danwerner21/TI99_22/images/d.jpg

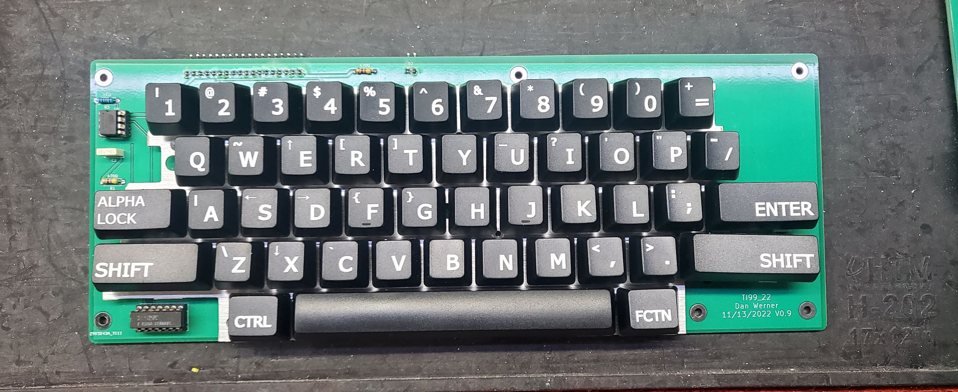
images/d.jpg
