danwerner21/TI99_22/IORiser/IO_Riser/IO_RISERPCBV0.5.pdf

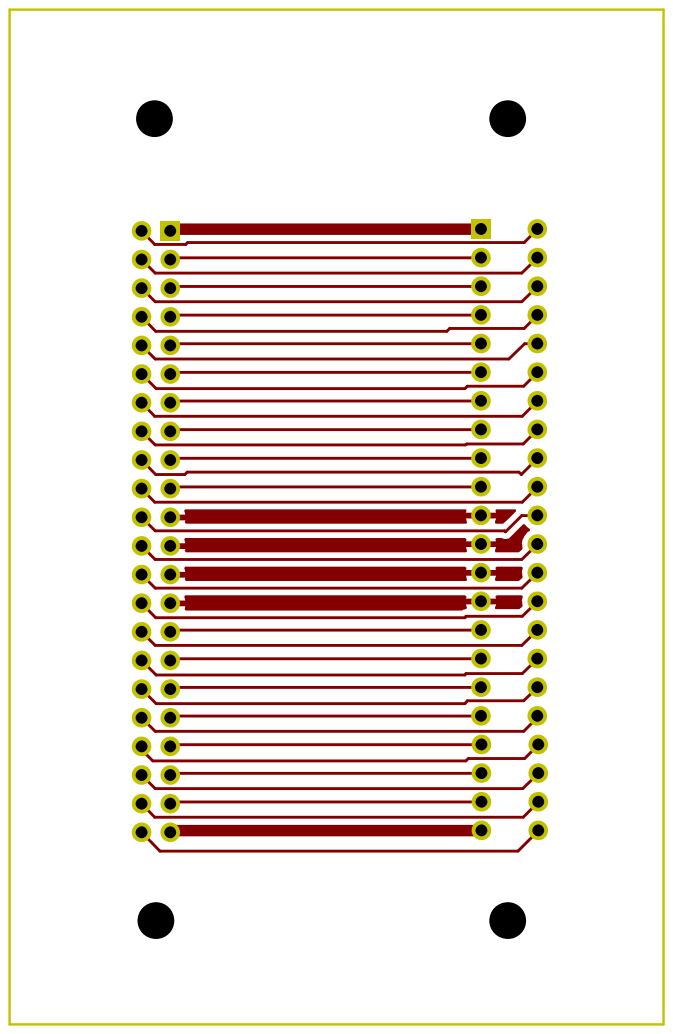
[picture p63: page 1]

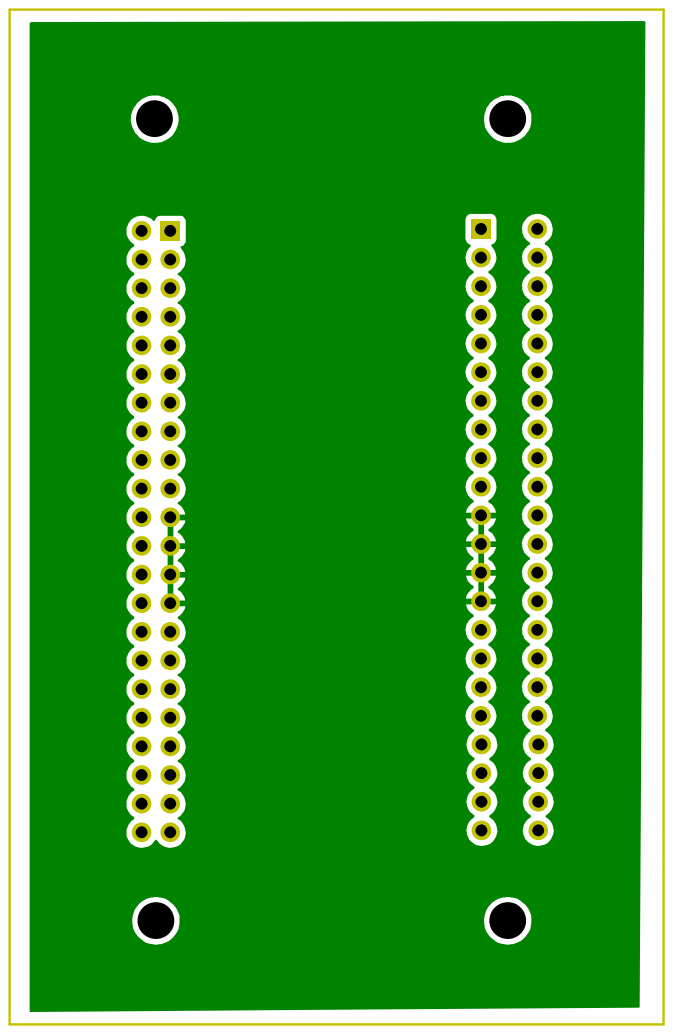
[picture p64: page 2]

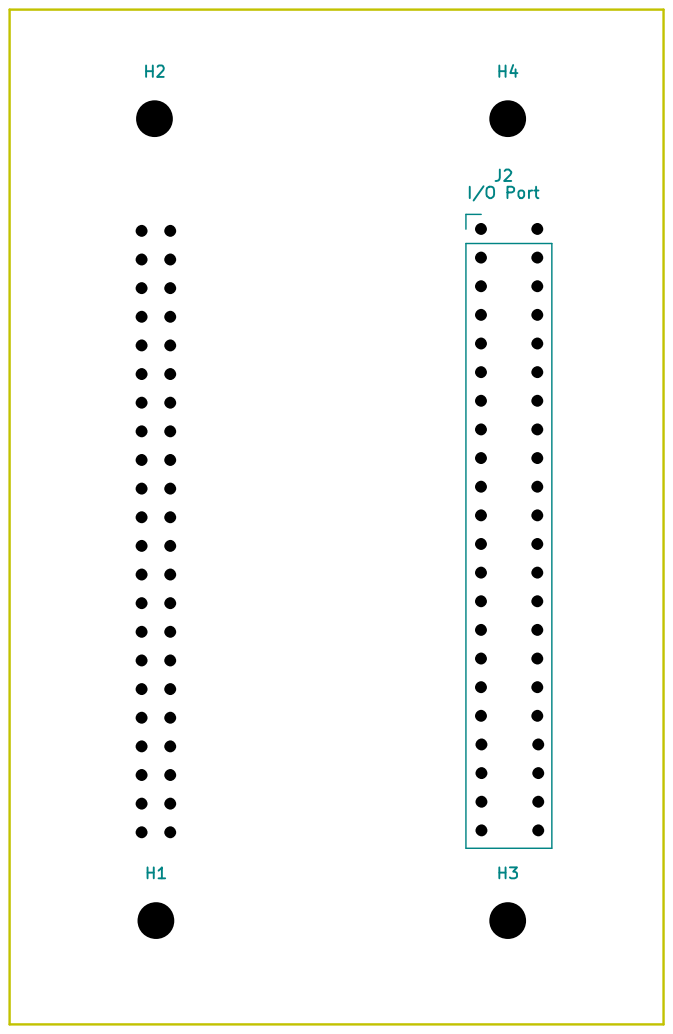
[picture p65: page 3]

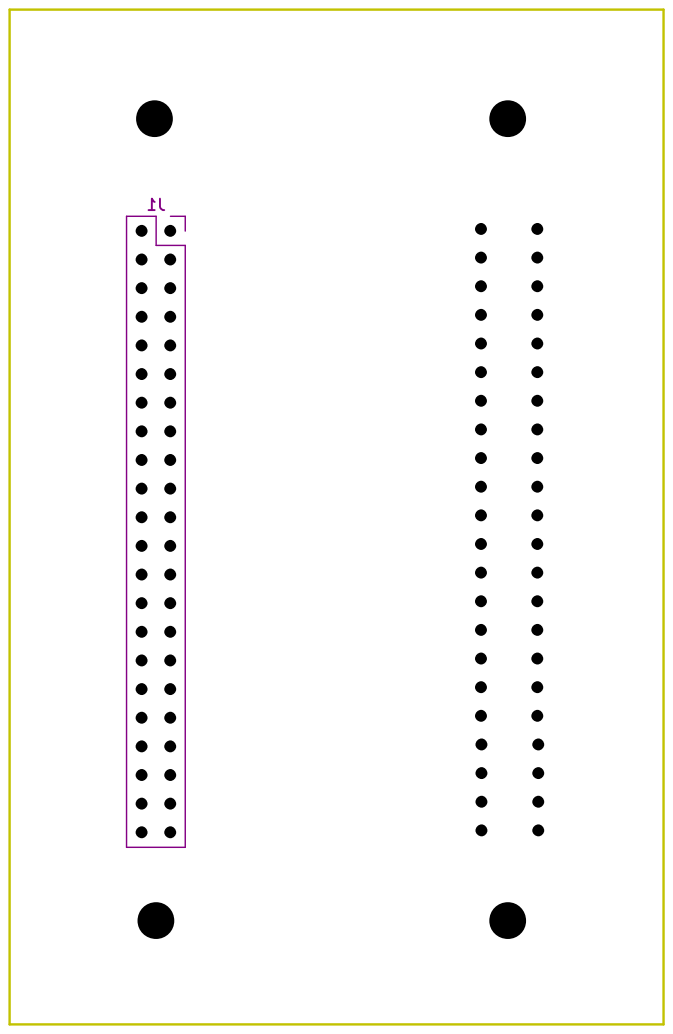
[picture p66: page 4]

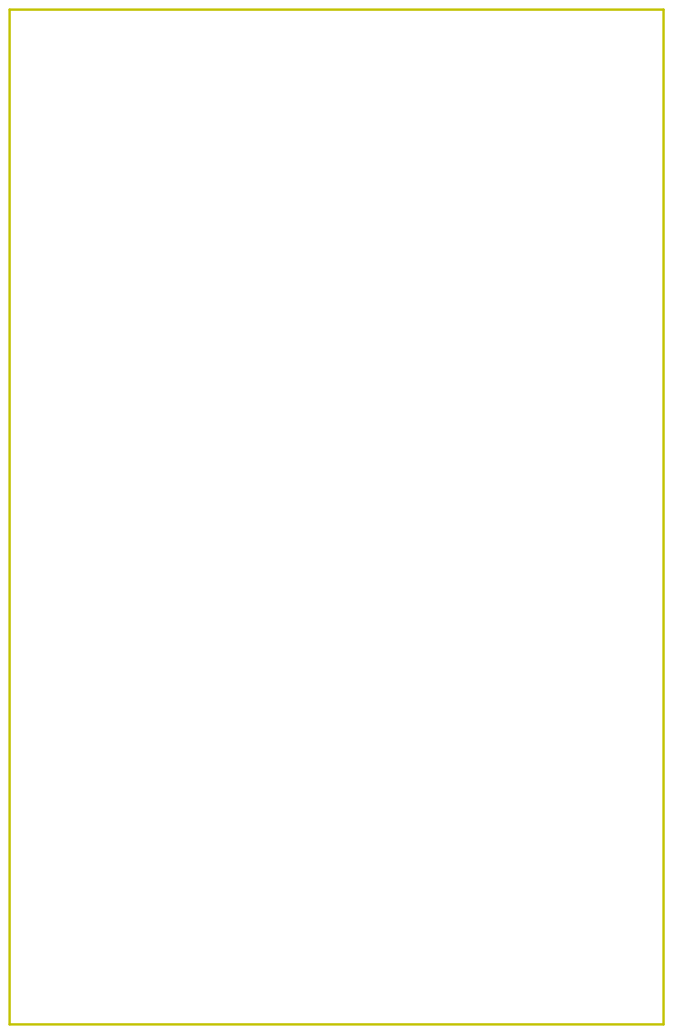
[picture p67: page 5]
