danwerner21/TI99_22/IORiser/IO_Riser/IO_RISERV0.5.pdf

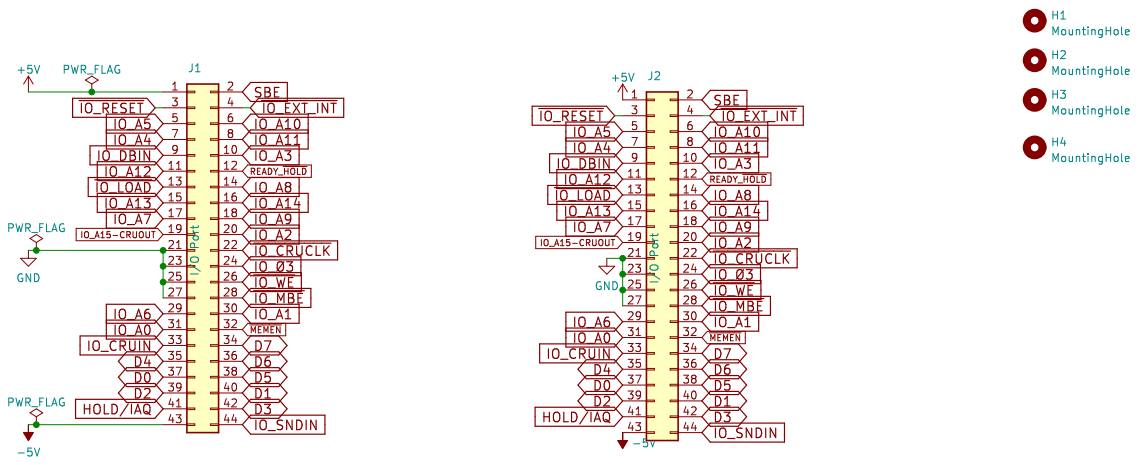
[picture p68: page 1]
