danwerner21/TI99_22/mainboard/mainboard_pcb_v0.95.pdf

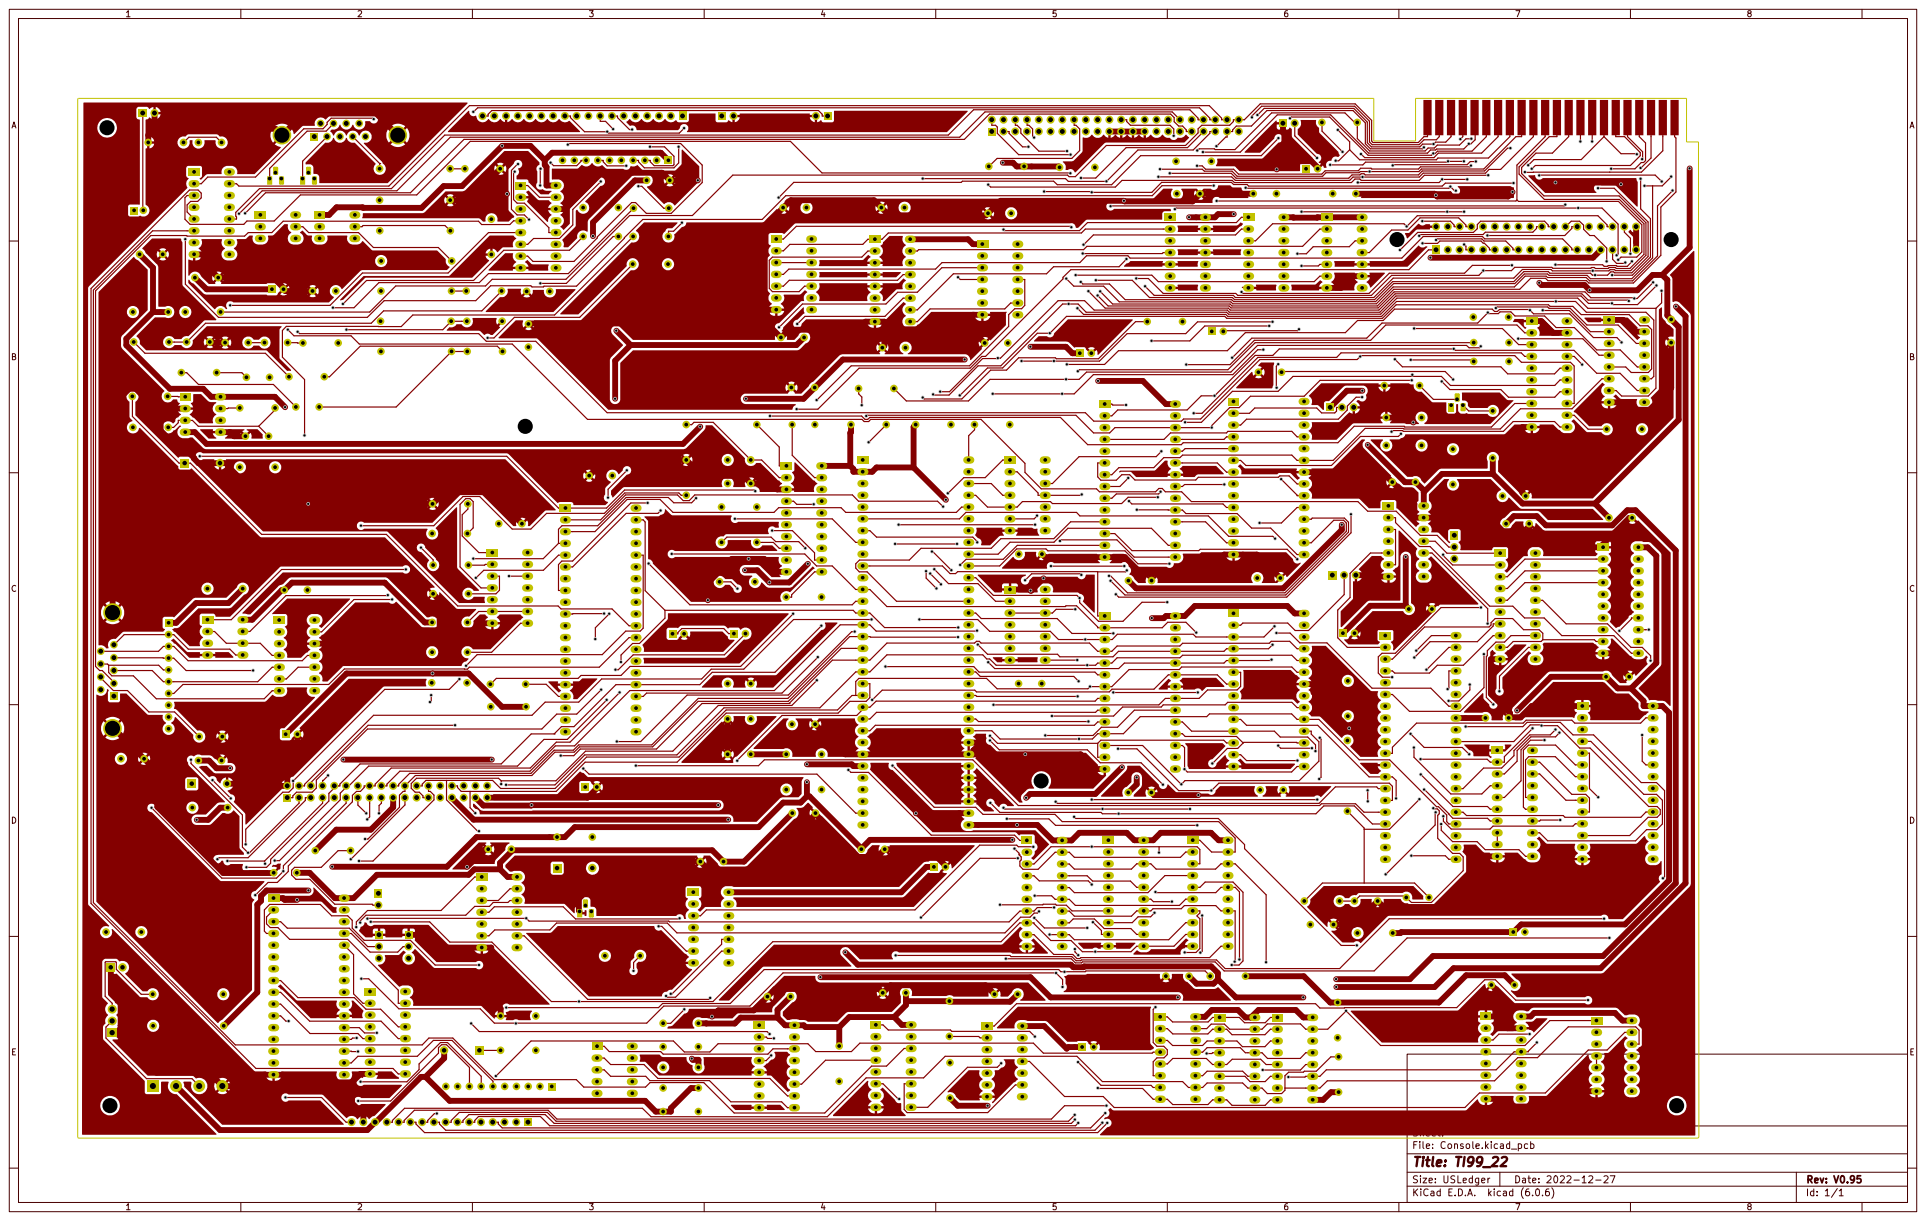
[picture p69: page 1]

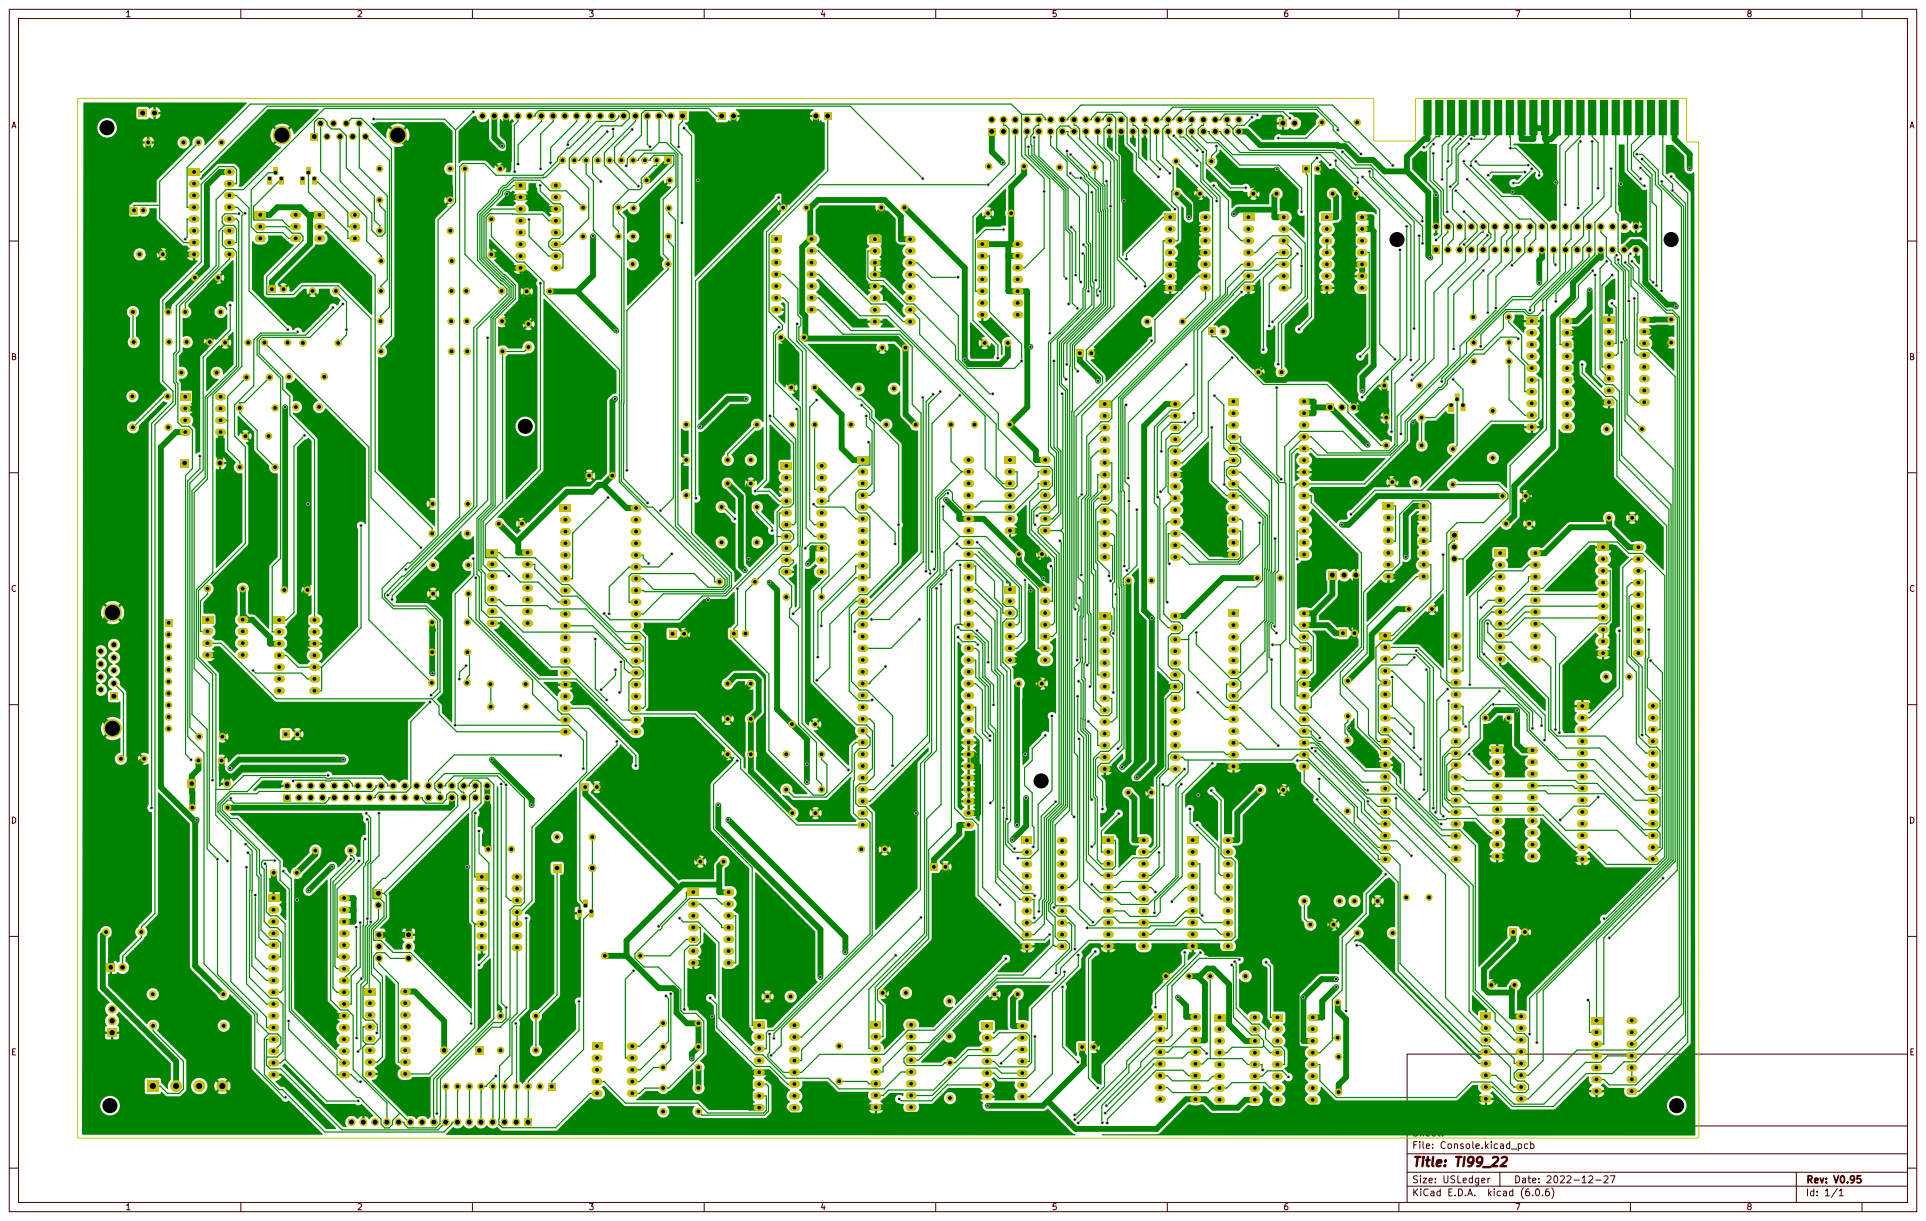
[picture p70: page 2]

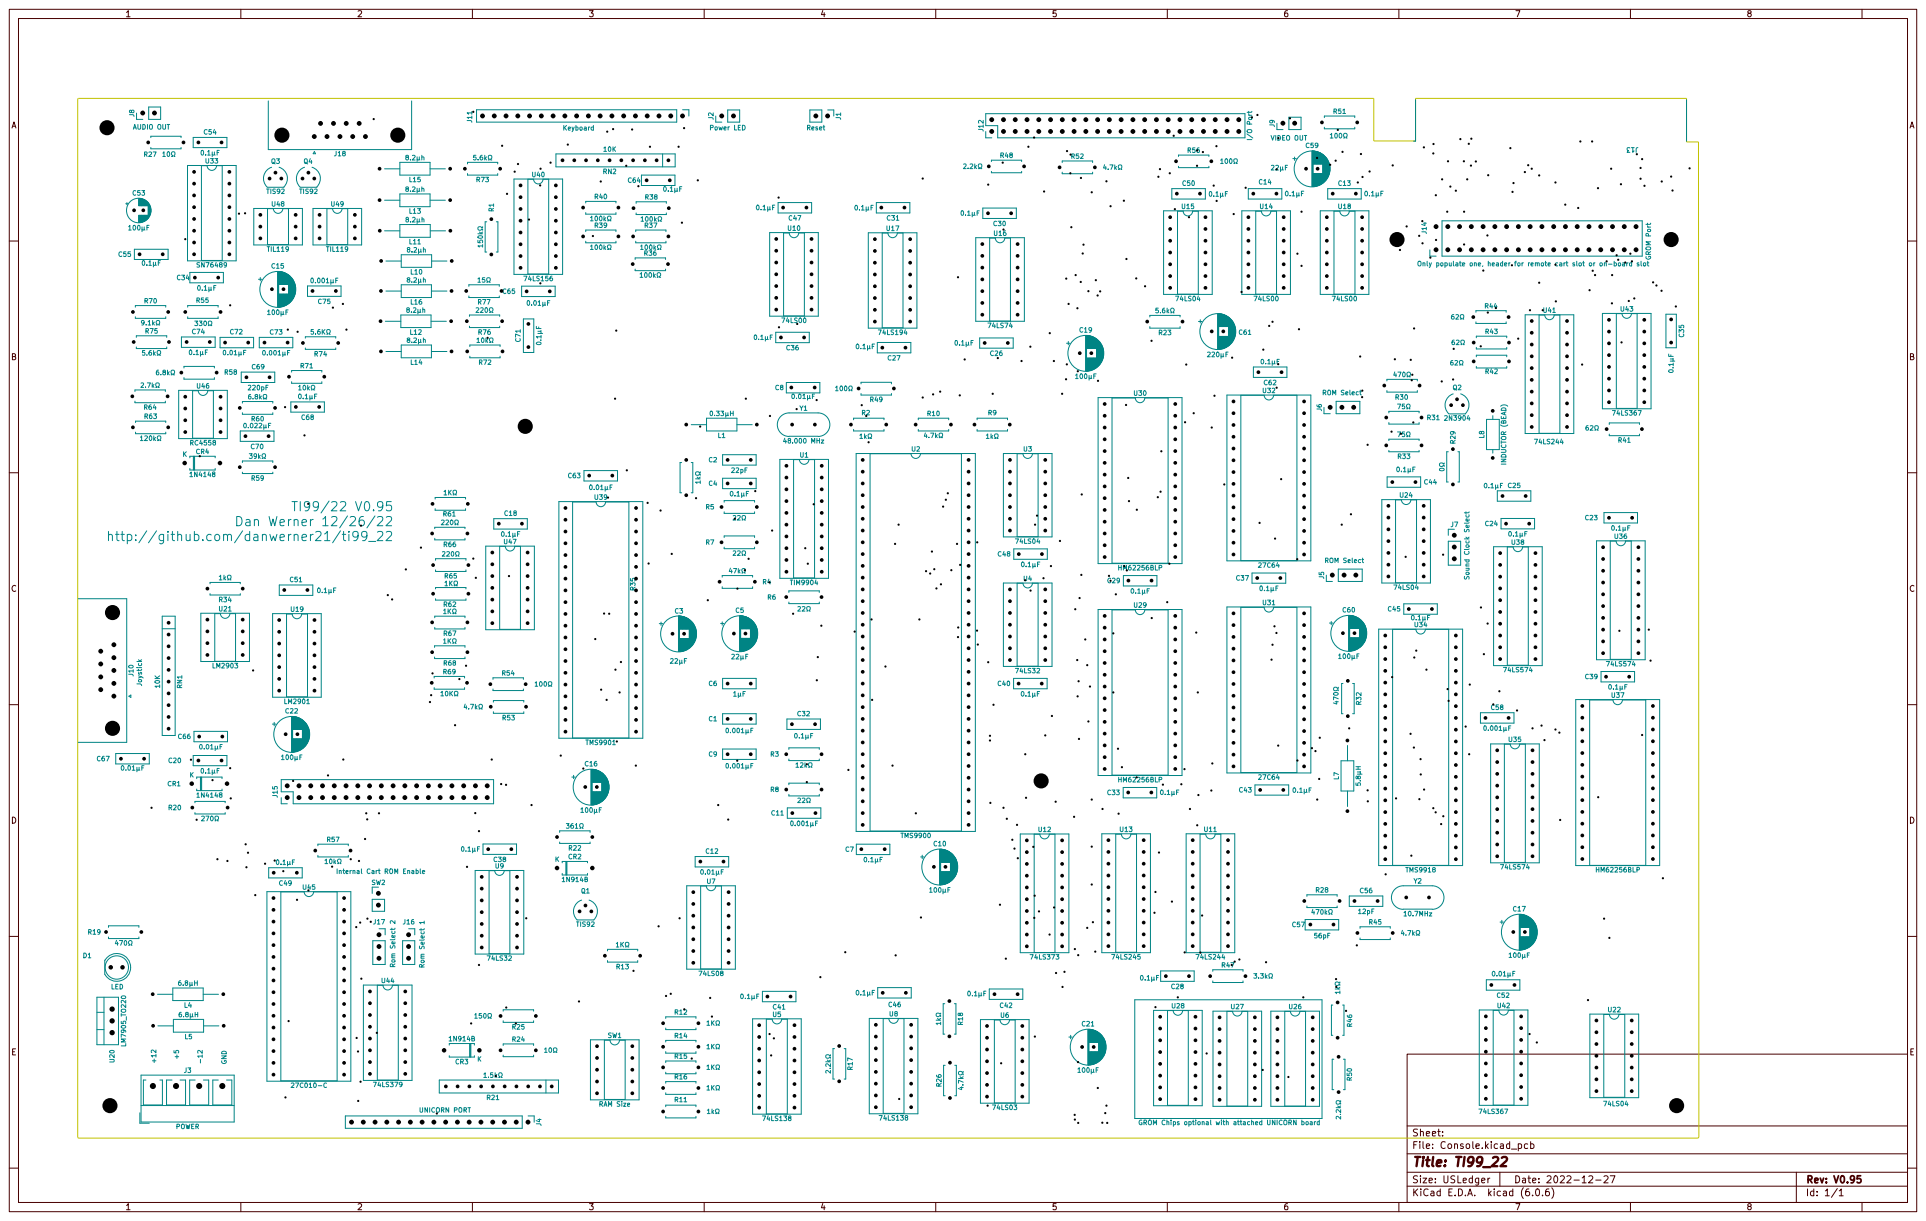
[picture p71: page 3]

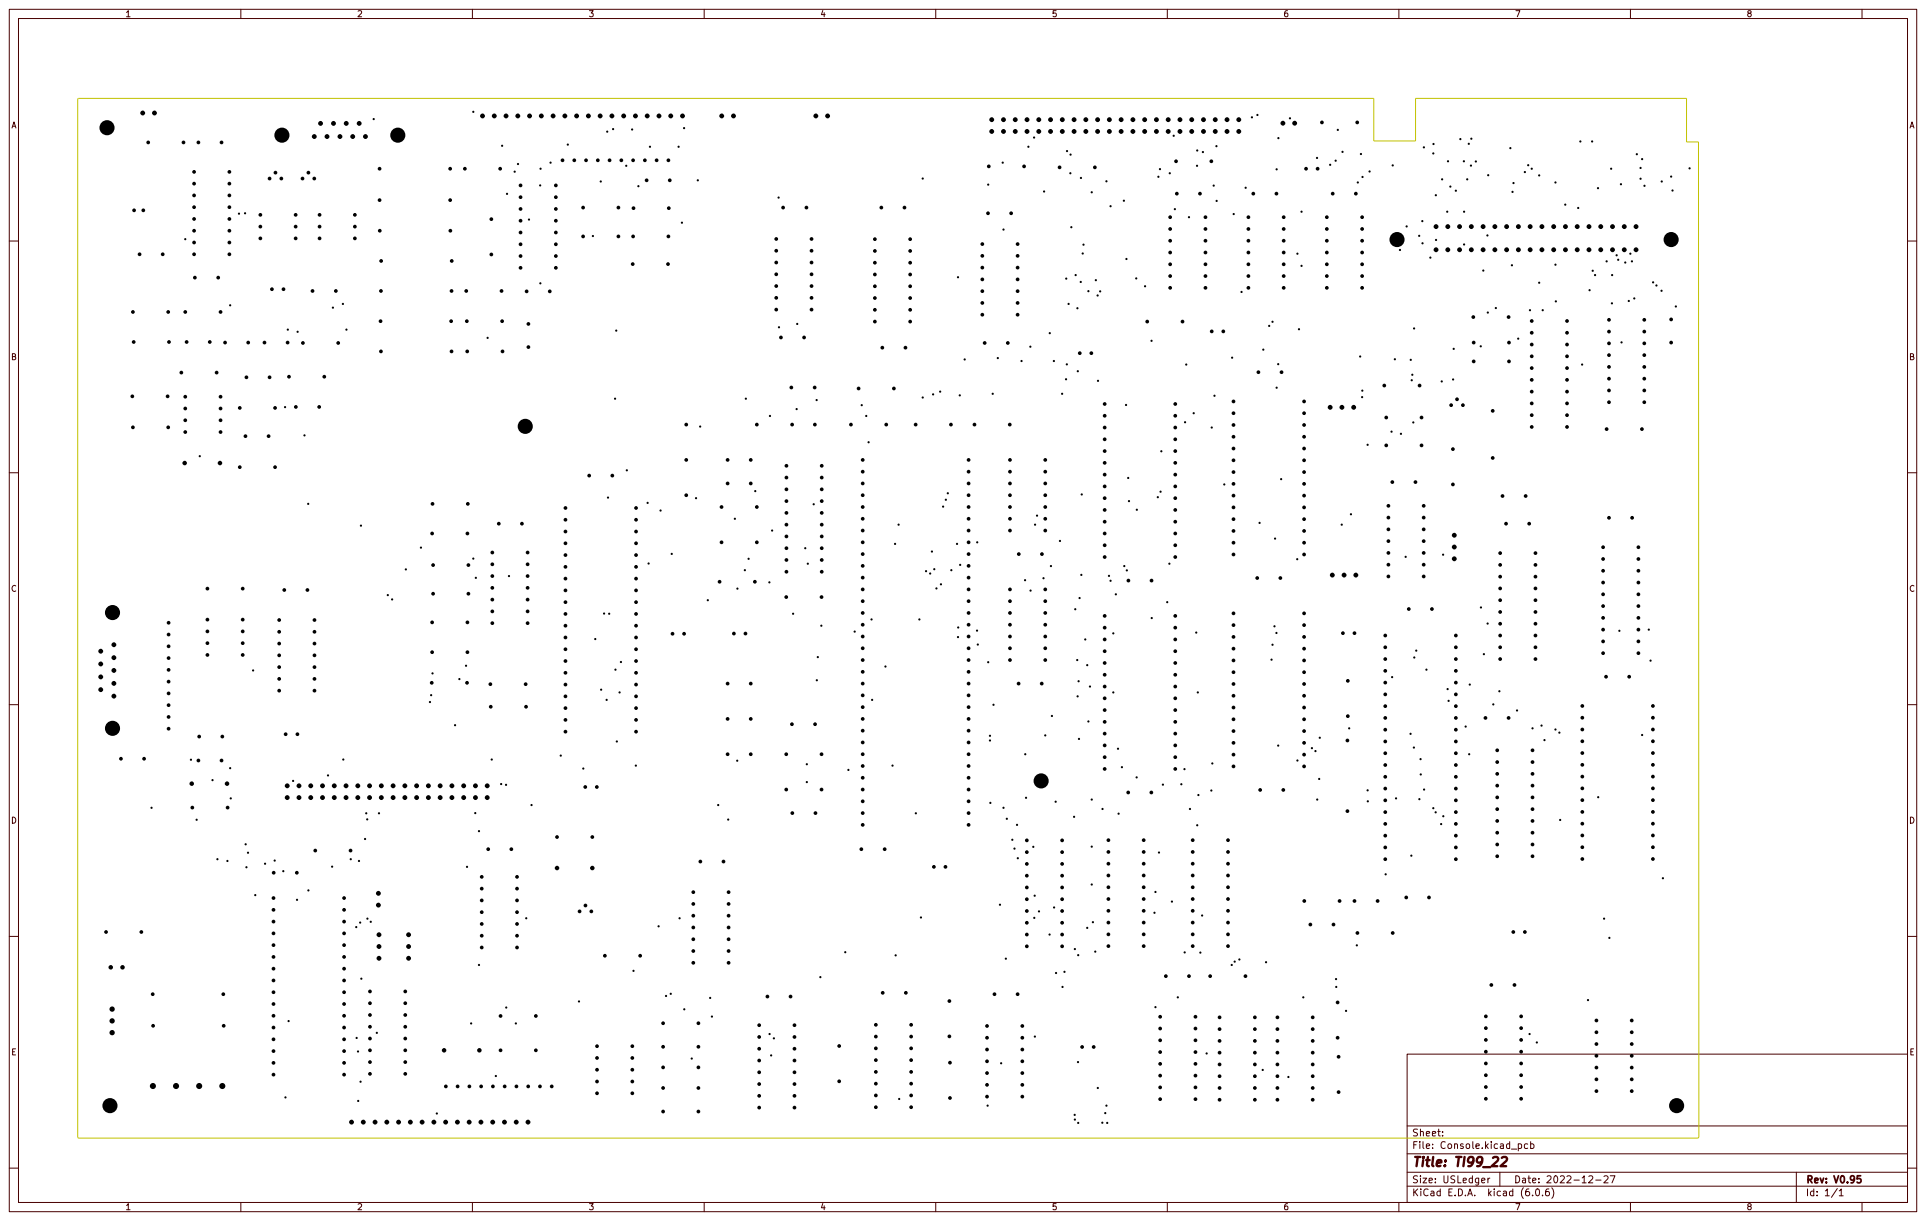
[picture p72: page 4]

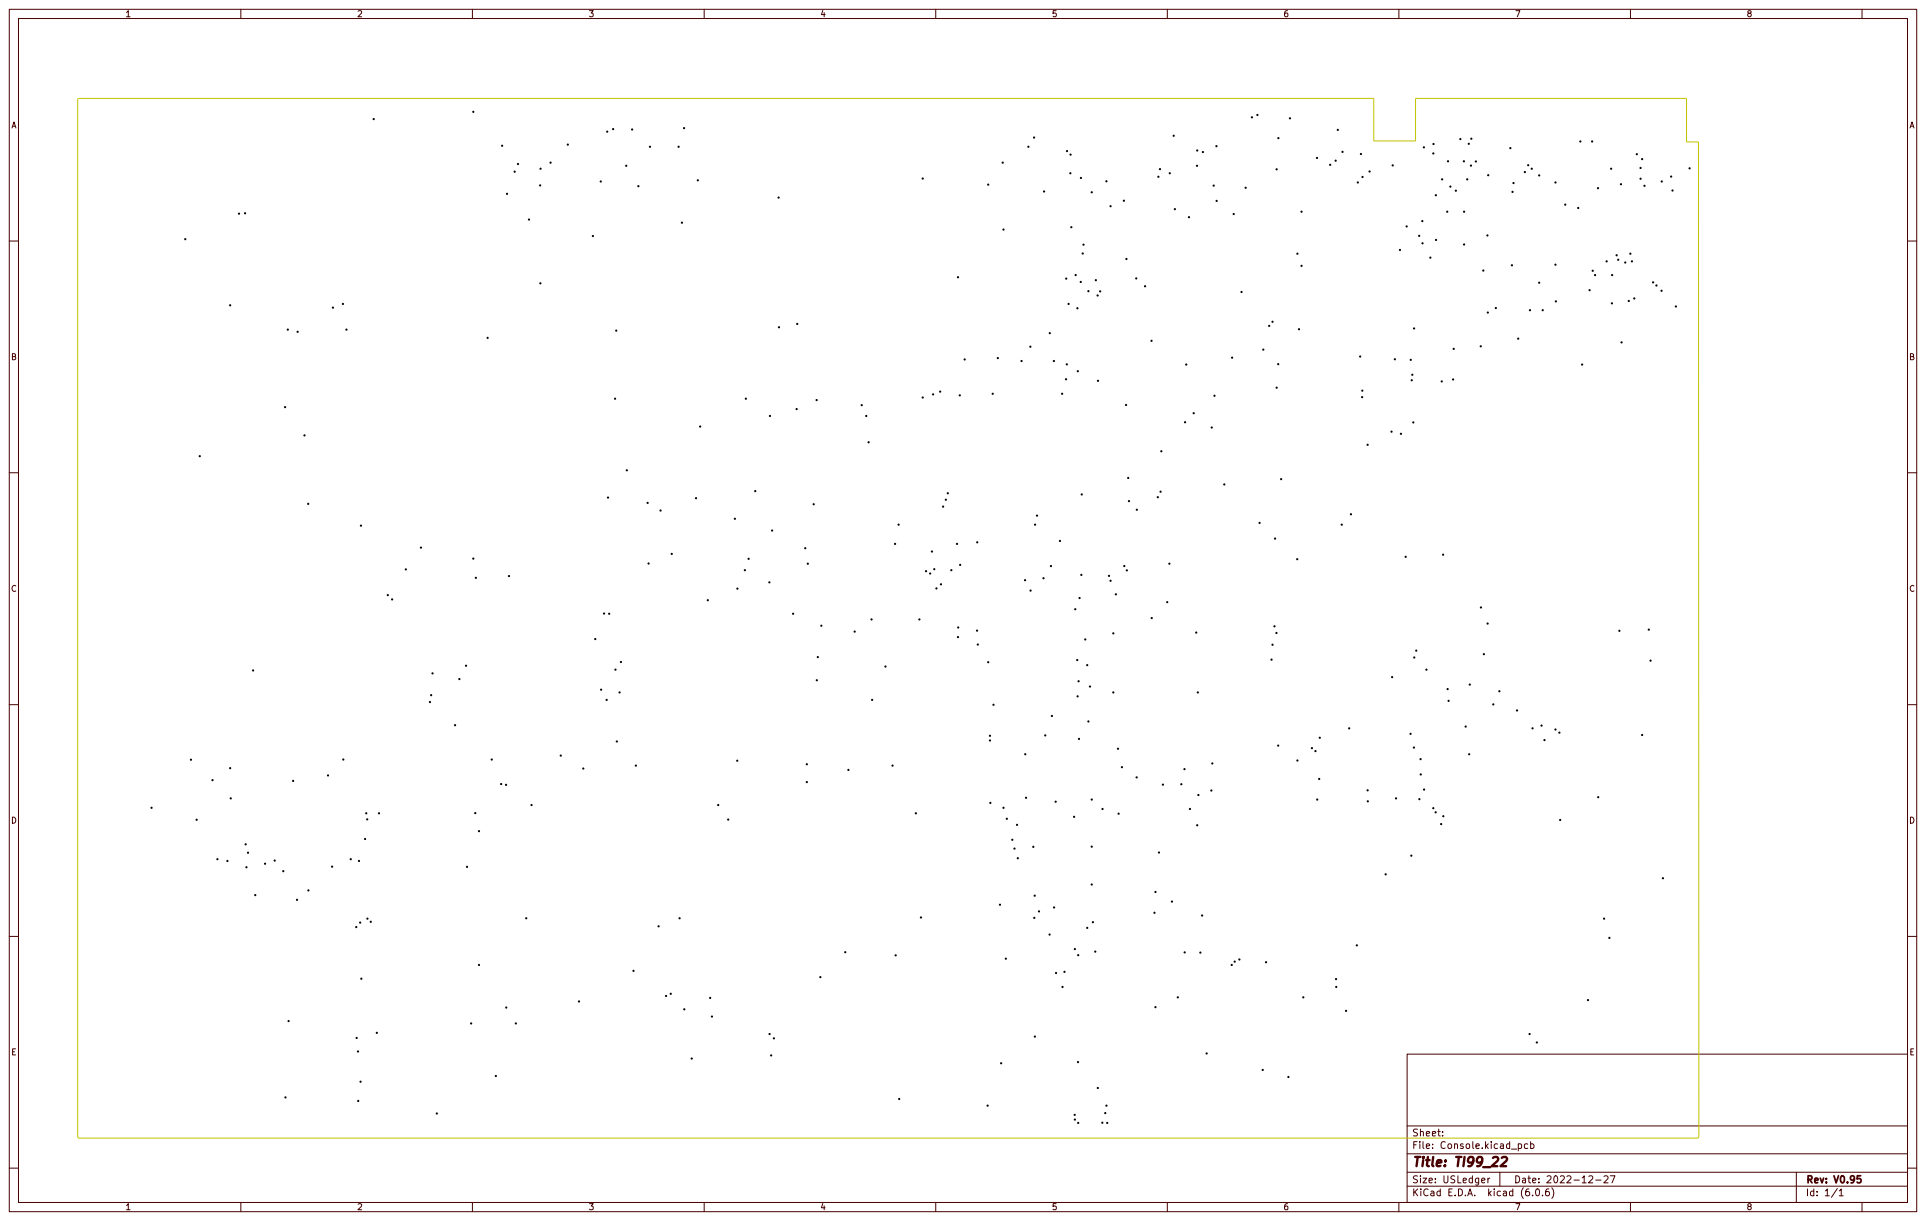
[picture p73: page 5]
