danwerner21/TI99_22/mainboard/mainboard_pcb_v0.90.pdf

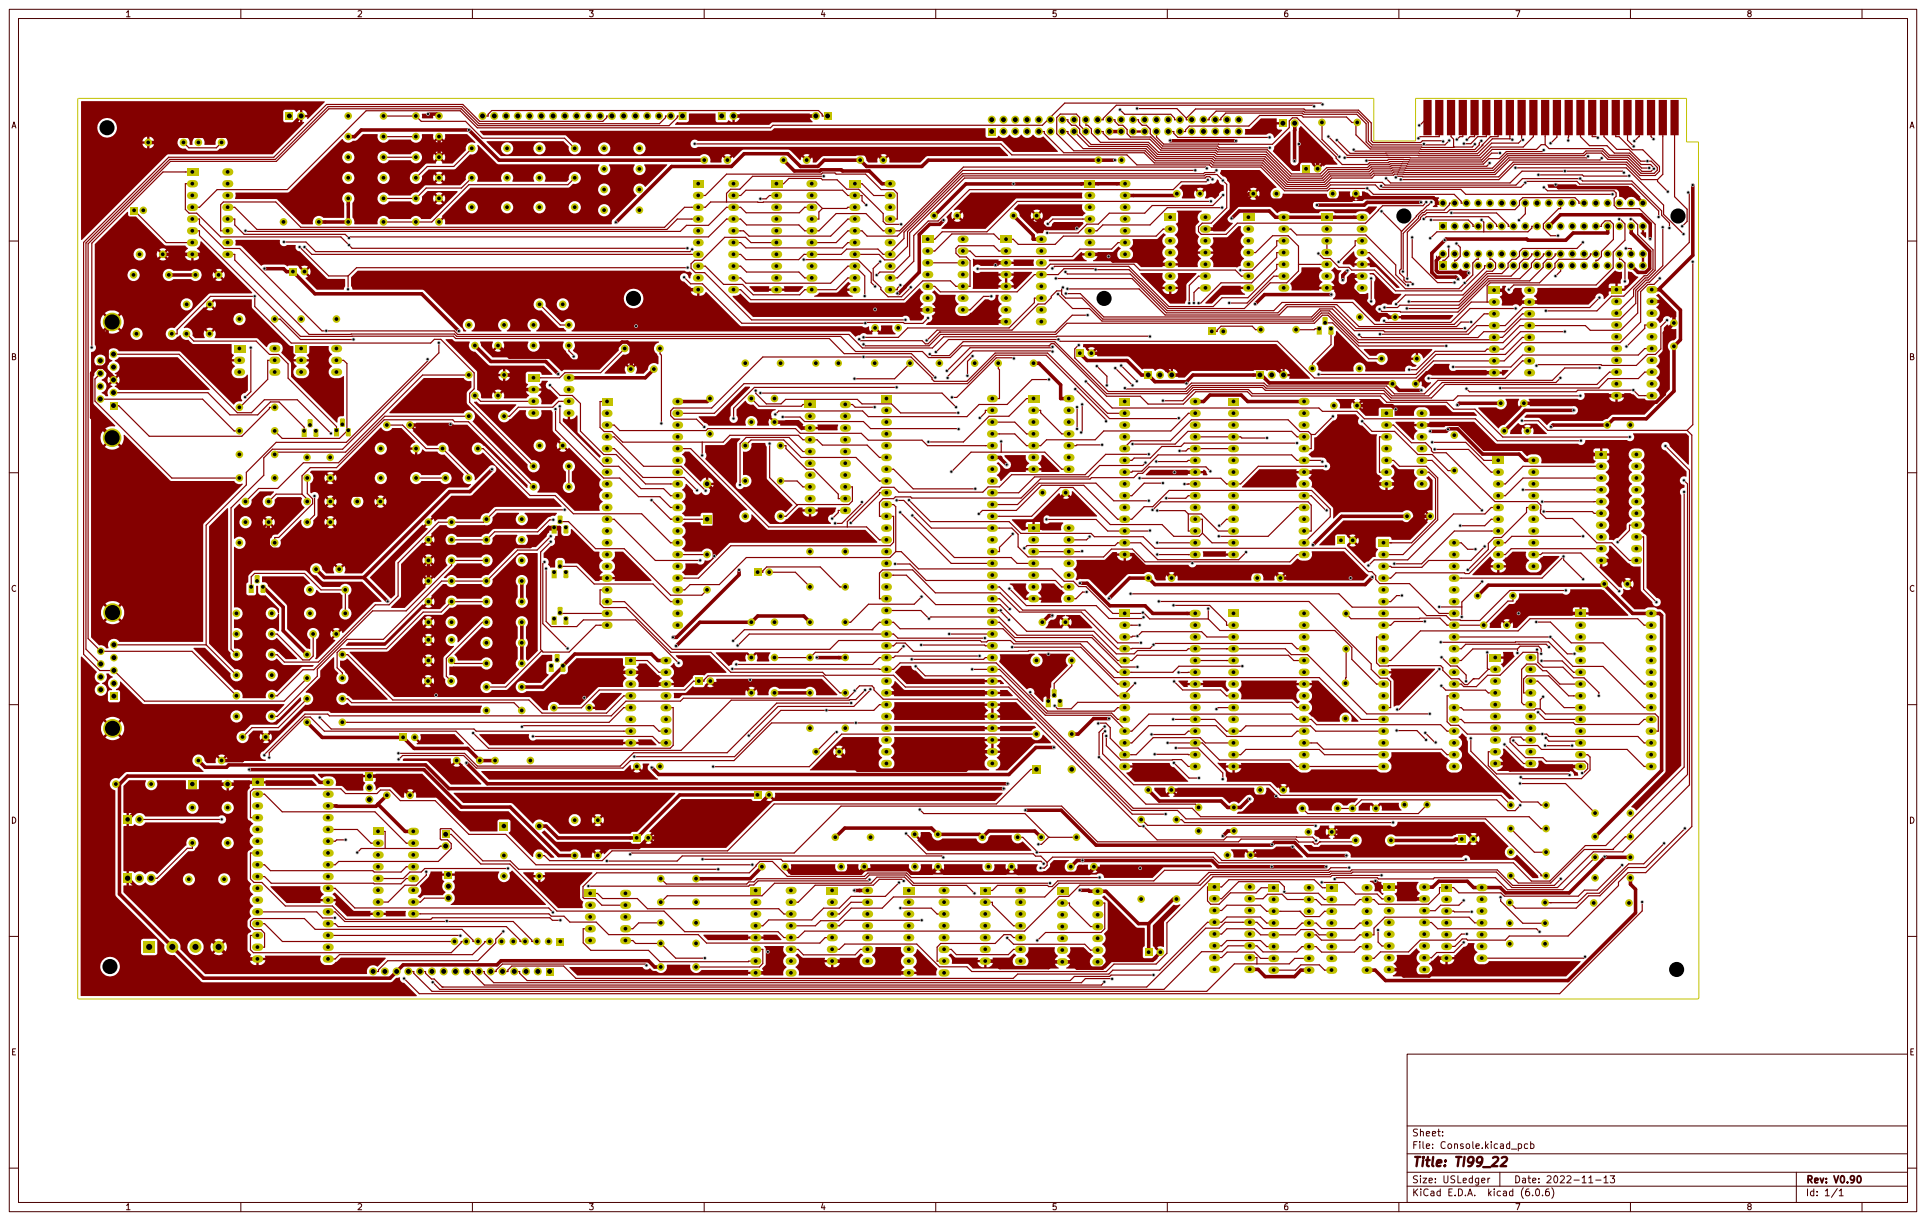
[picture p86: page 1]

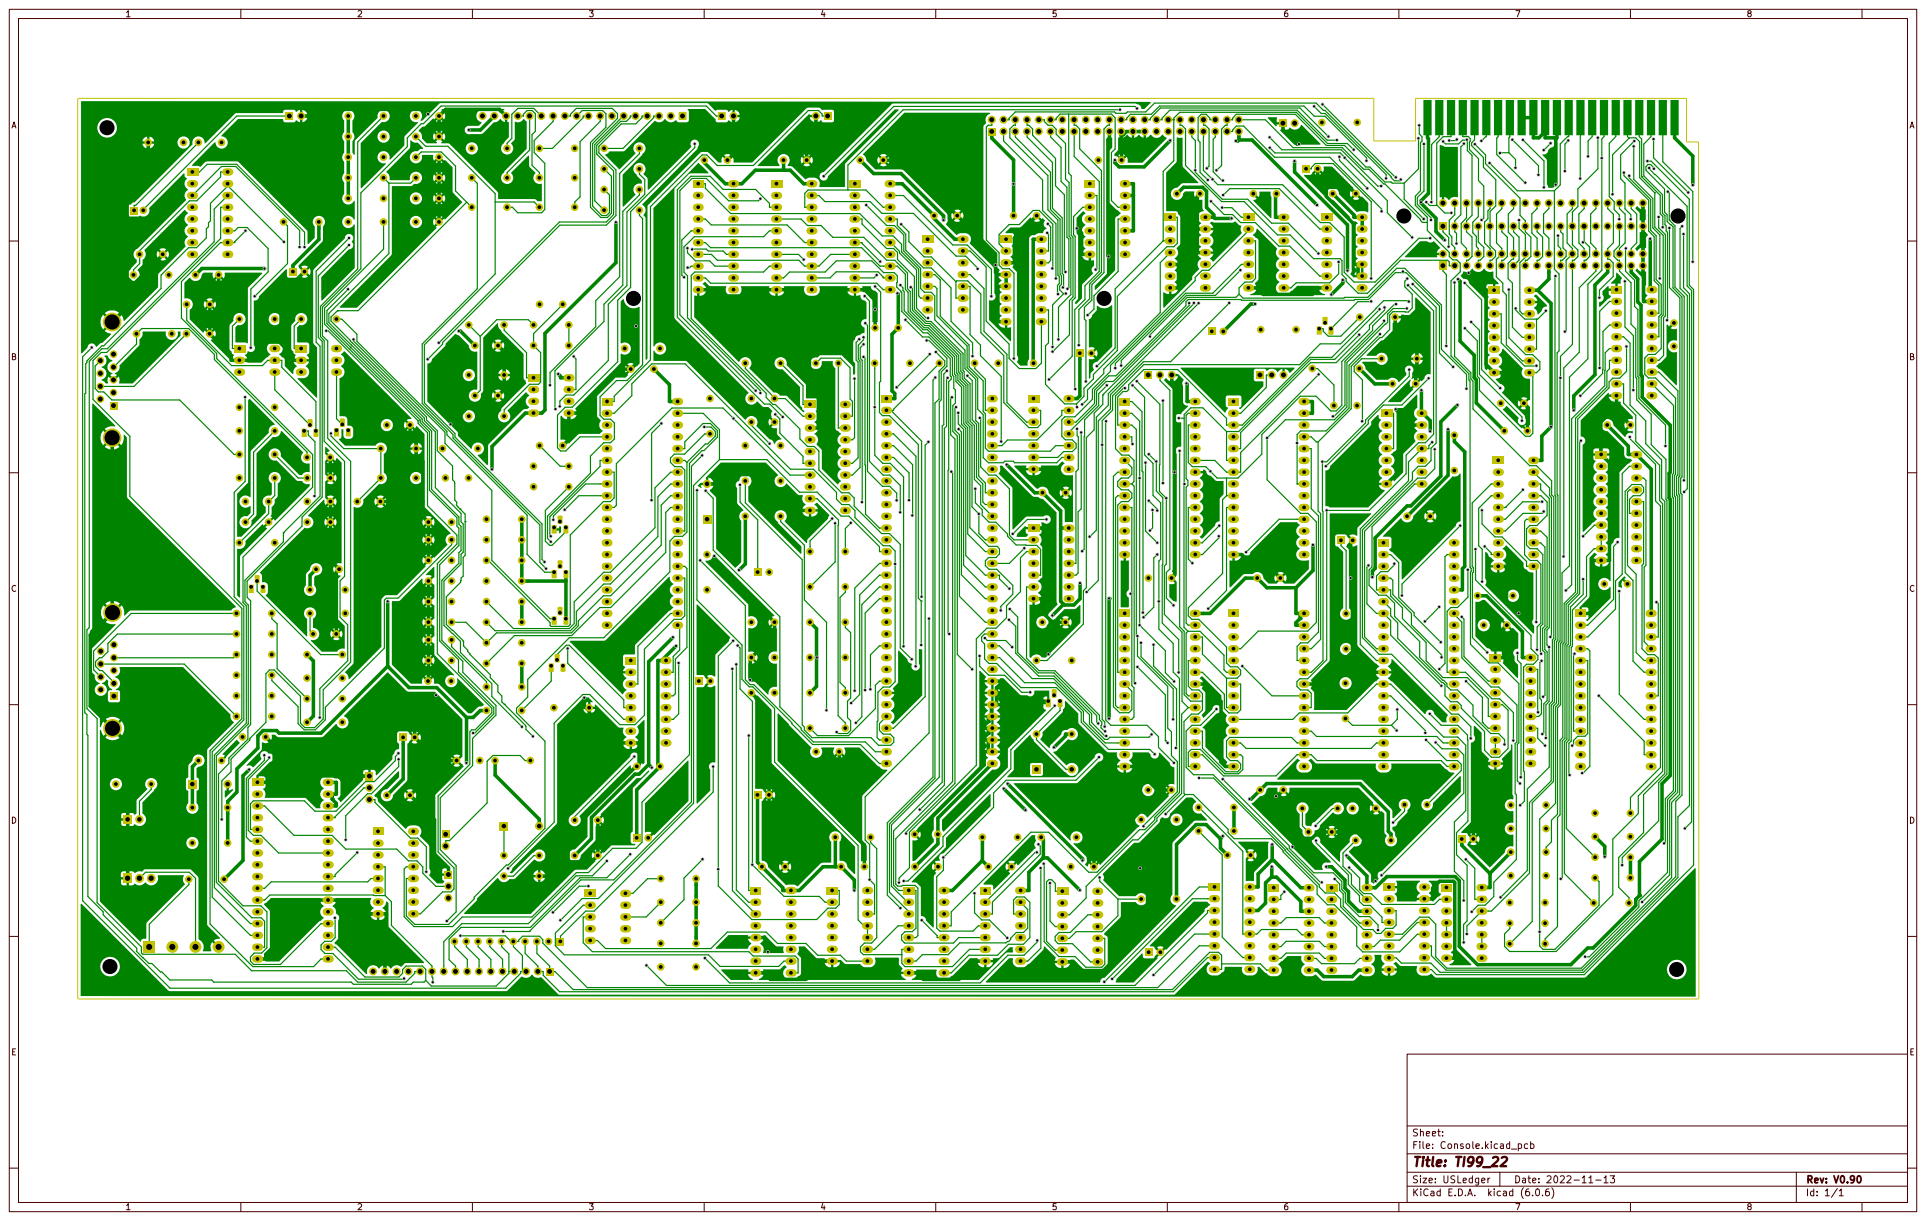
[picture p87: page 2]

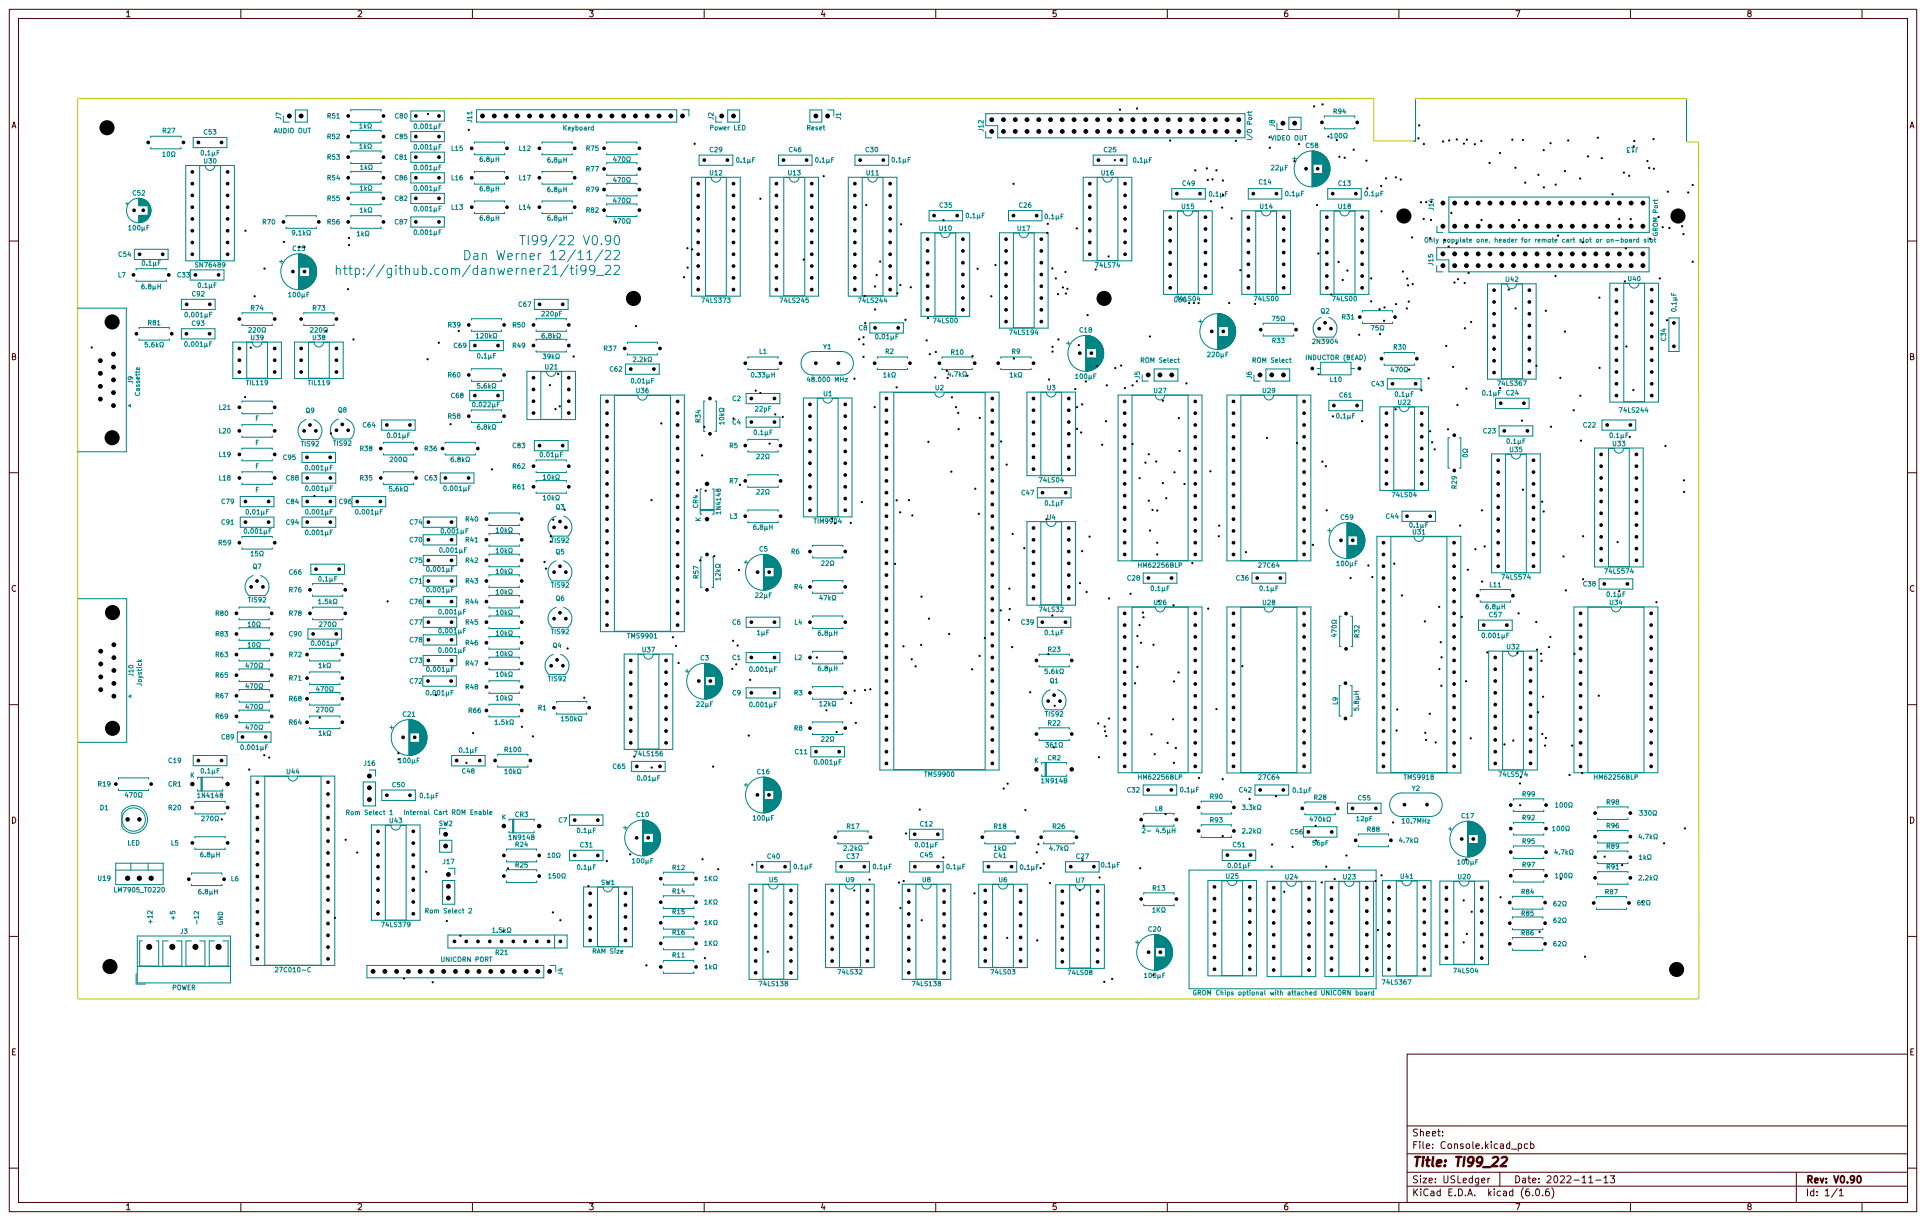
[picture p88: page 3]

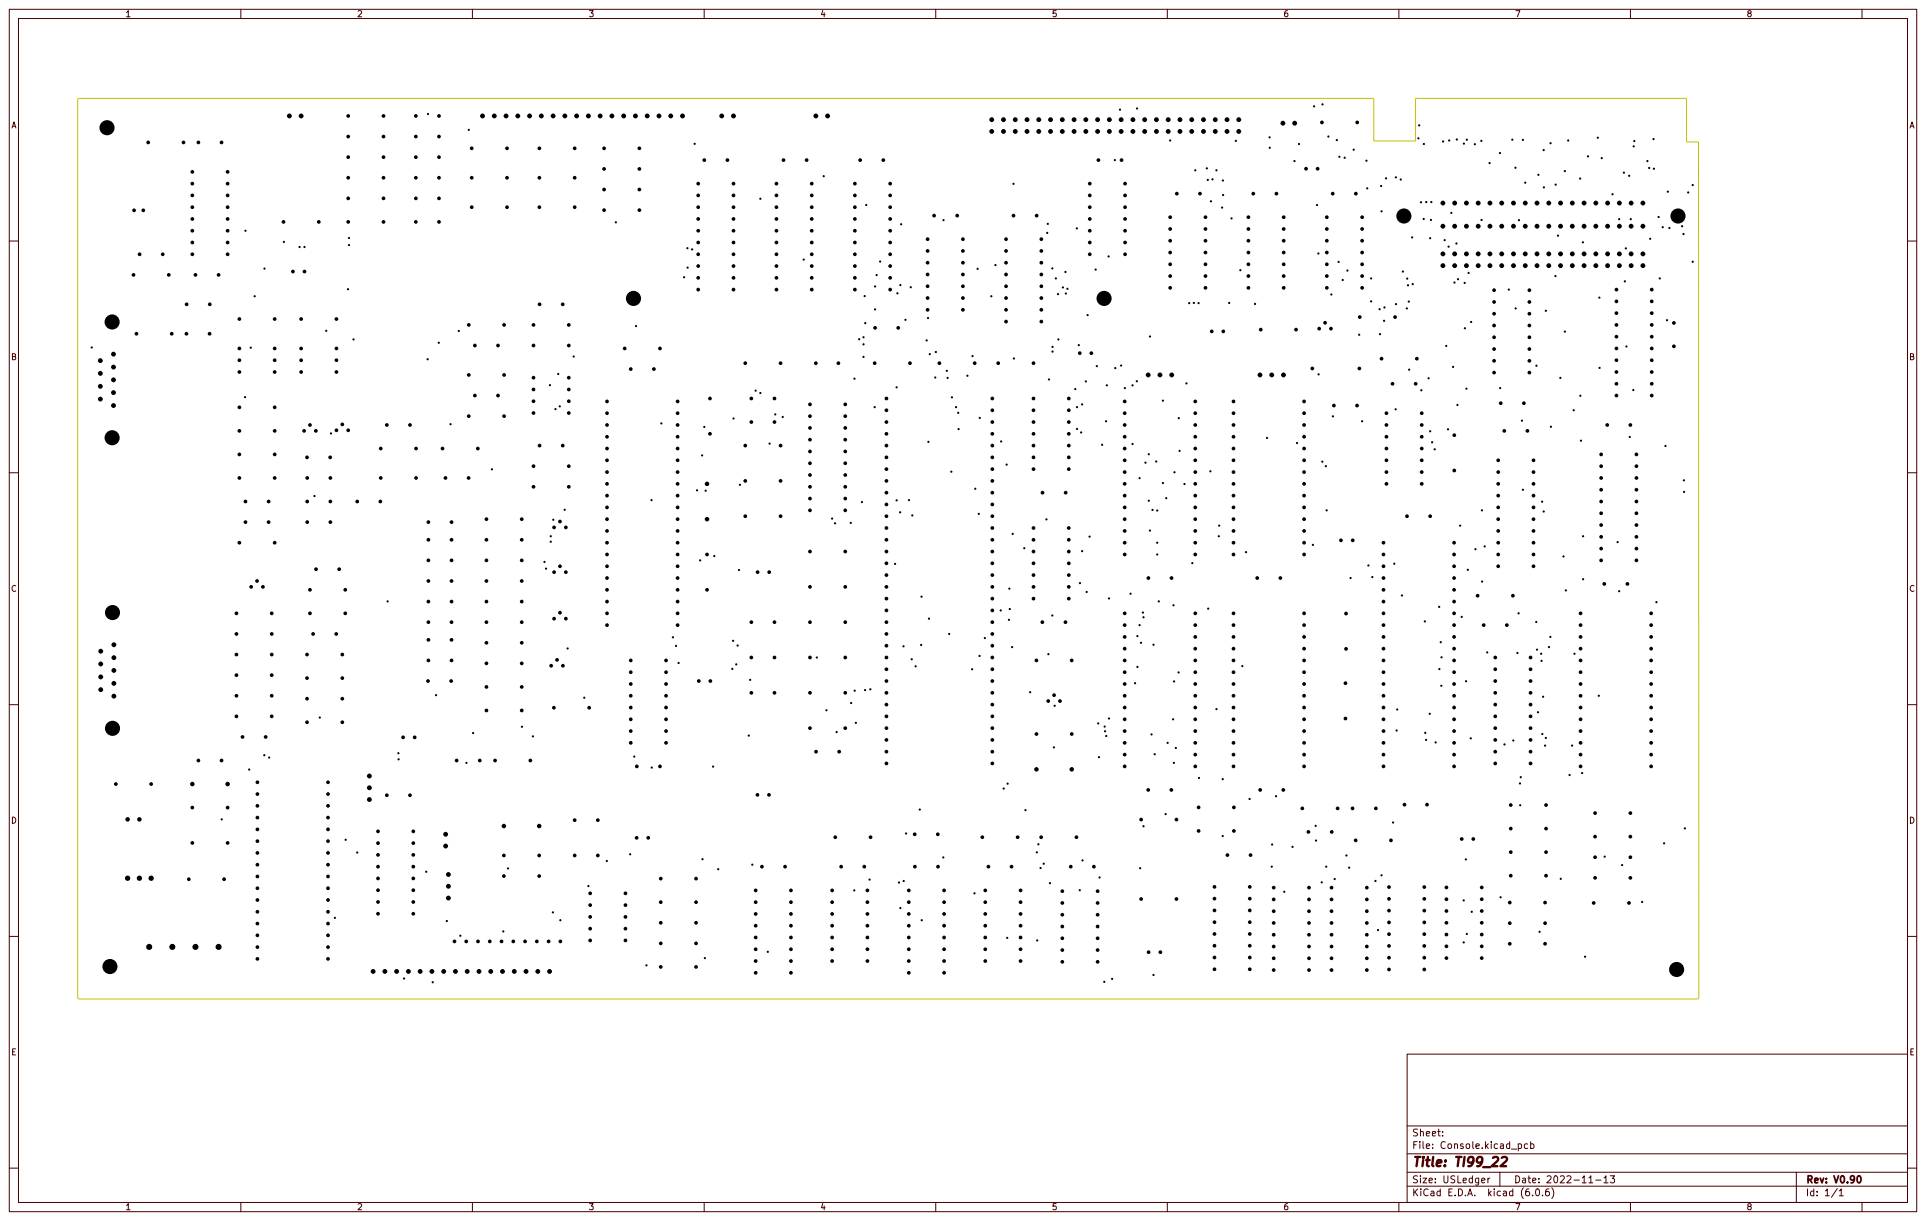
[picture p89: page 4]

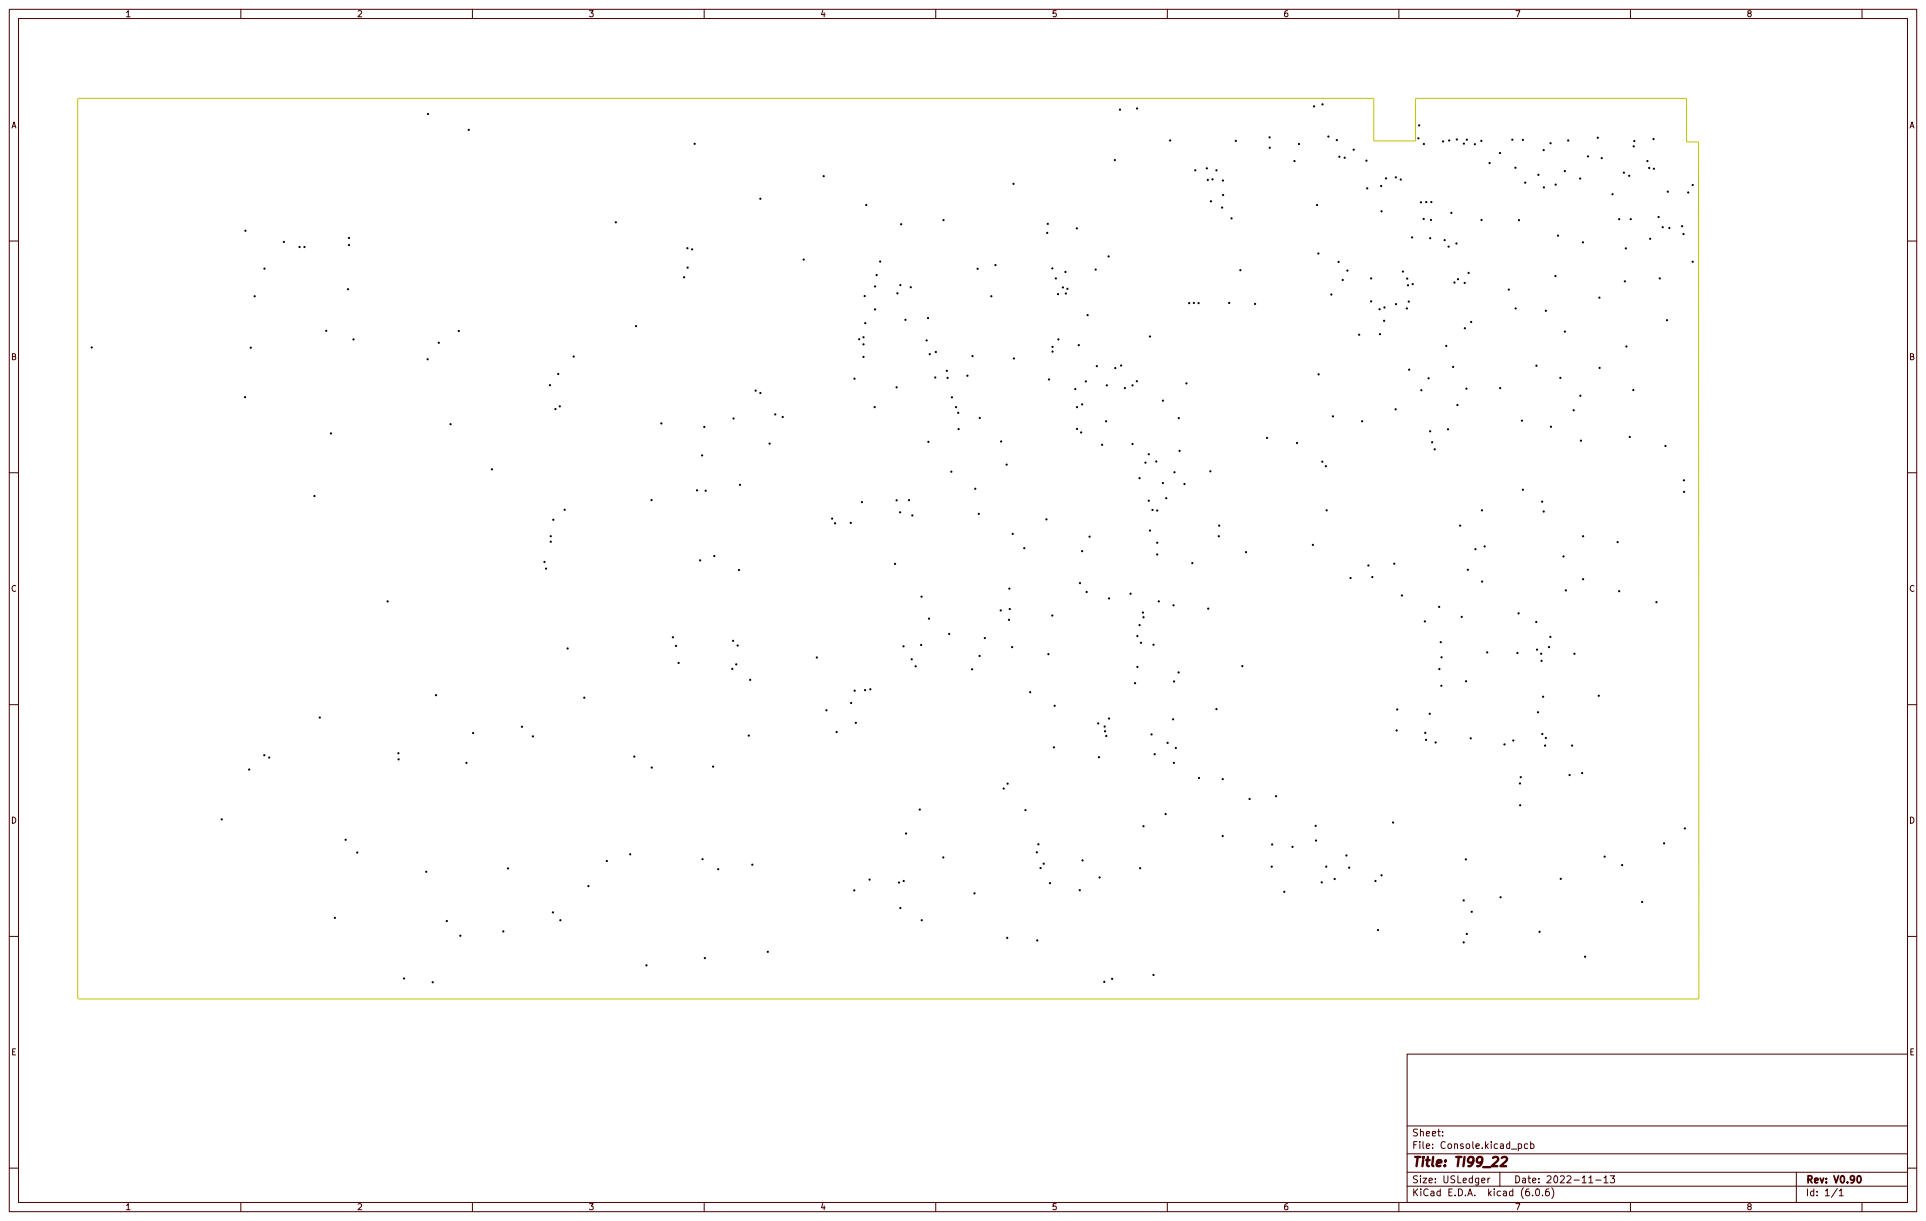
[picture p90: page 5]
