danwerner21/TI99_22/mainboard/mainboard_v0.90.pdf

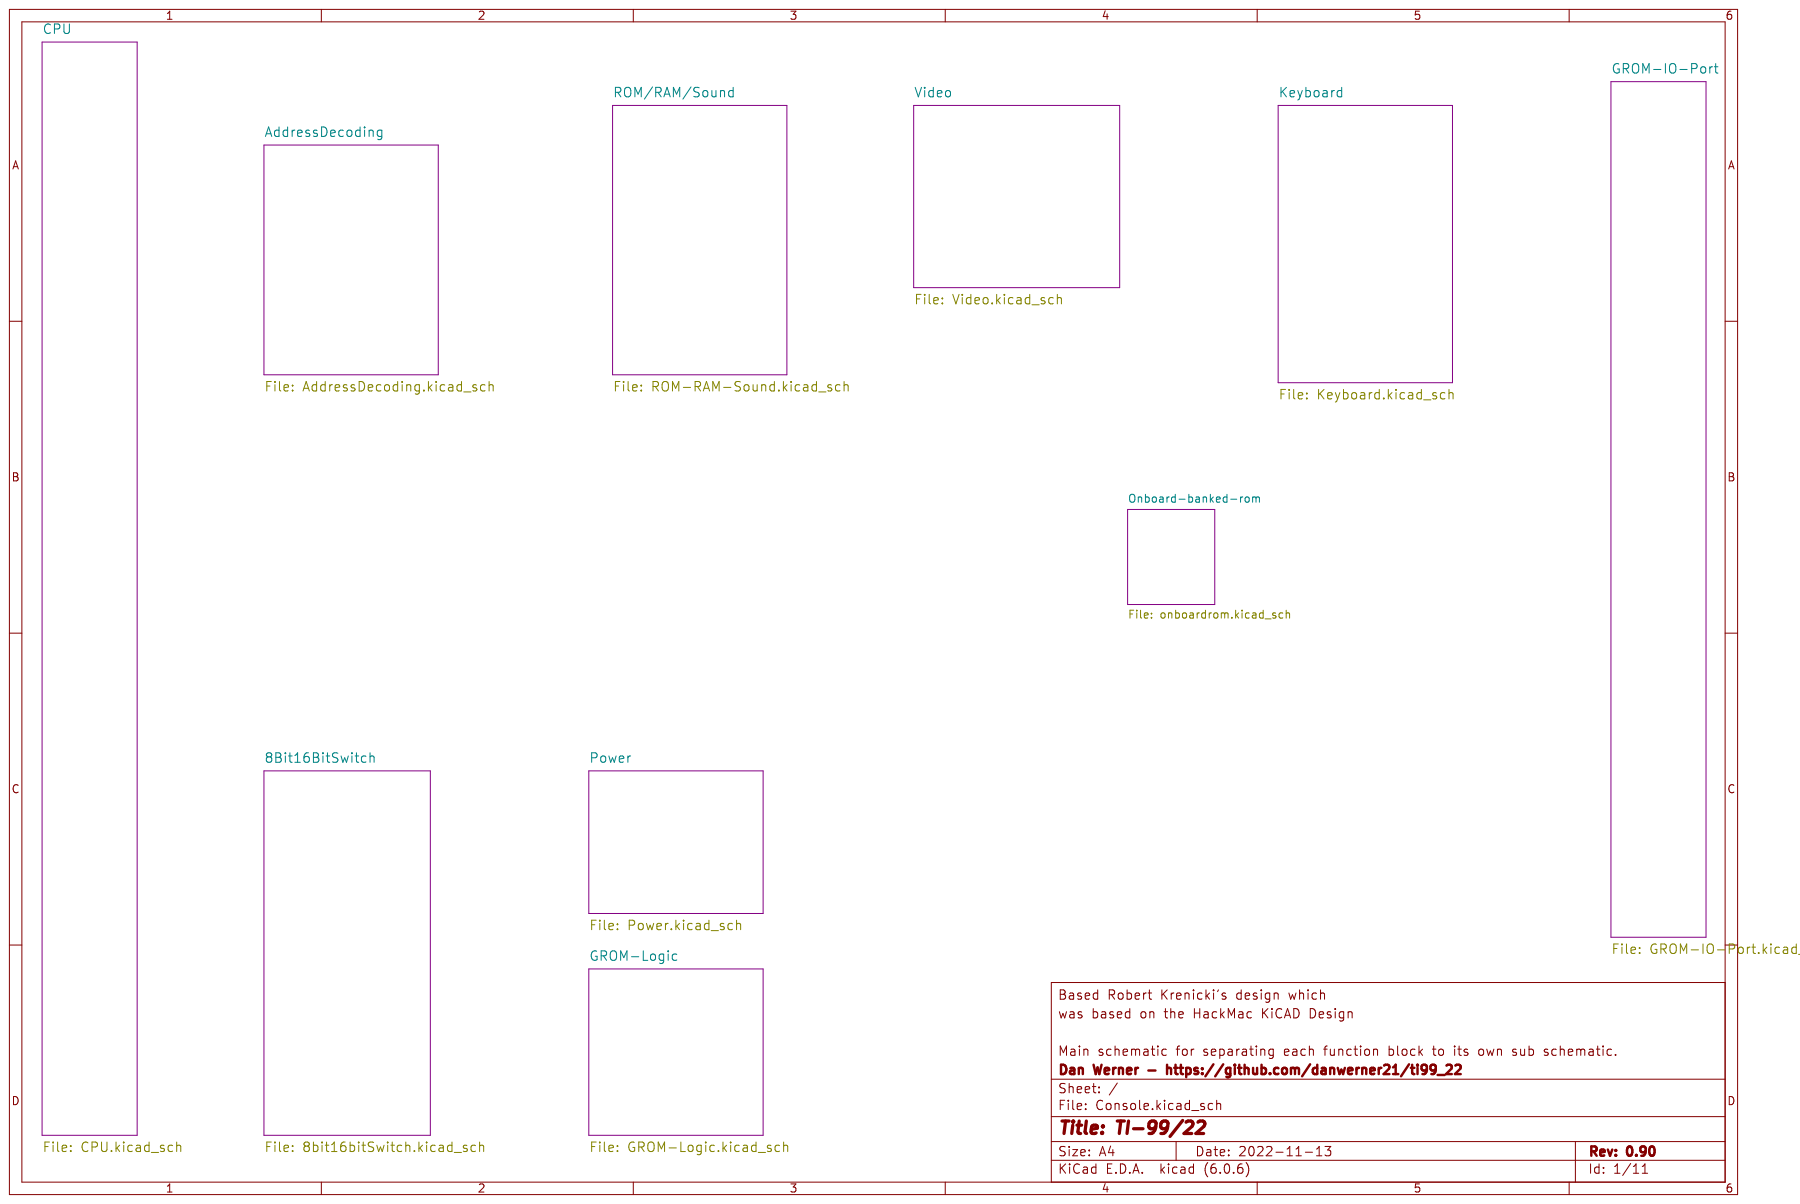
[picture p91: page 1]

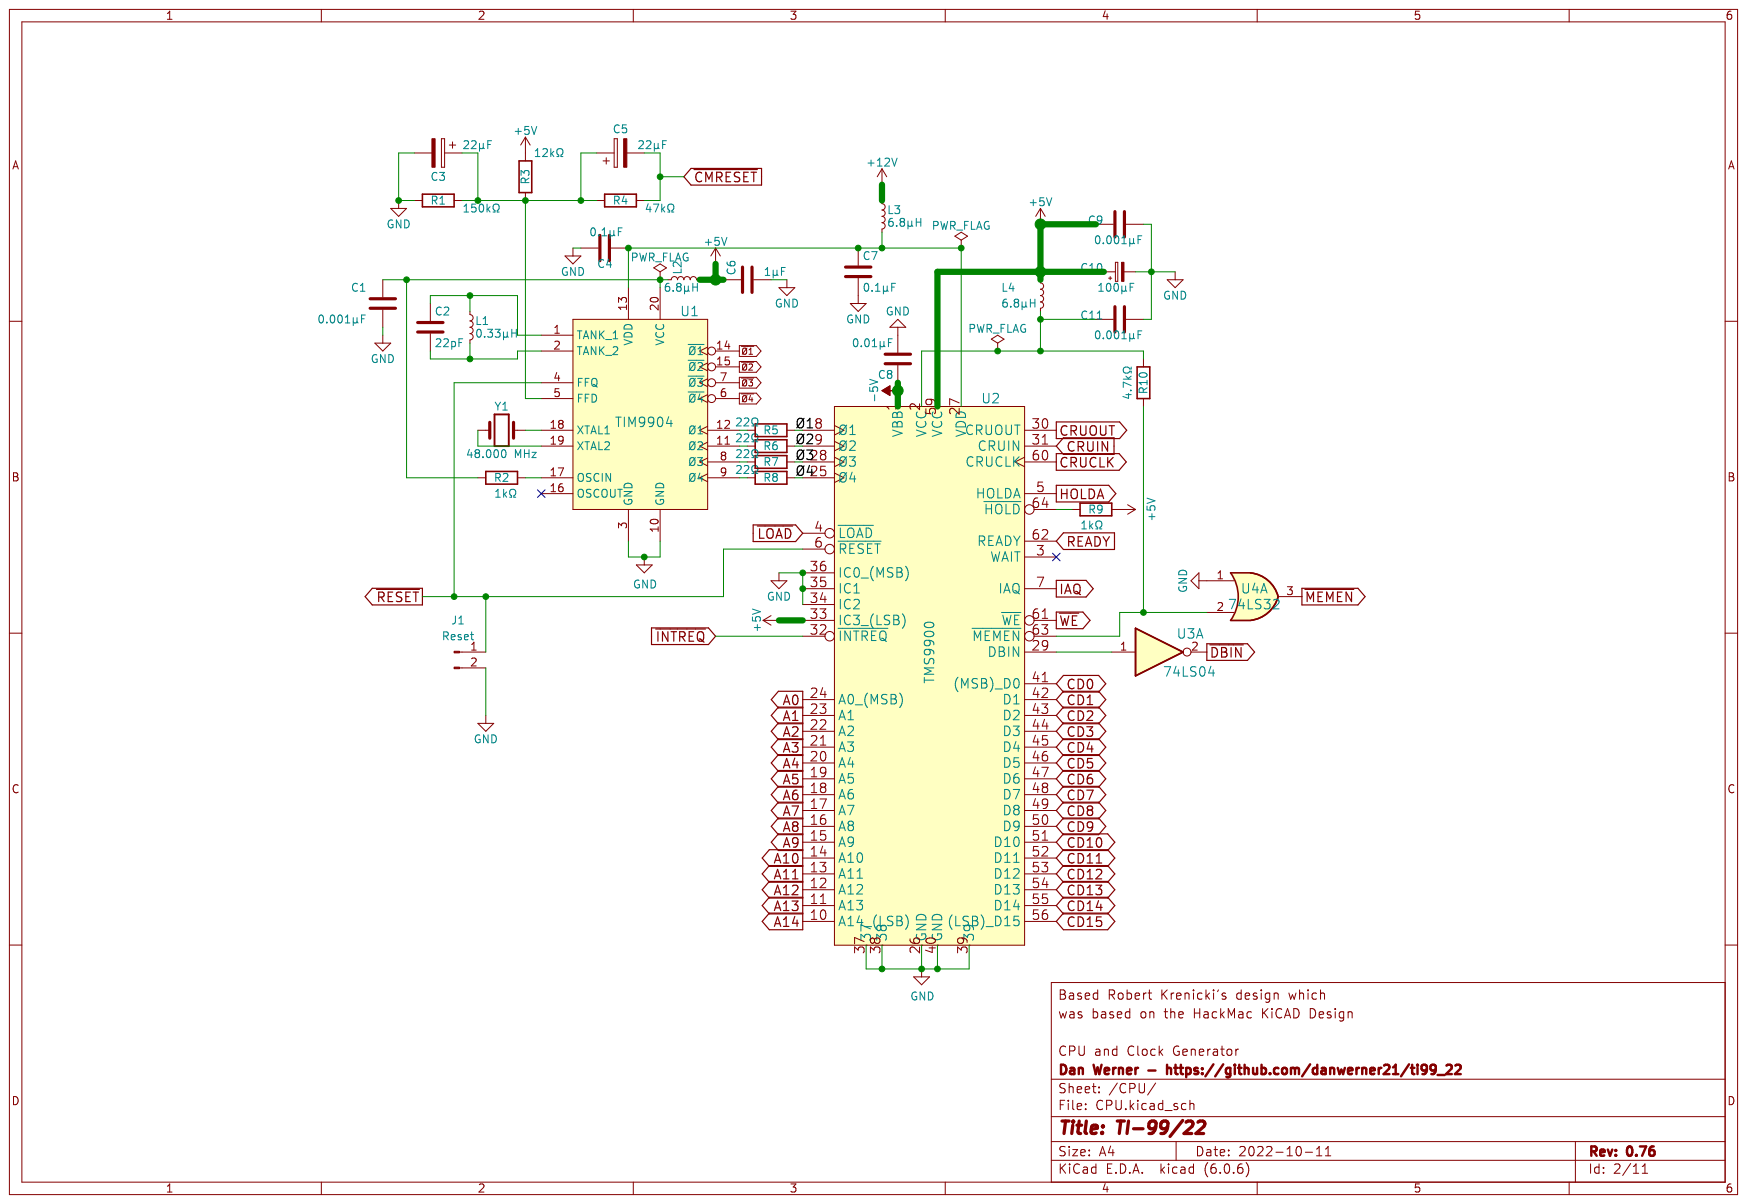
[picture p92: page 2]

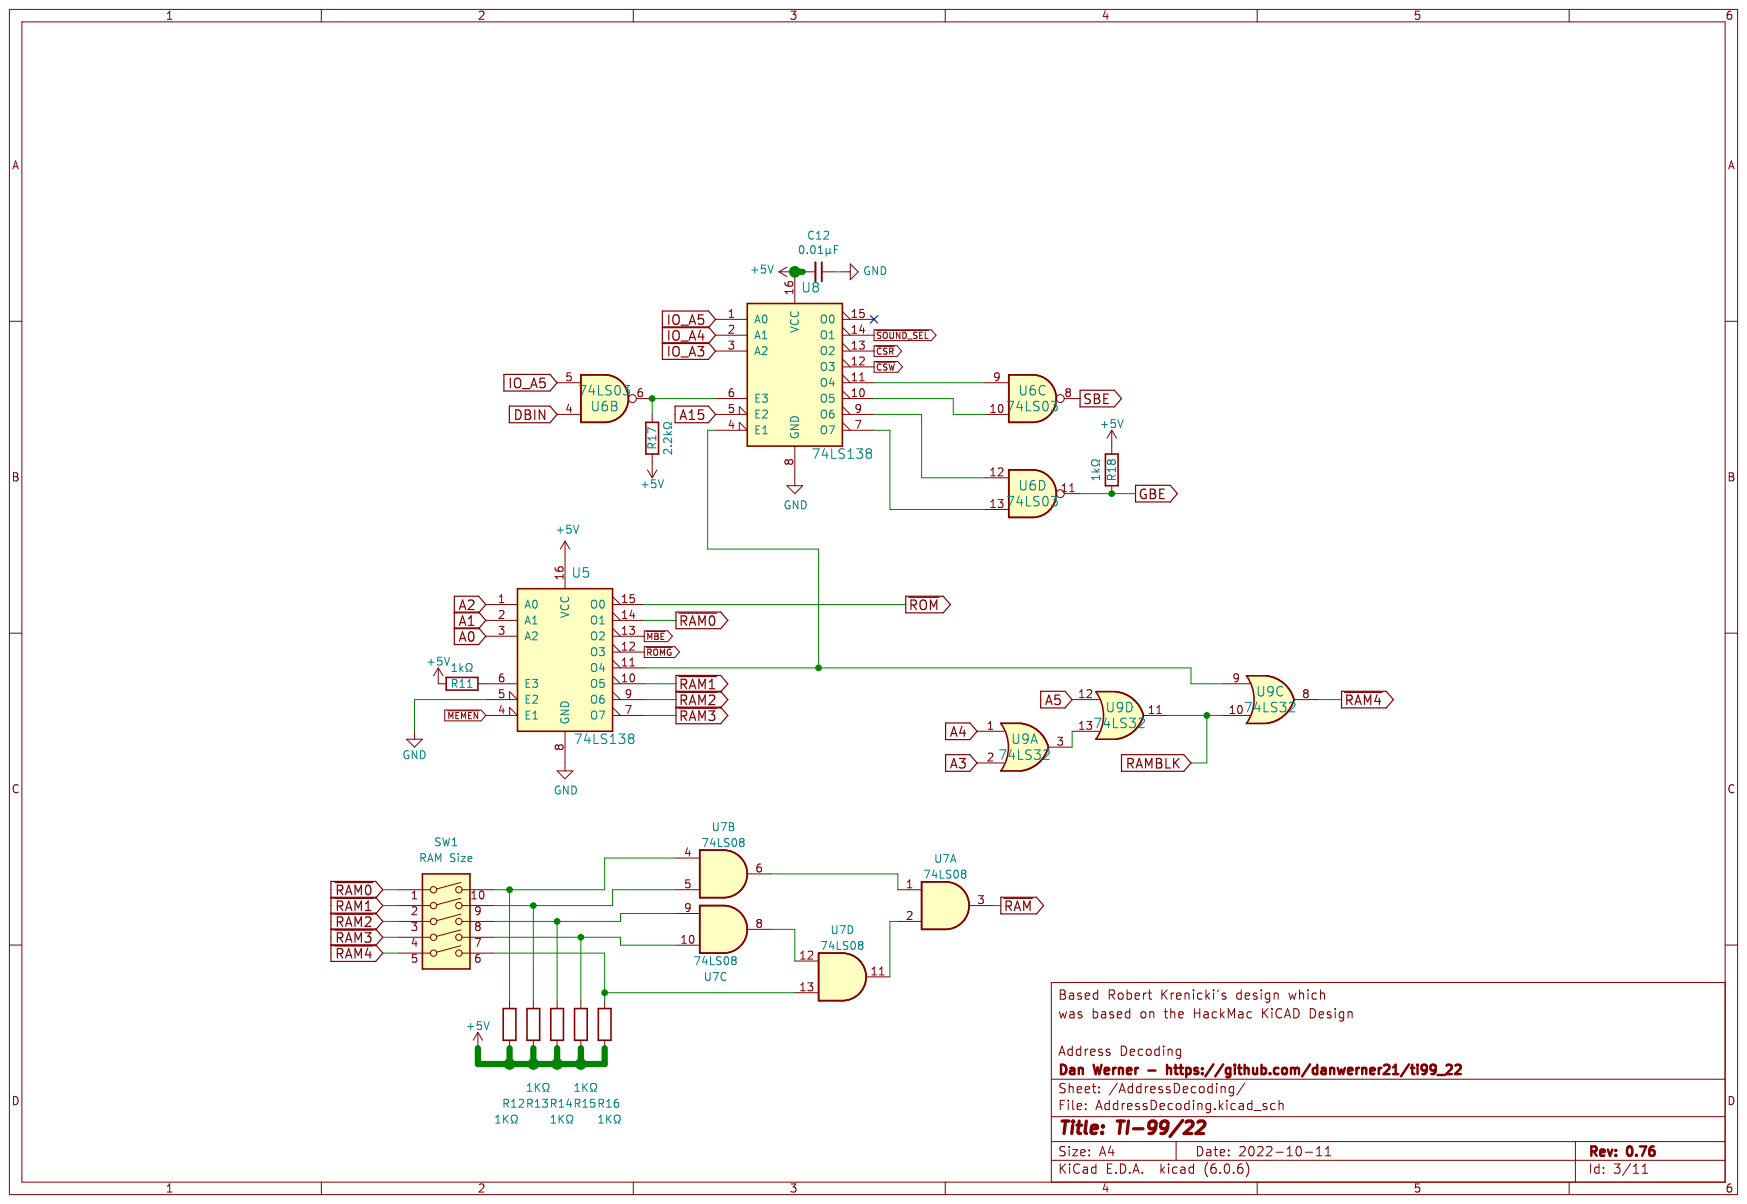
[picture p93: page 3]

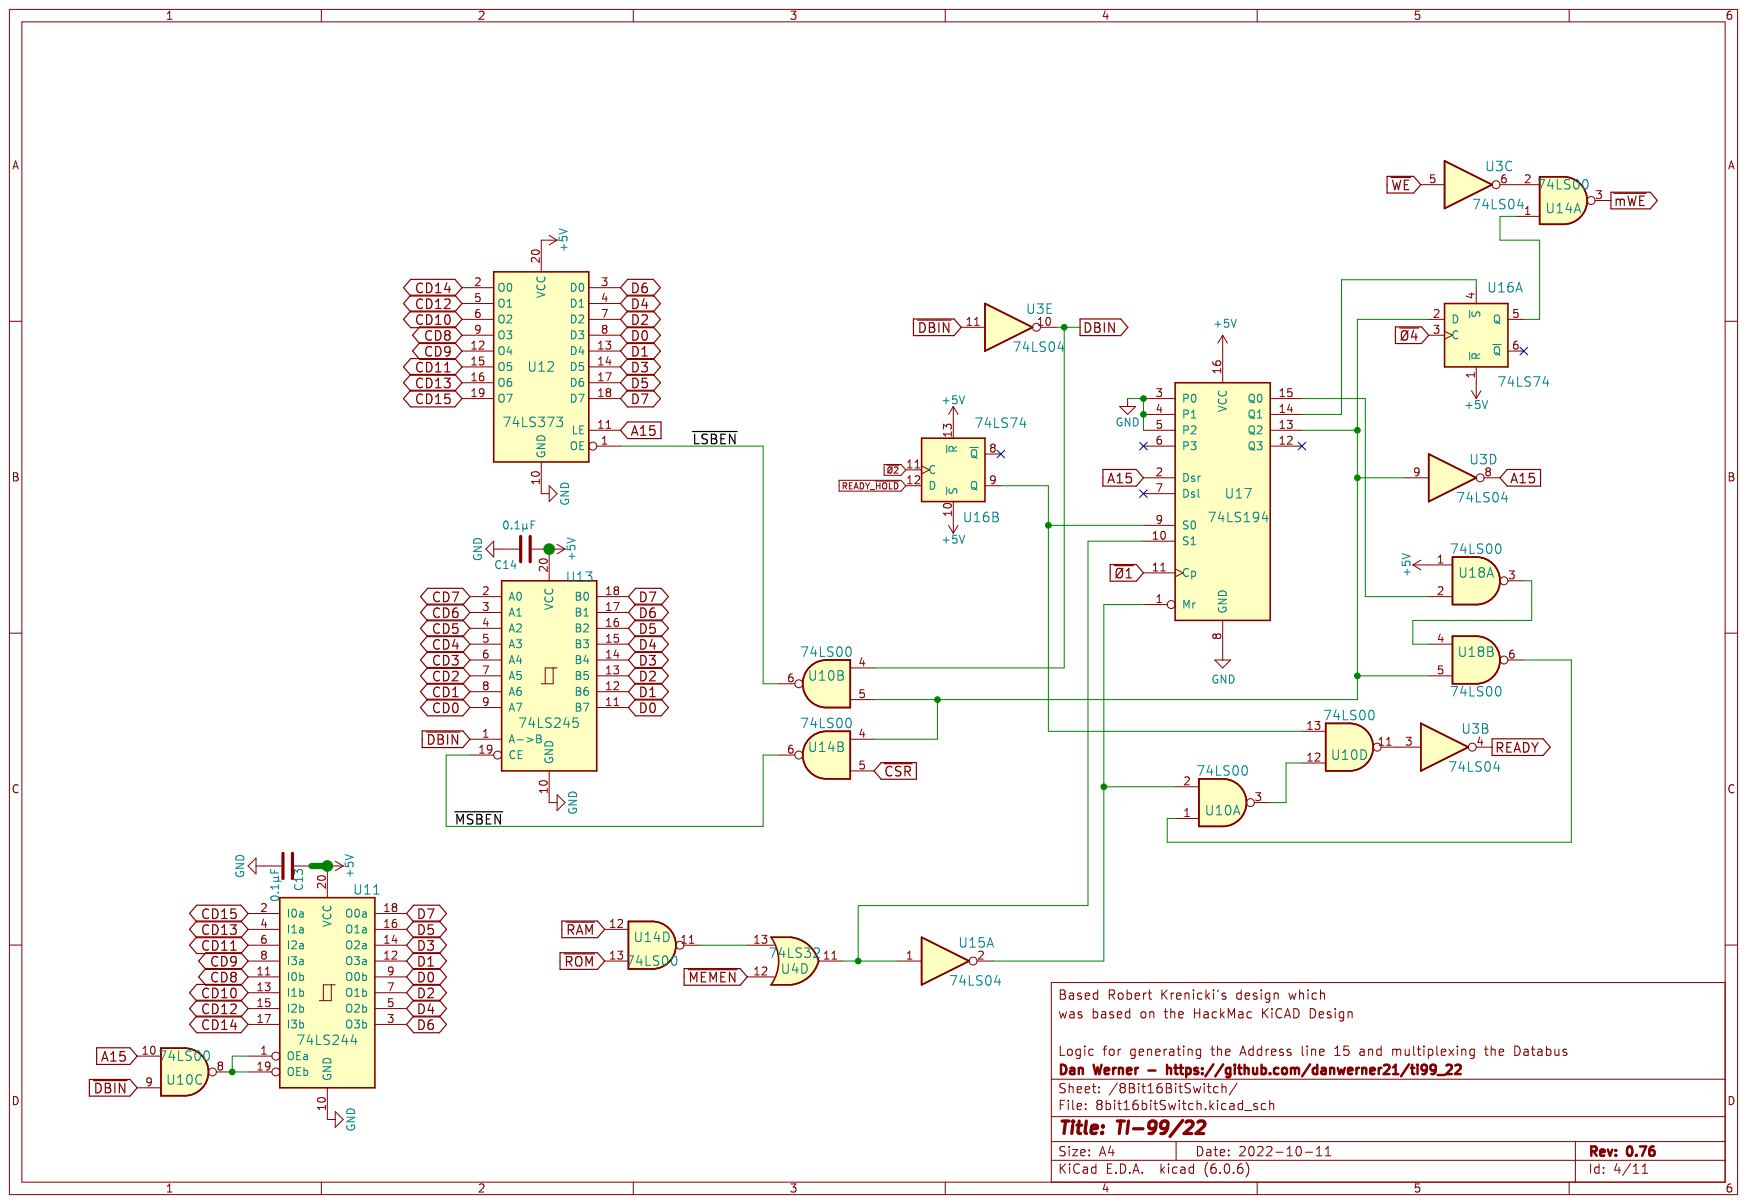
[picture p94: page 4]

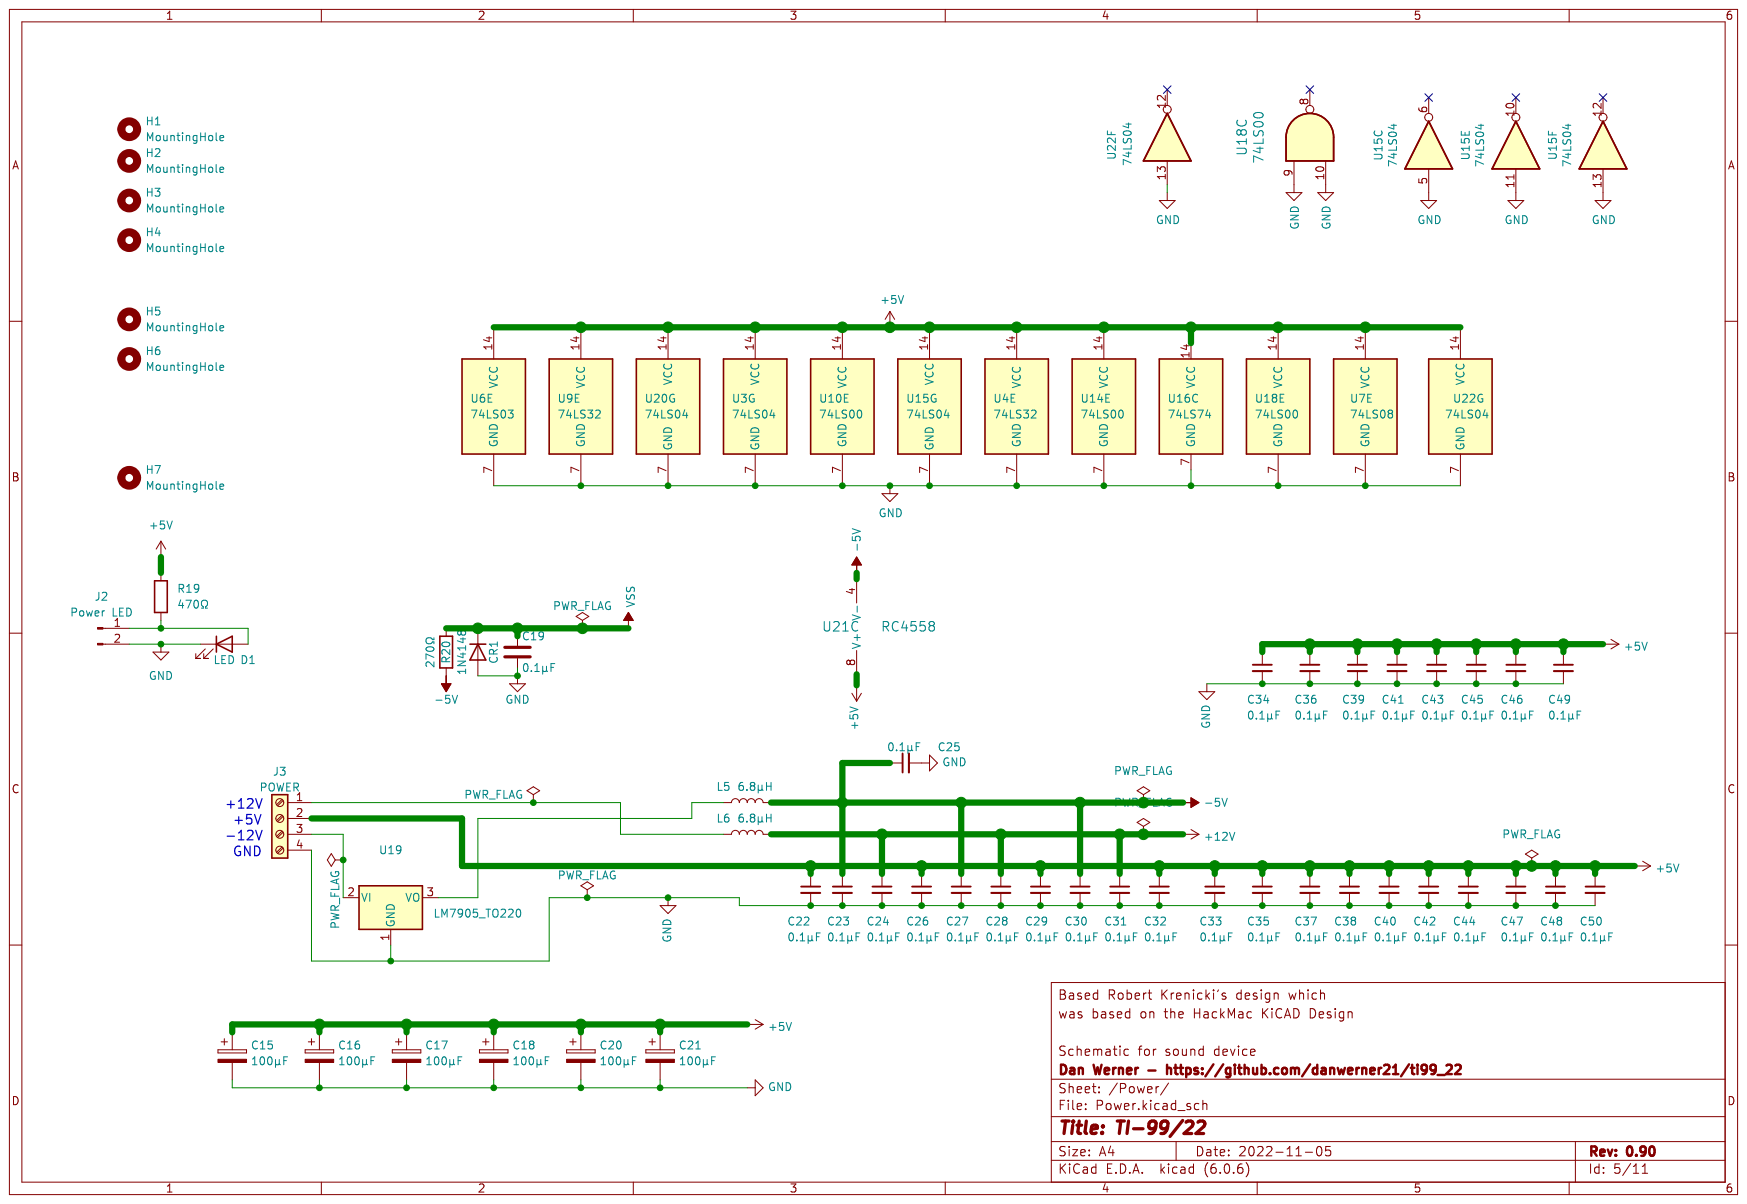
[picture p95: page 5]

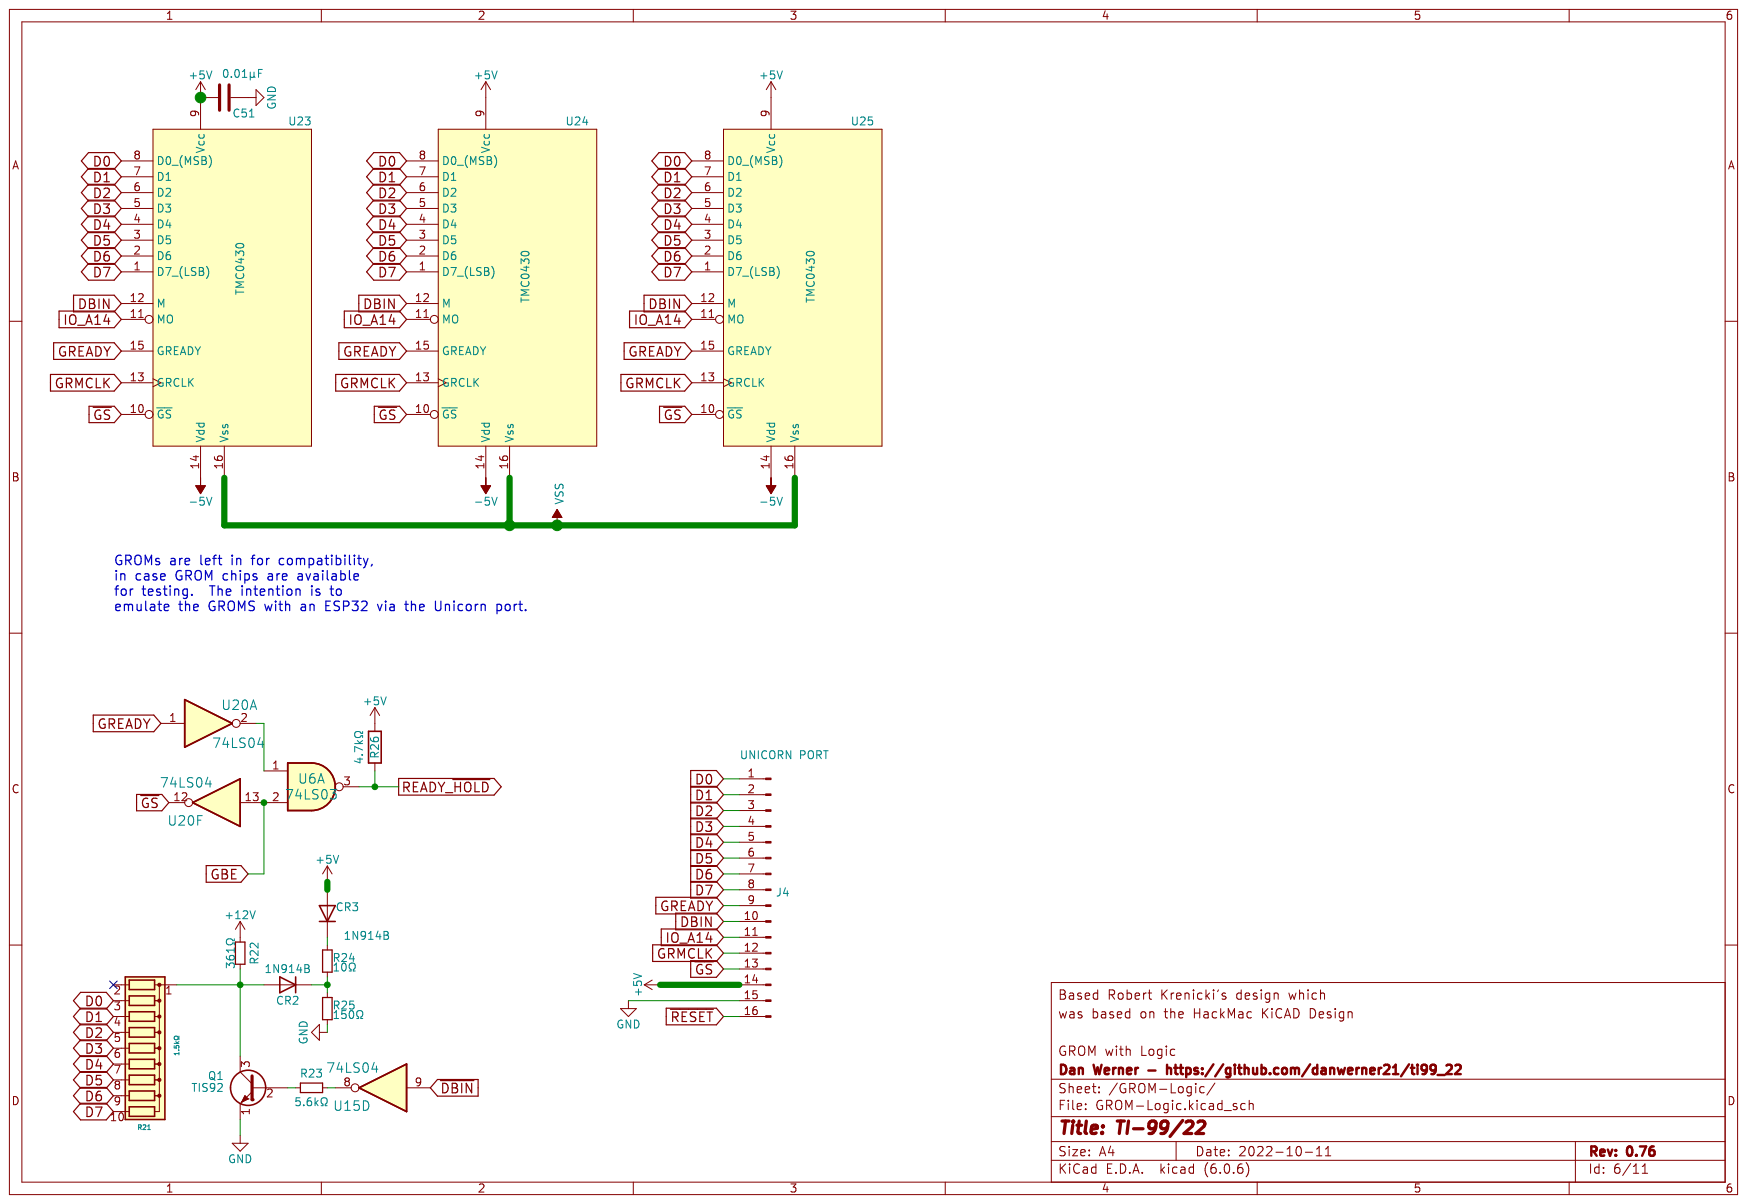
[picture p96: page 6]

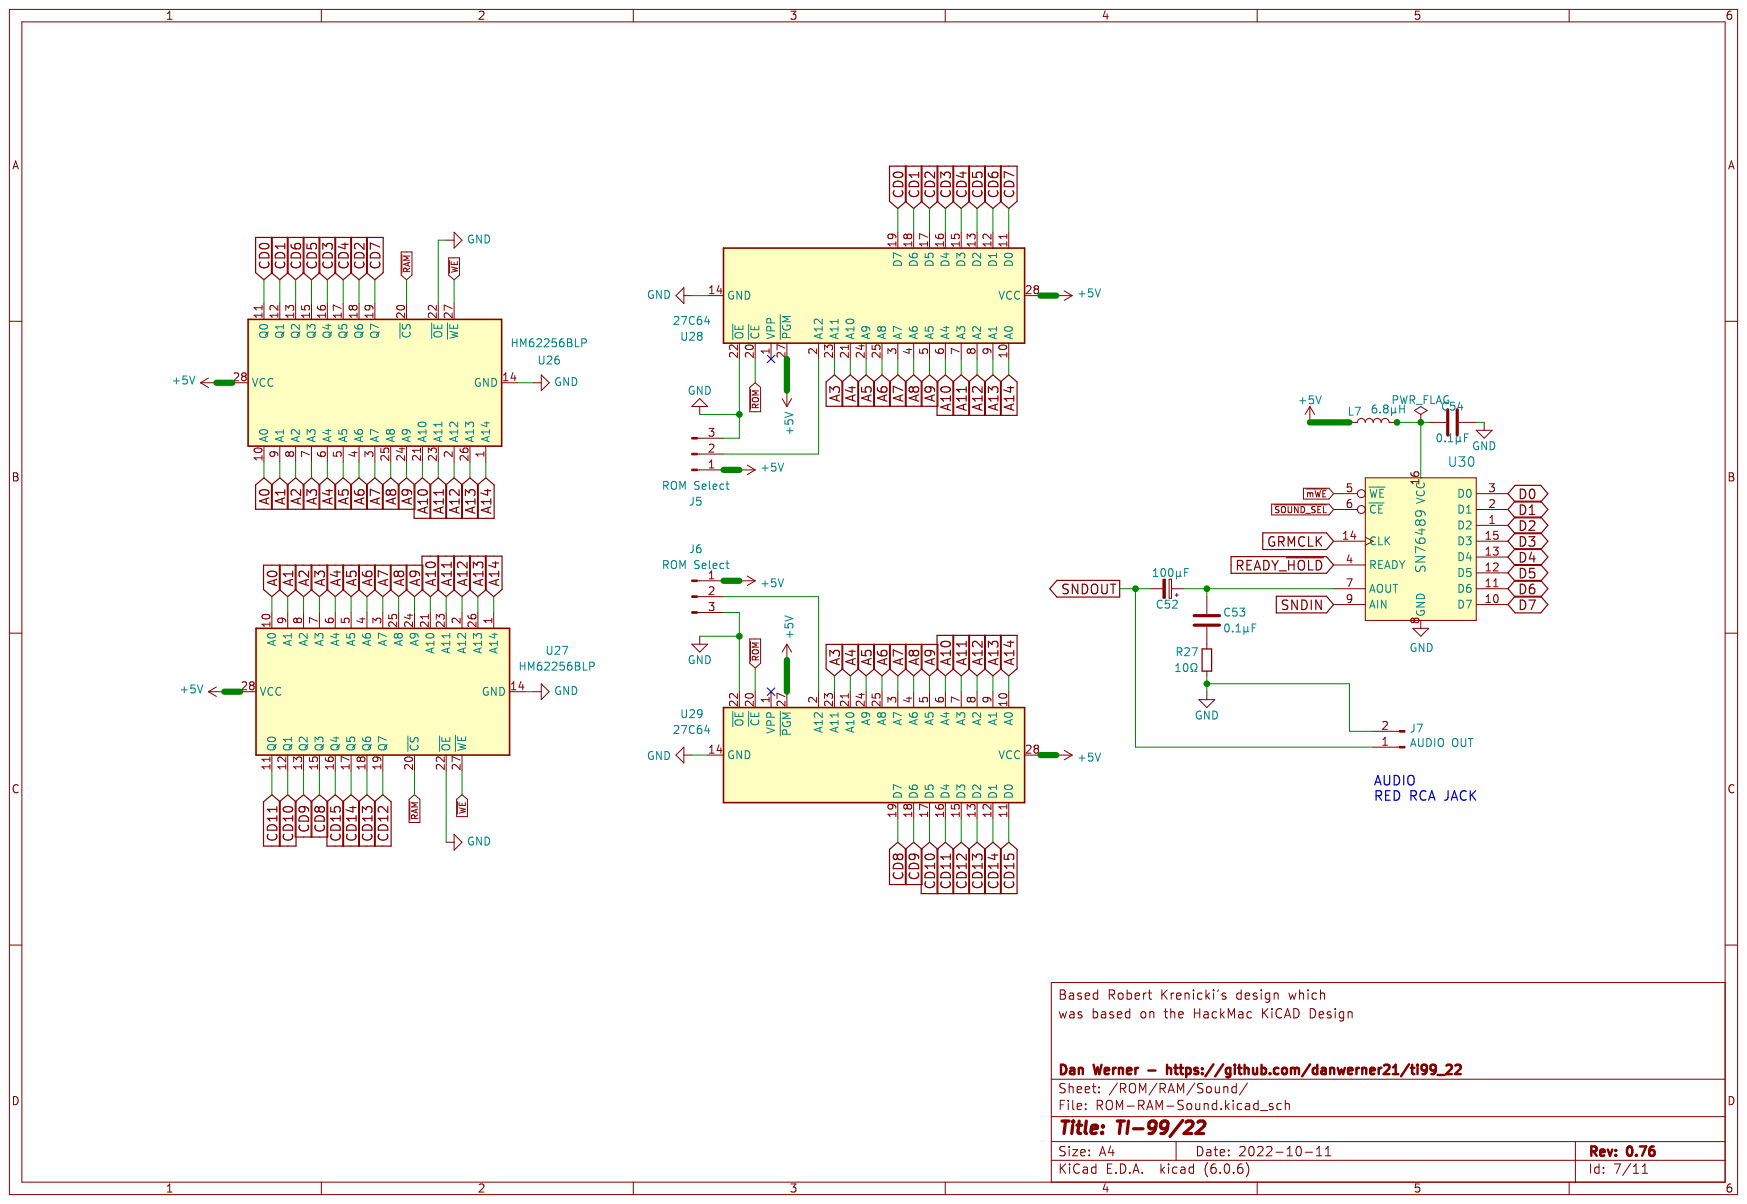
[picture p97: page 7]

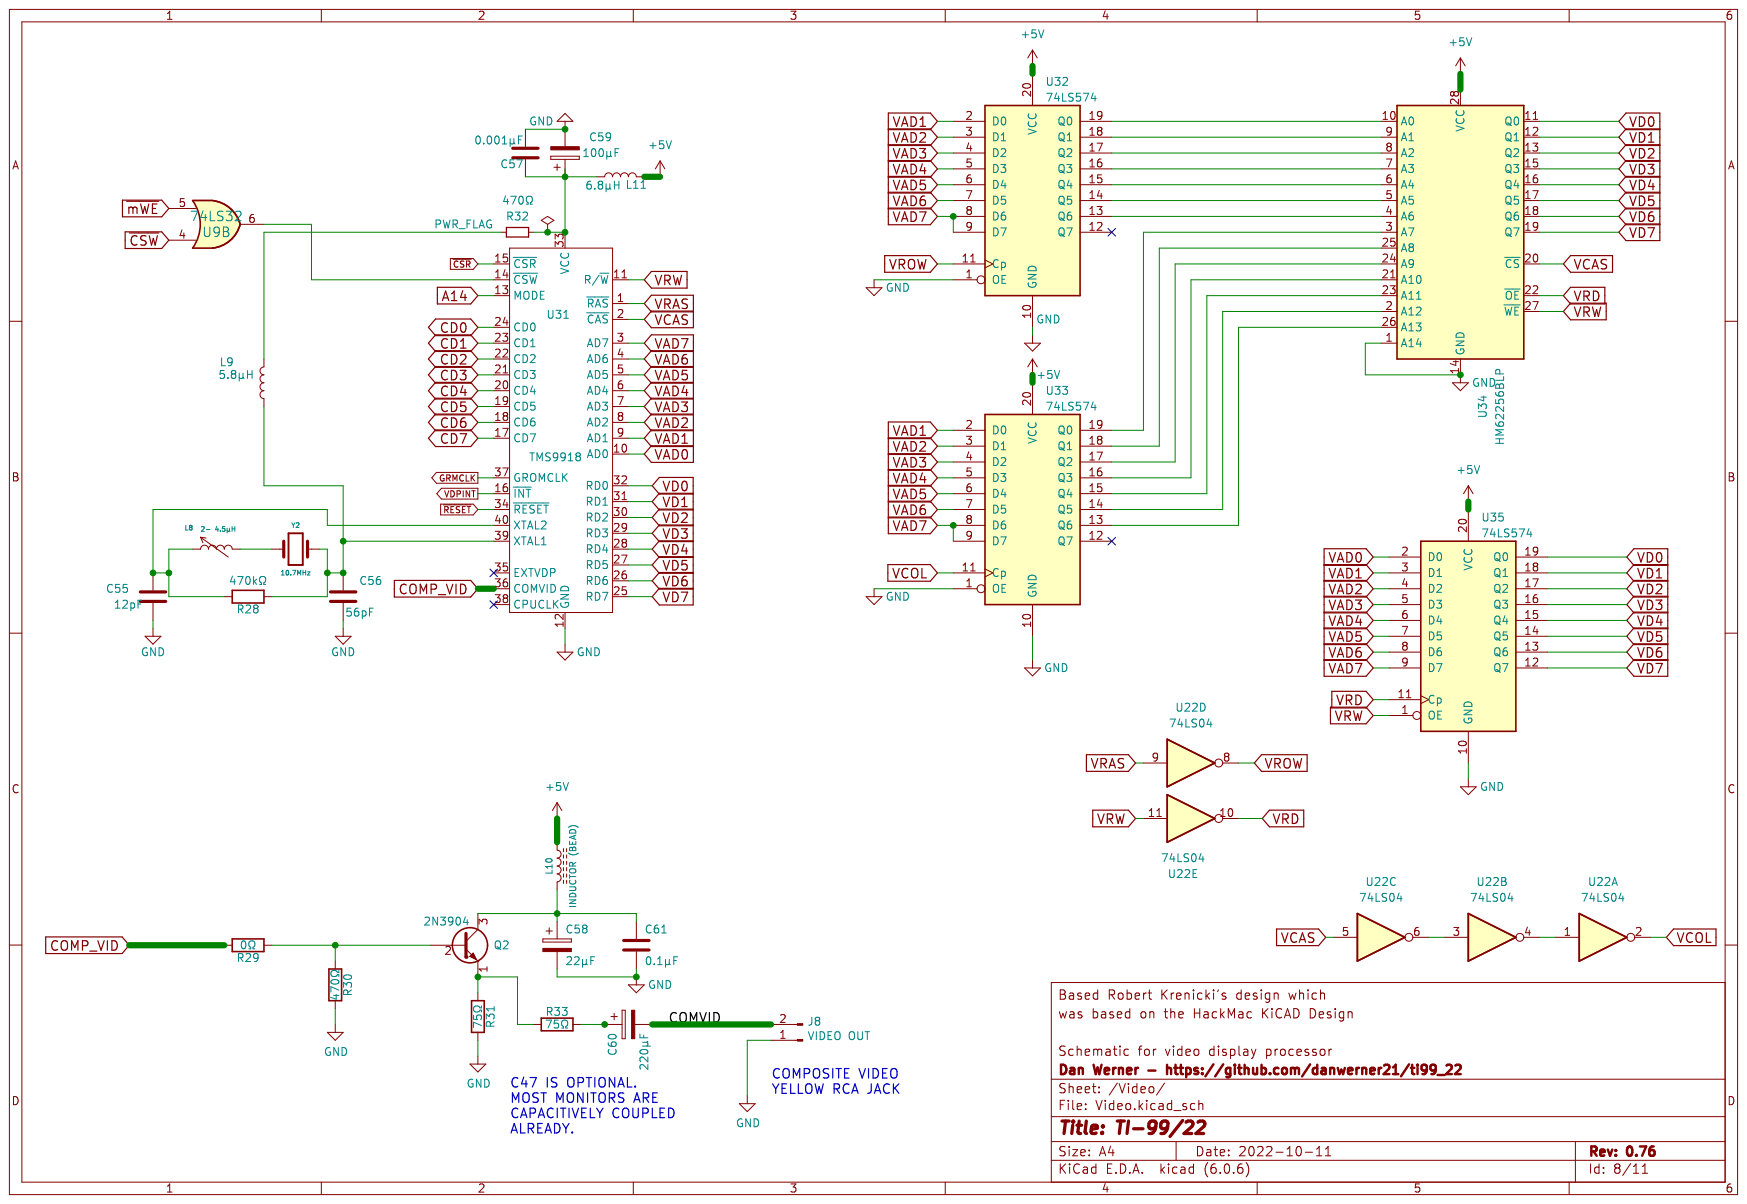
[picture p98: page 8]

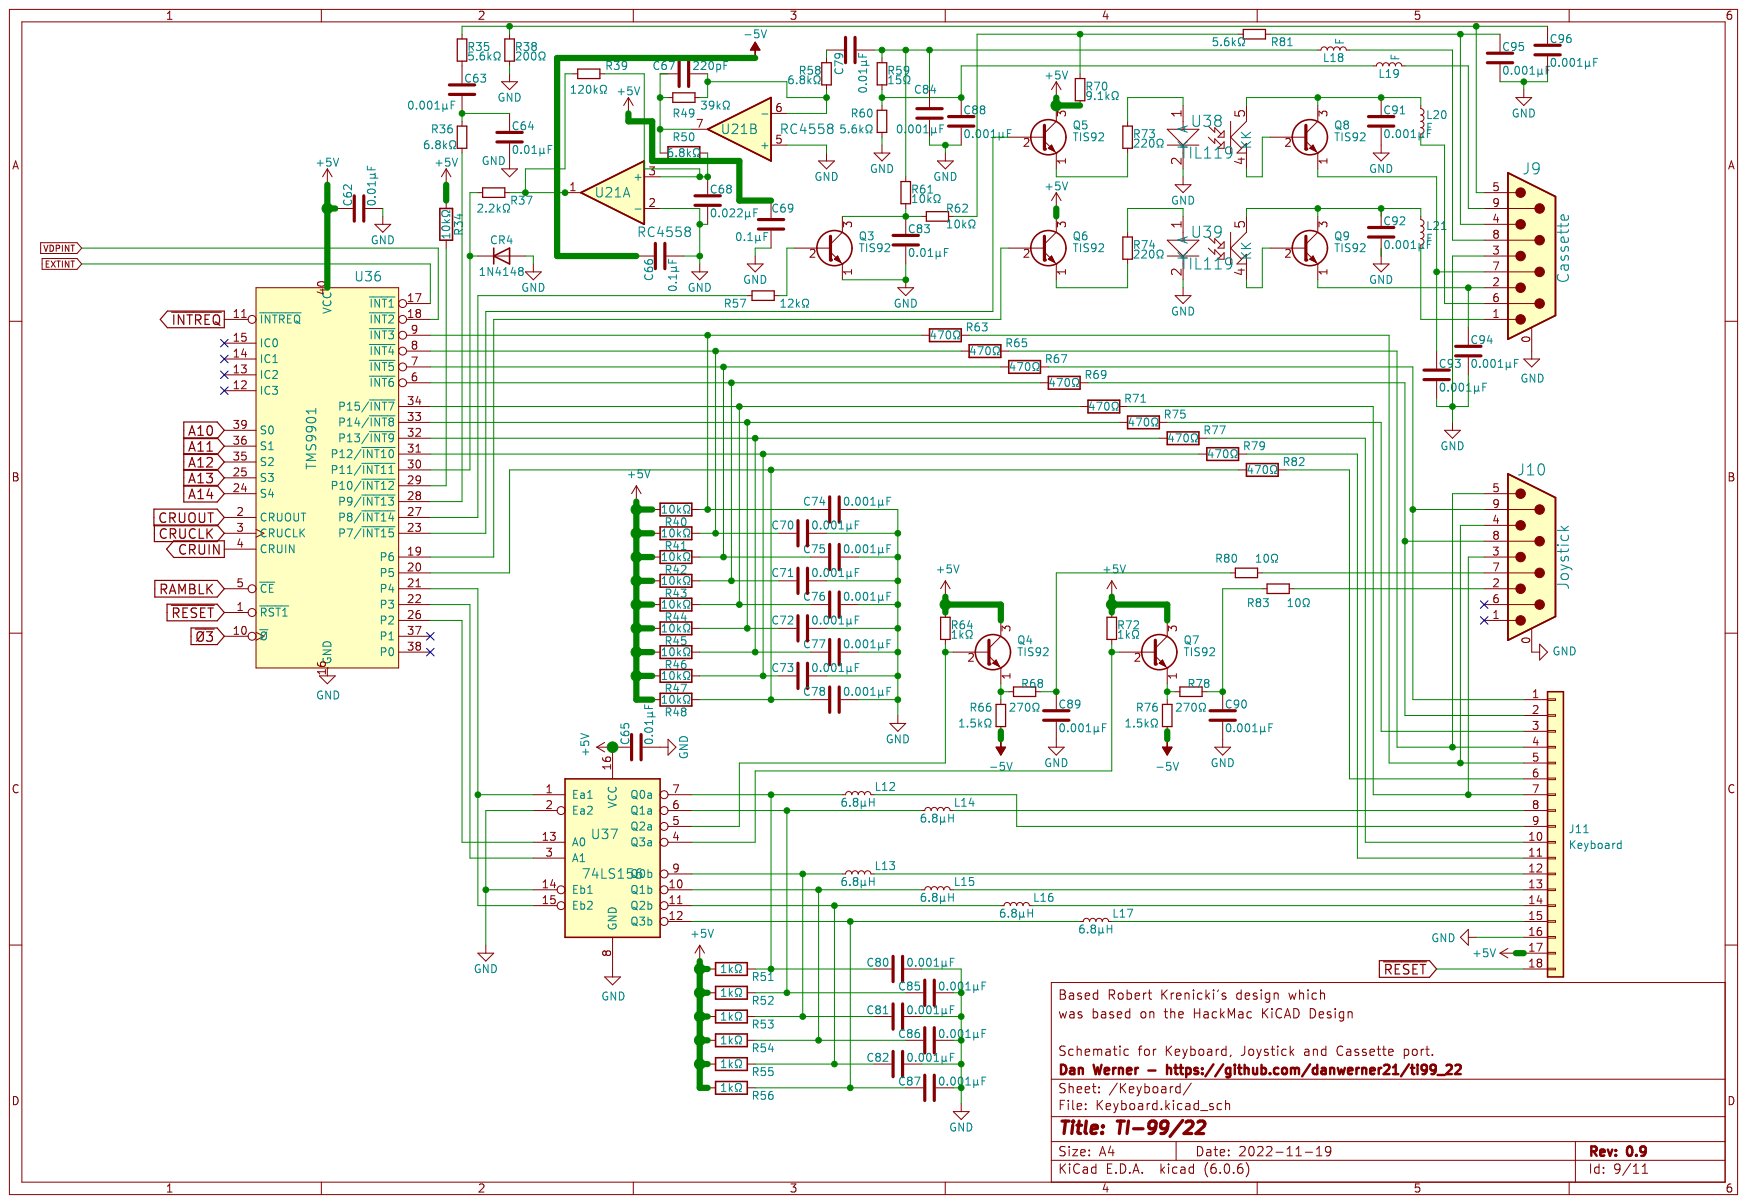
[picture p99: page 9]

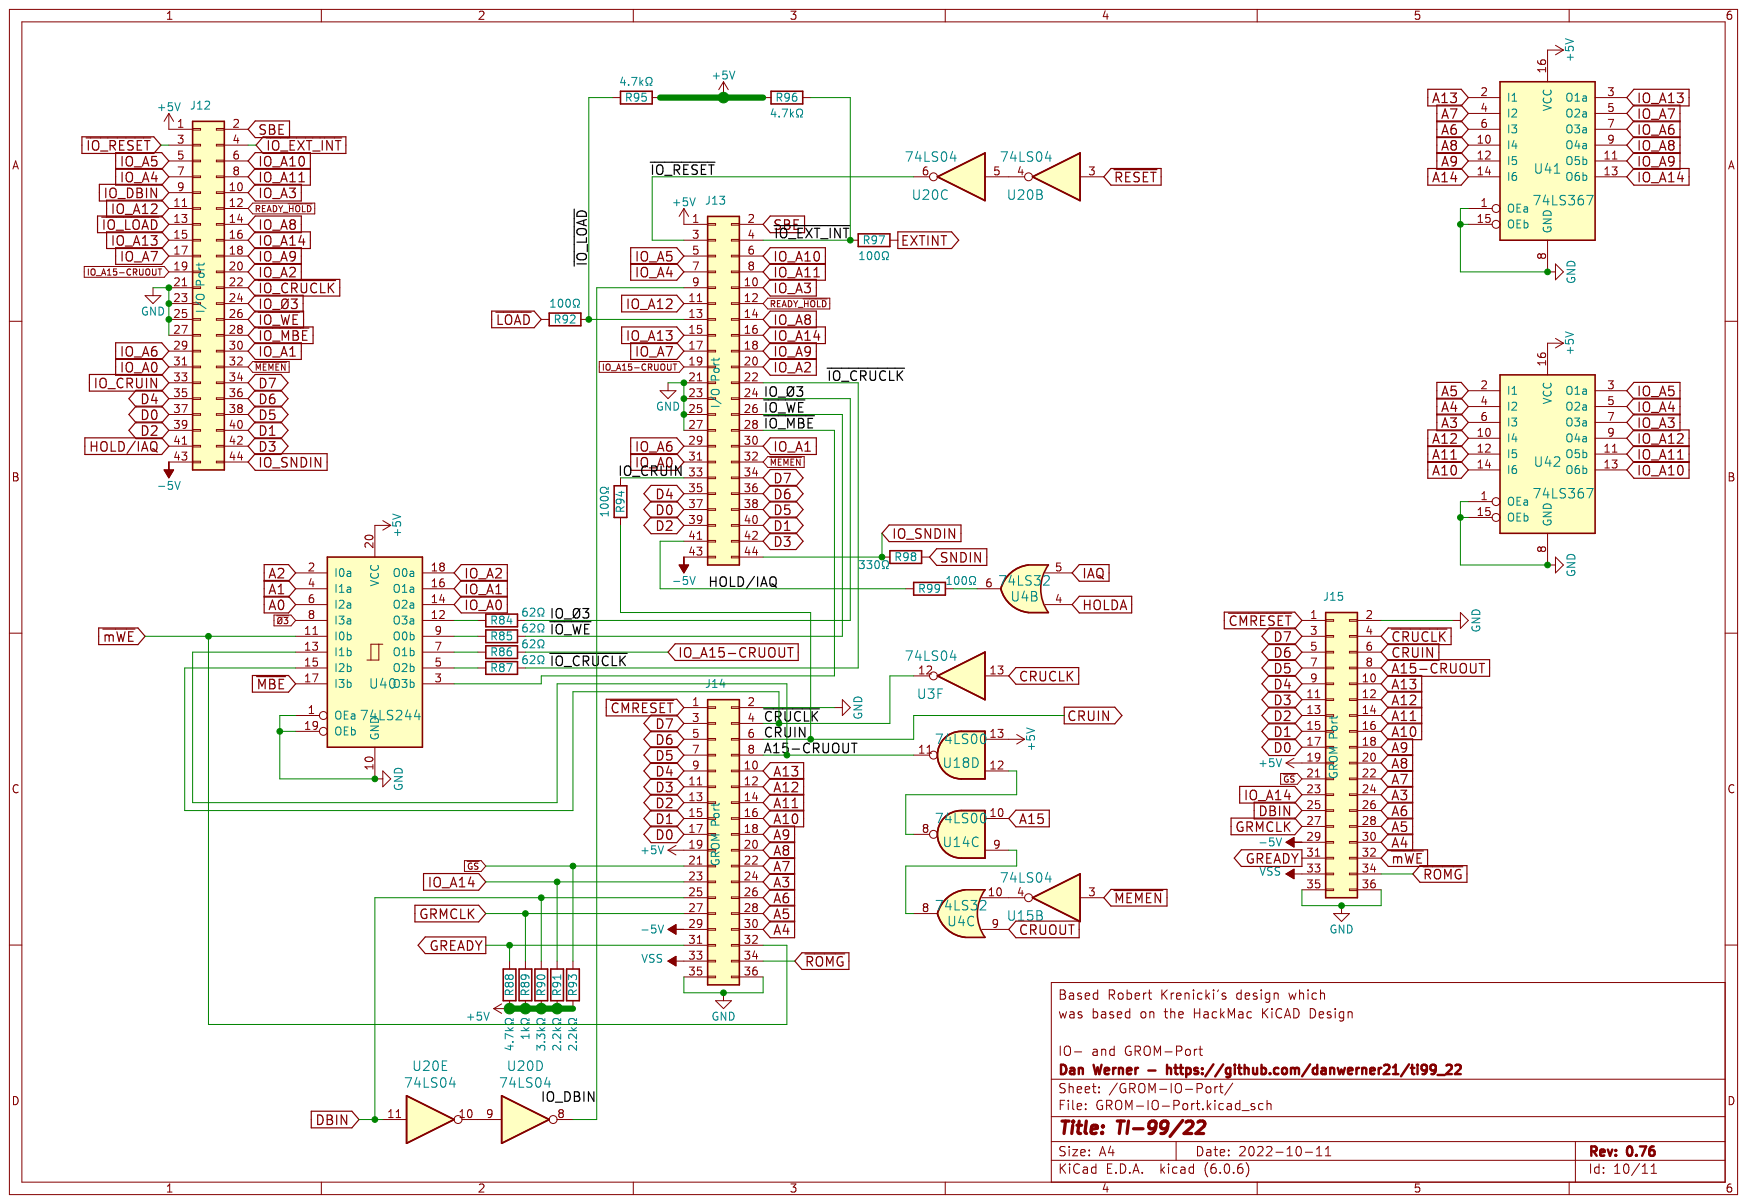
[picture p100: page 10]

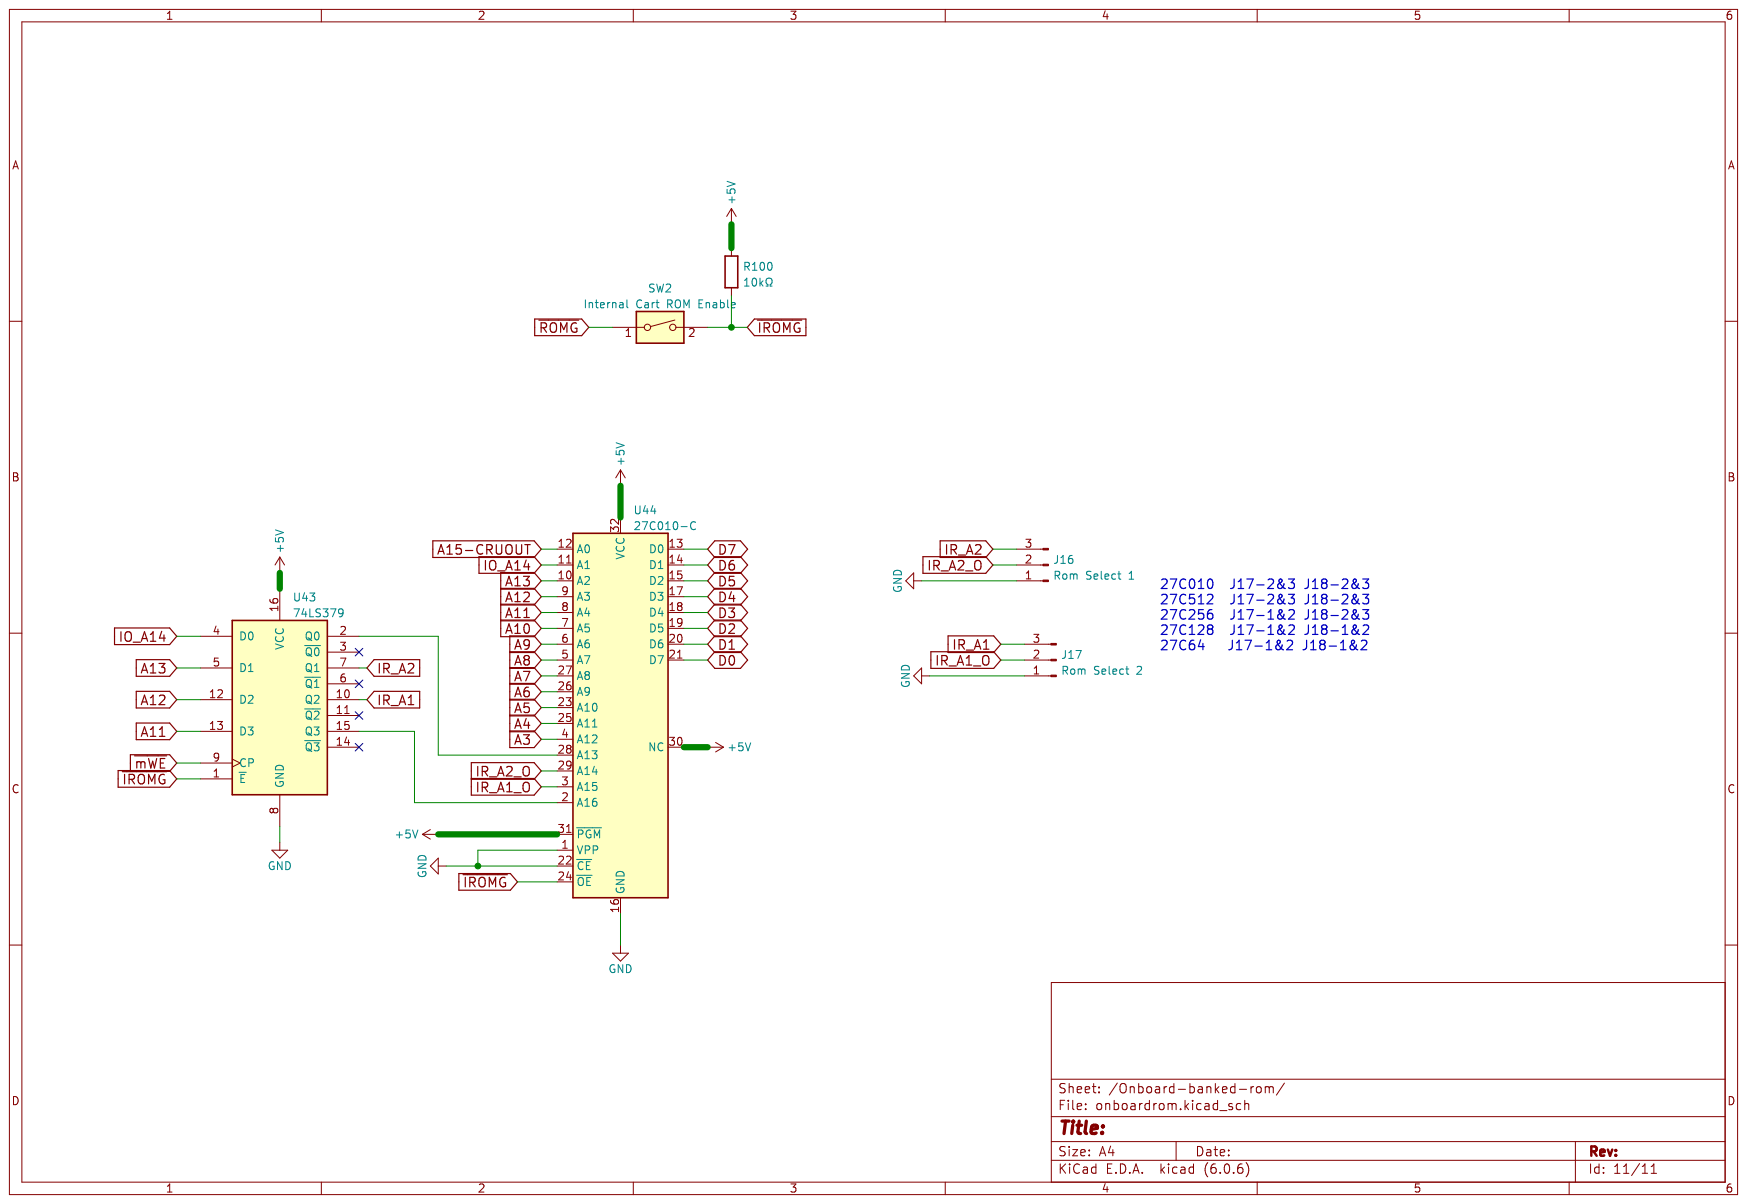
[picture p101: page 11]
