danwerner21/TI99_22/Keyboard/Keyboard_pcbV0.8.pdf

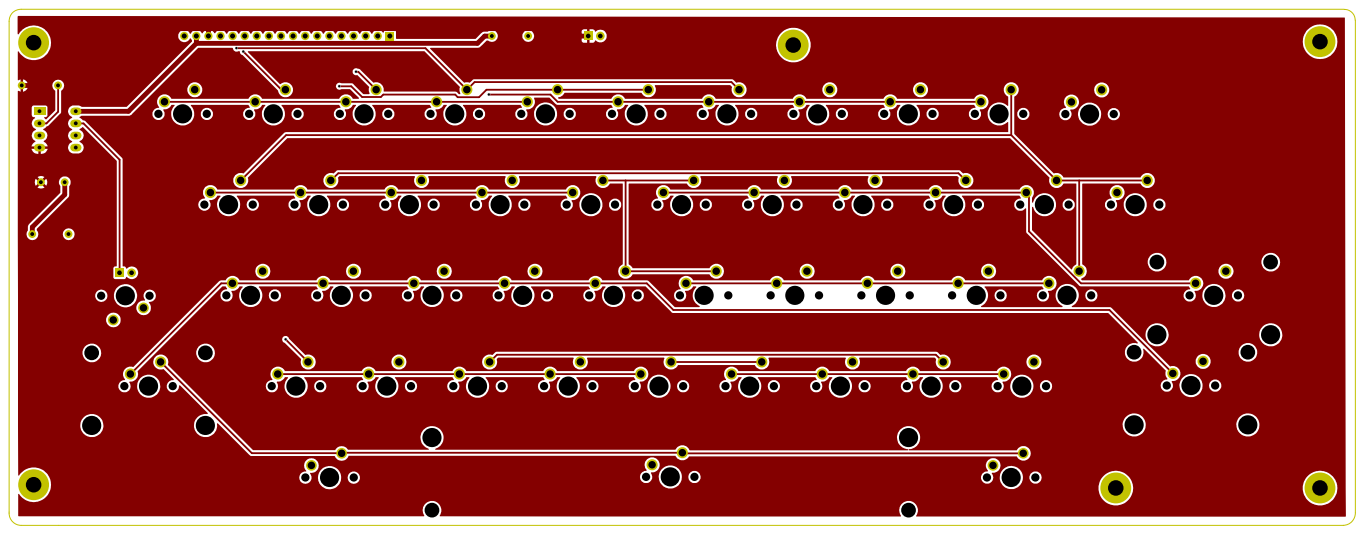
[picture p102: page 1]

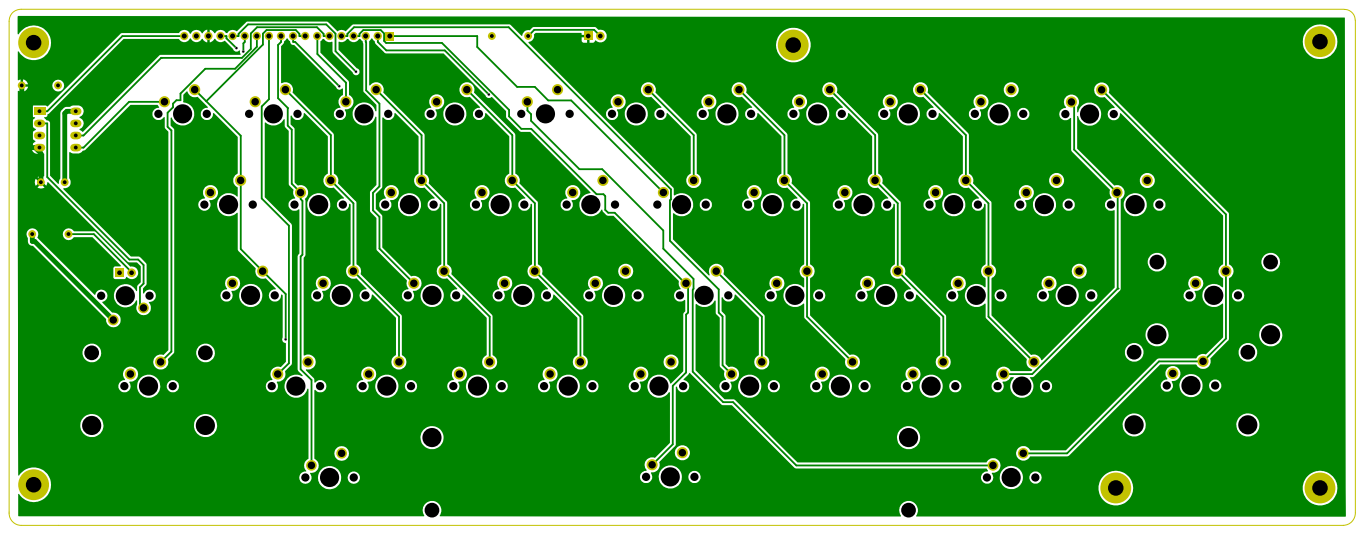
[picture p103: page 2]

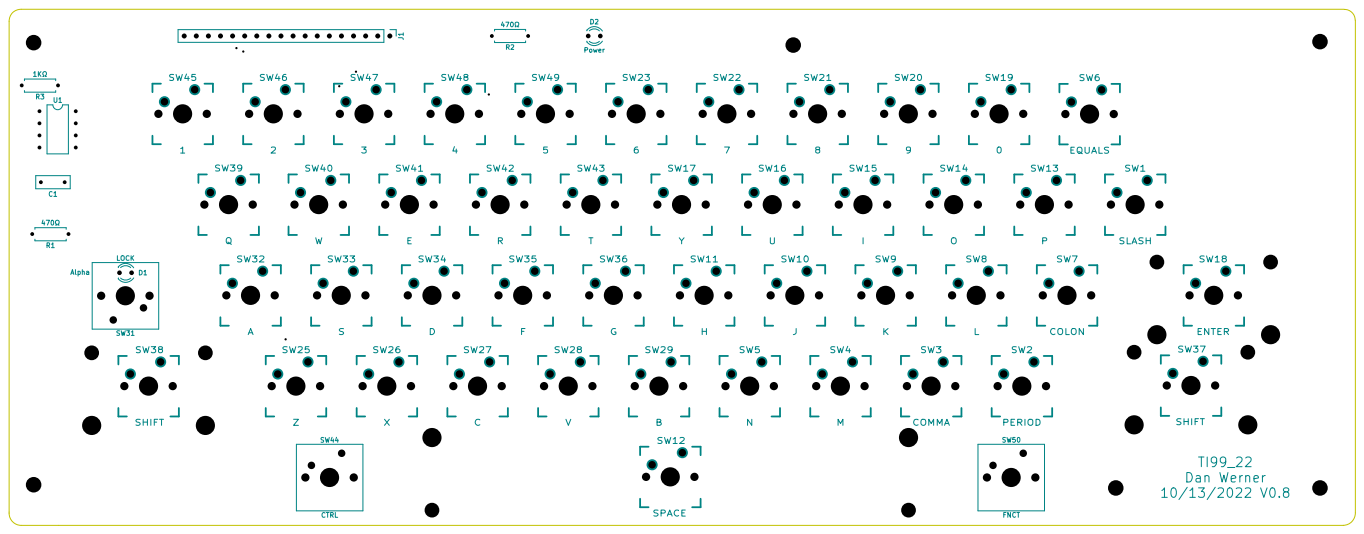
[picture p104: page 3]

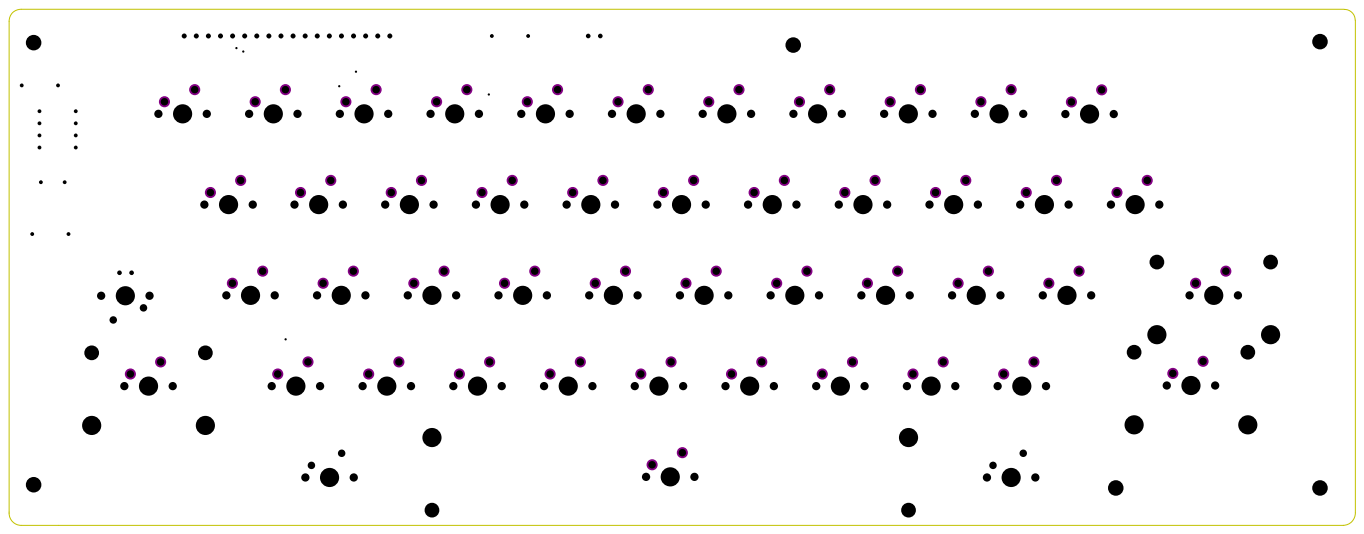
[picture p105: page 4]

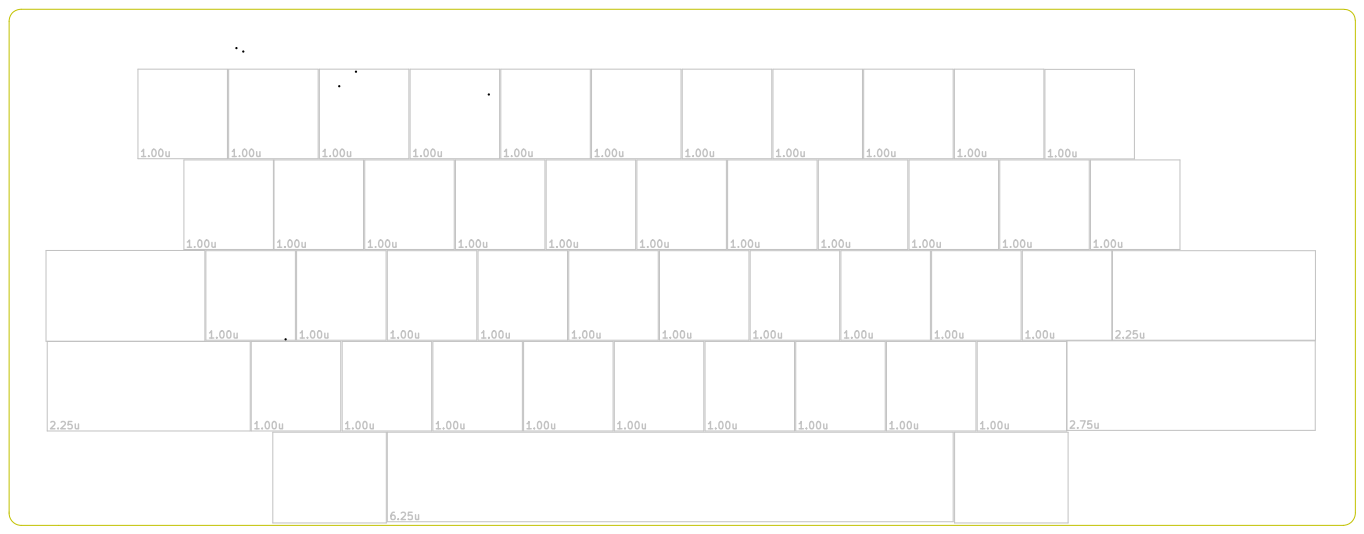
[picture p106: page 5]

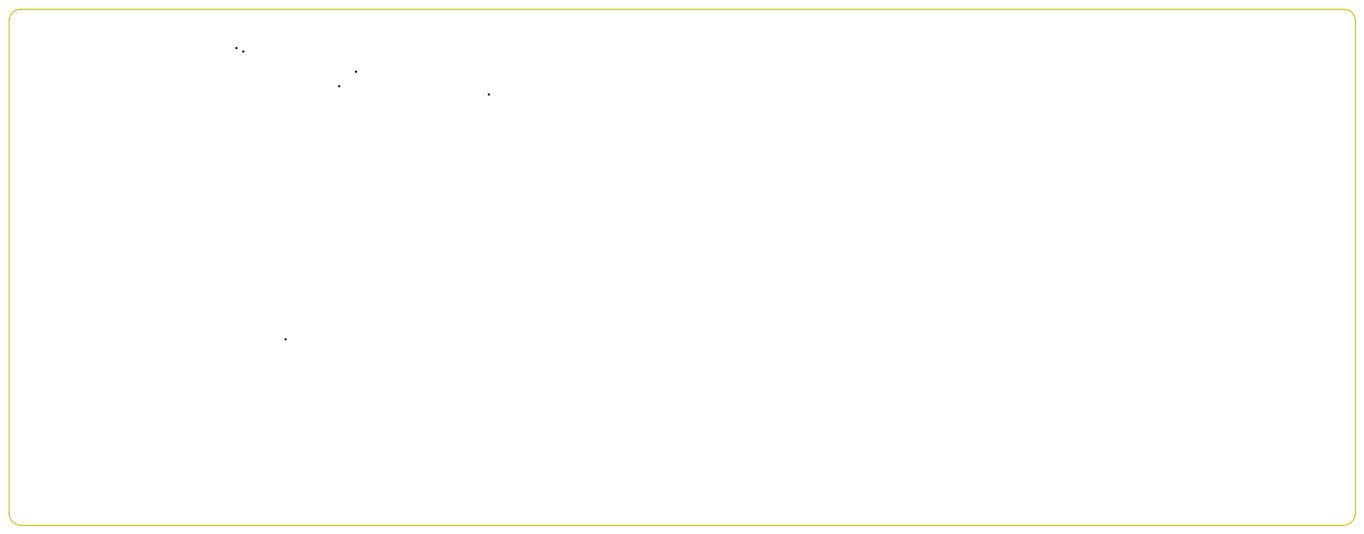
[picture p107: page 6]
