danwerner21/TI99_22/mainboard/mainboard_pcb_v0.80.pdf

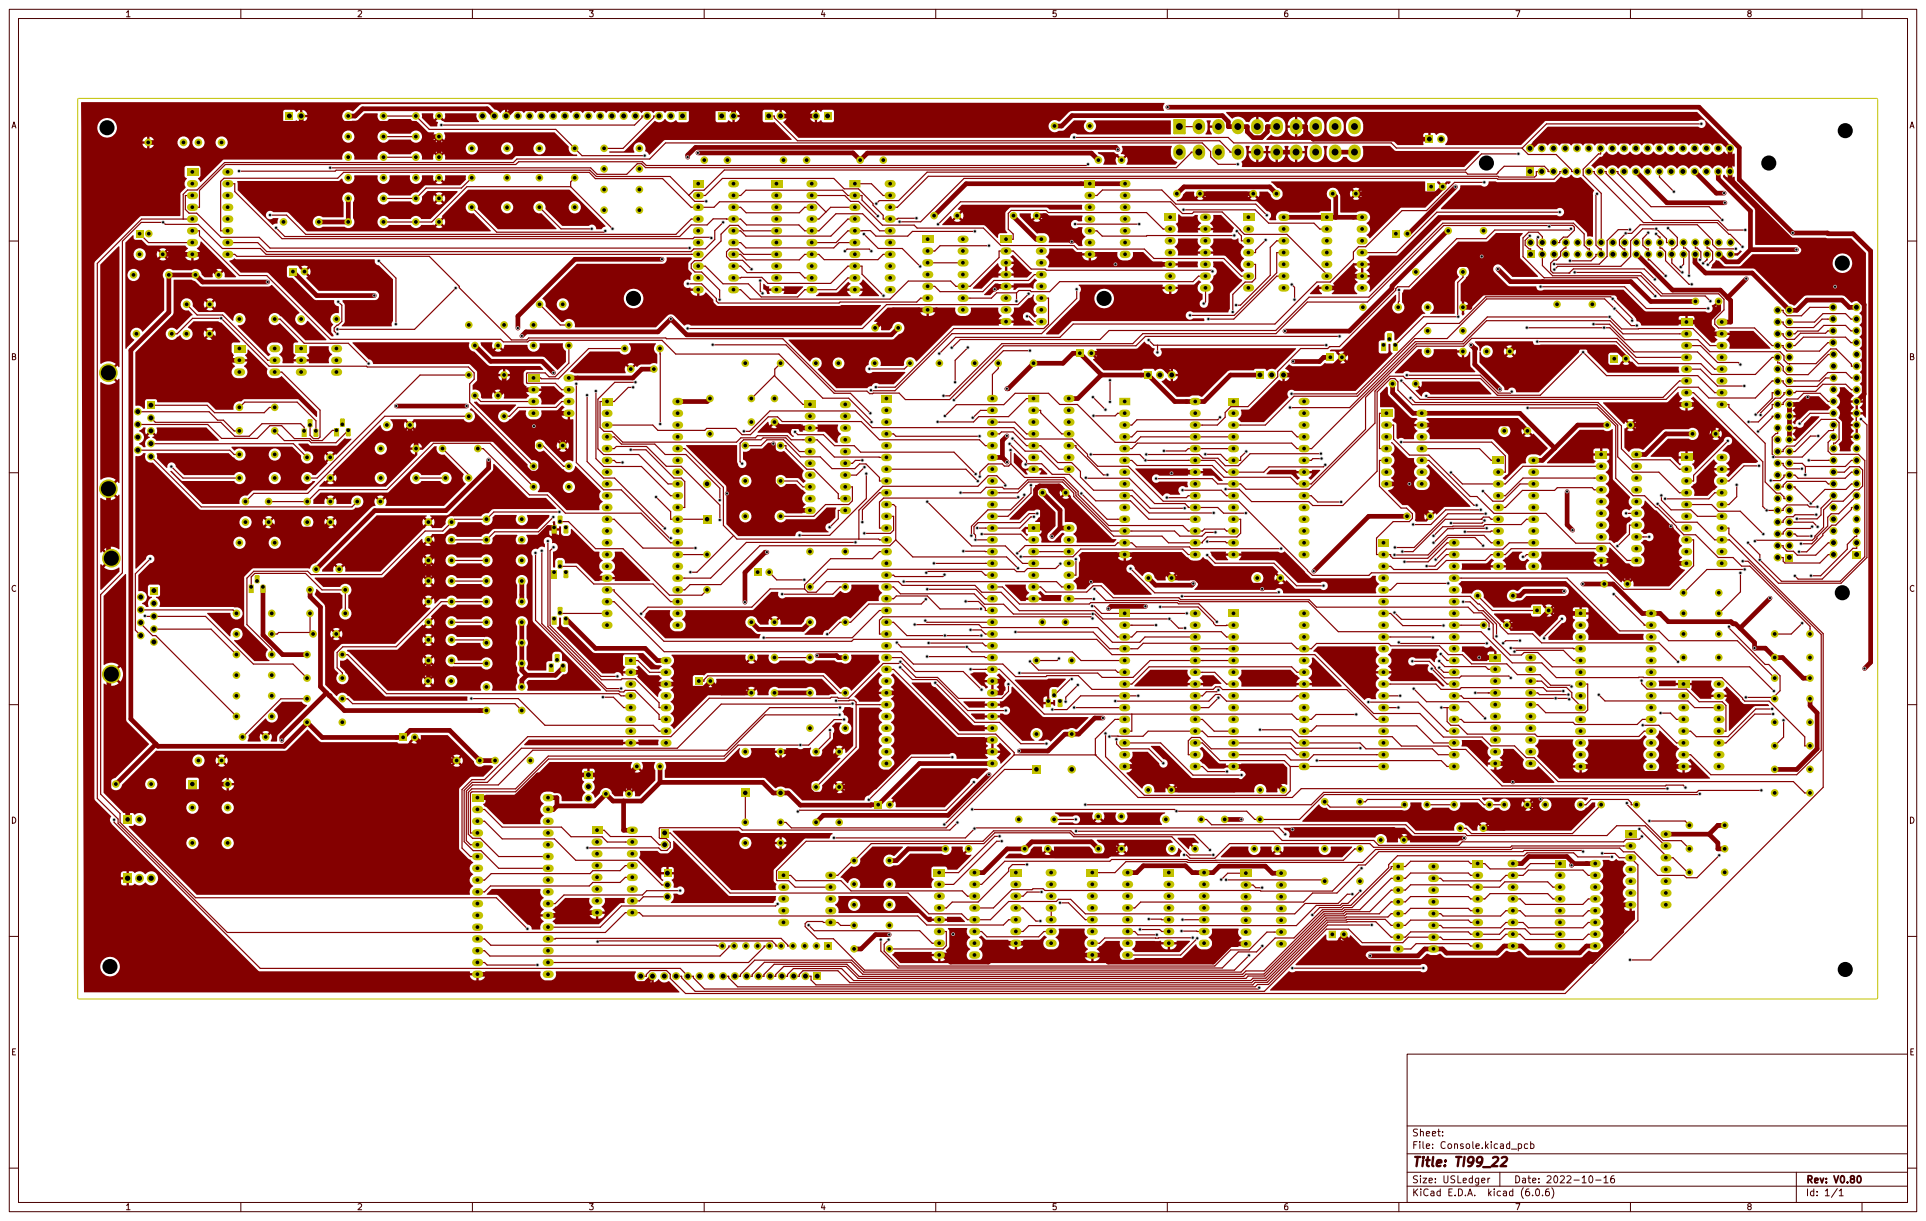
[picture p108: page 1]

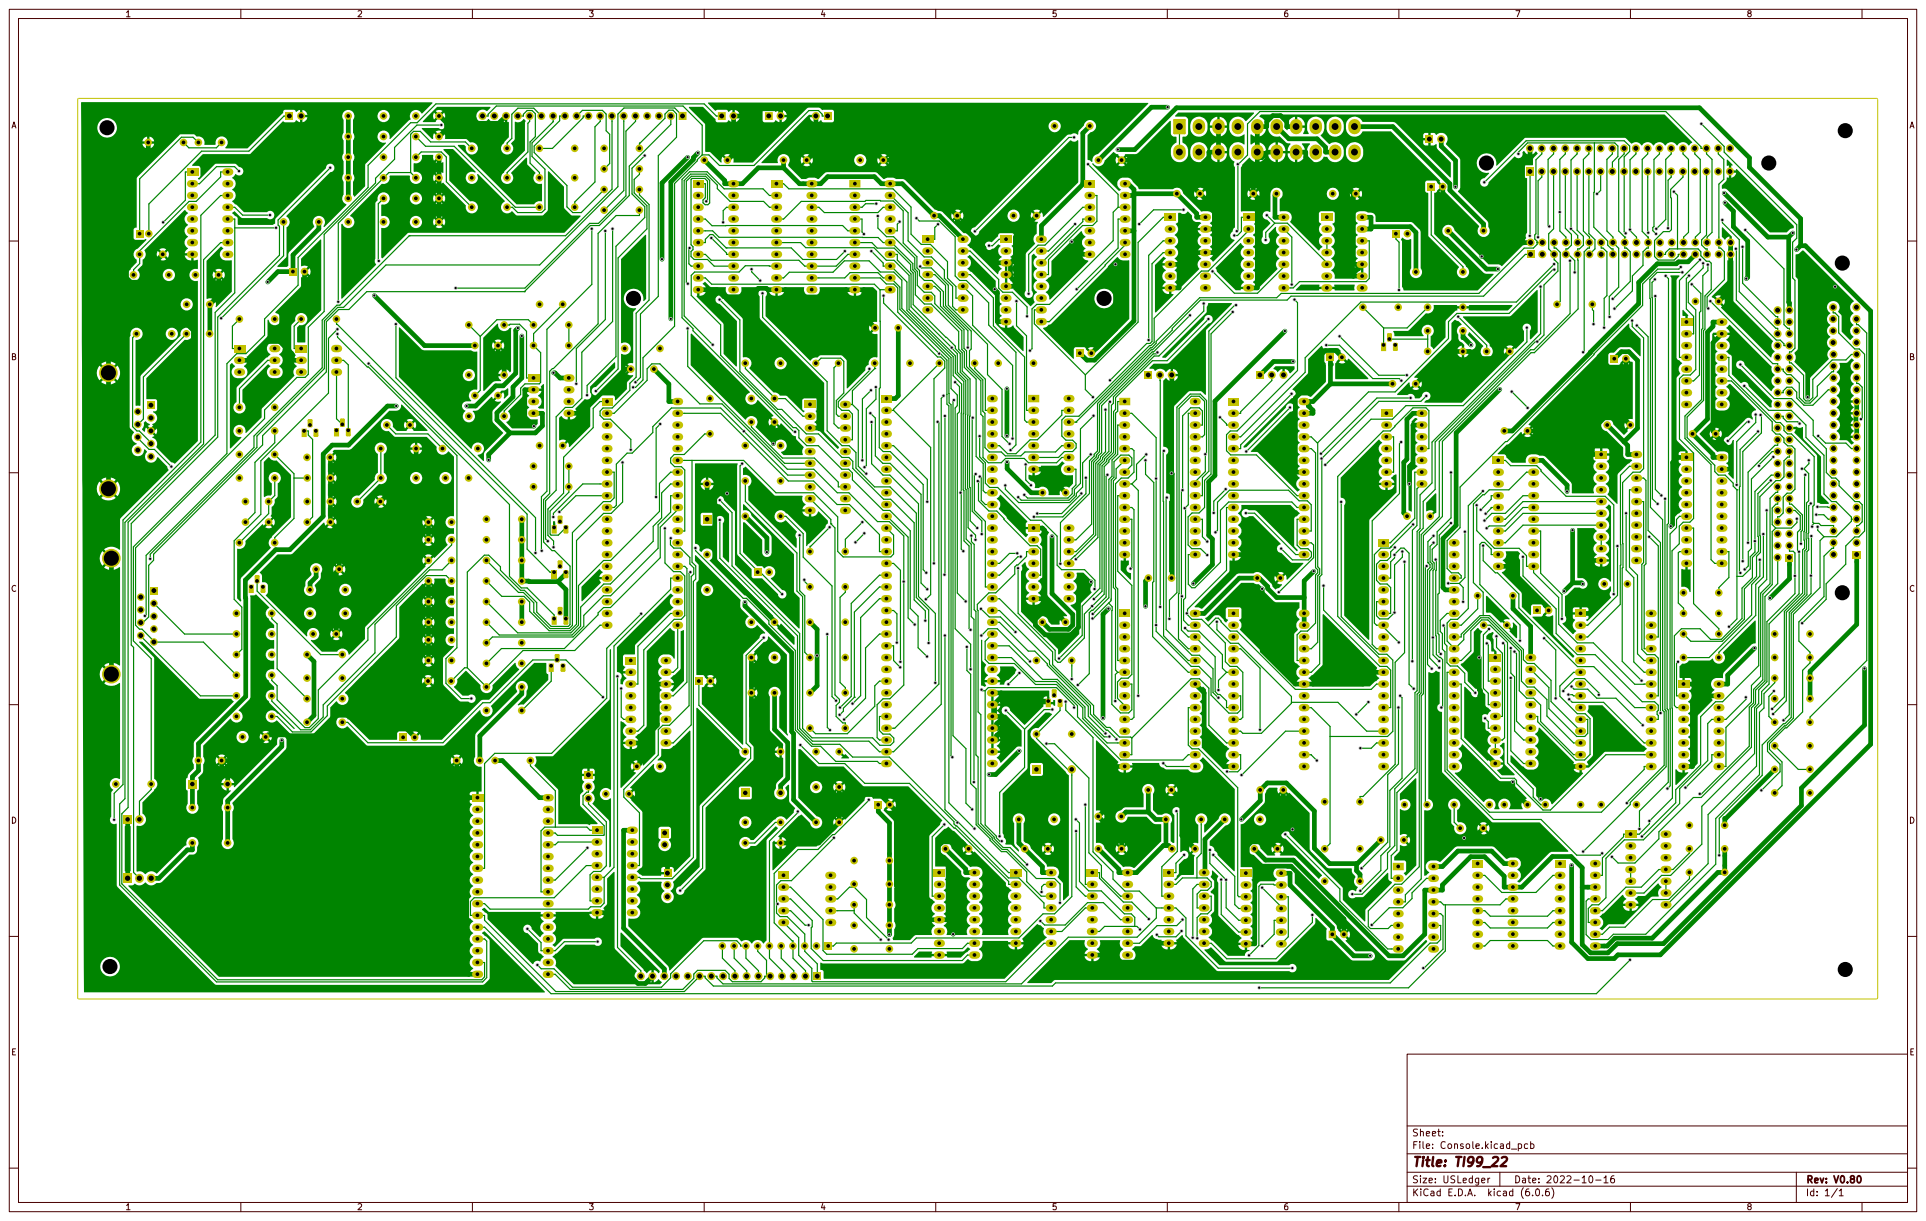
[picture p109: page 2]

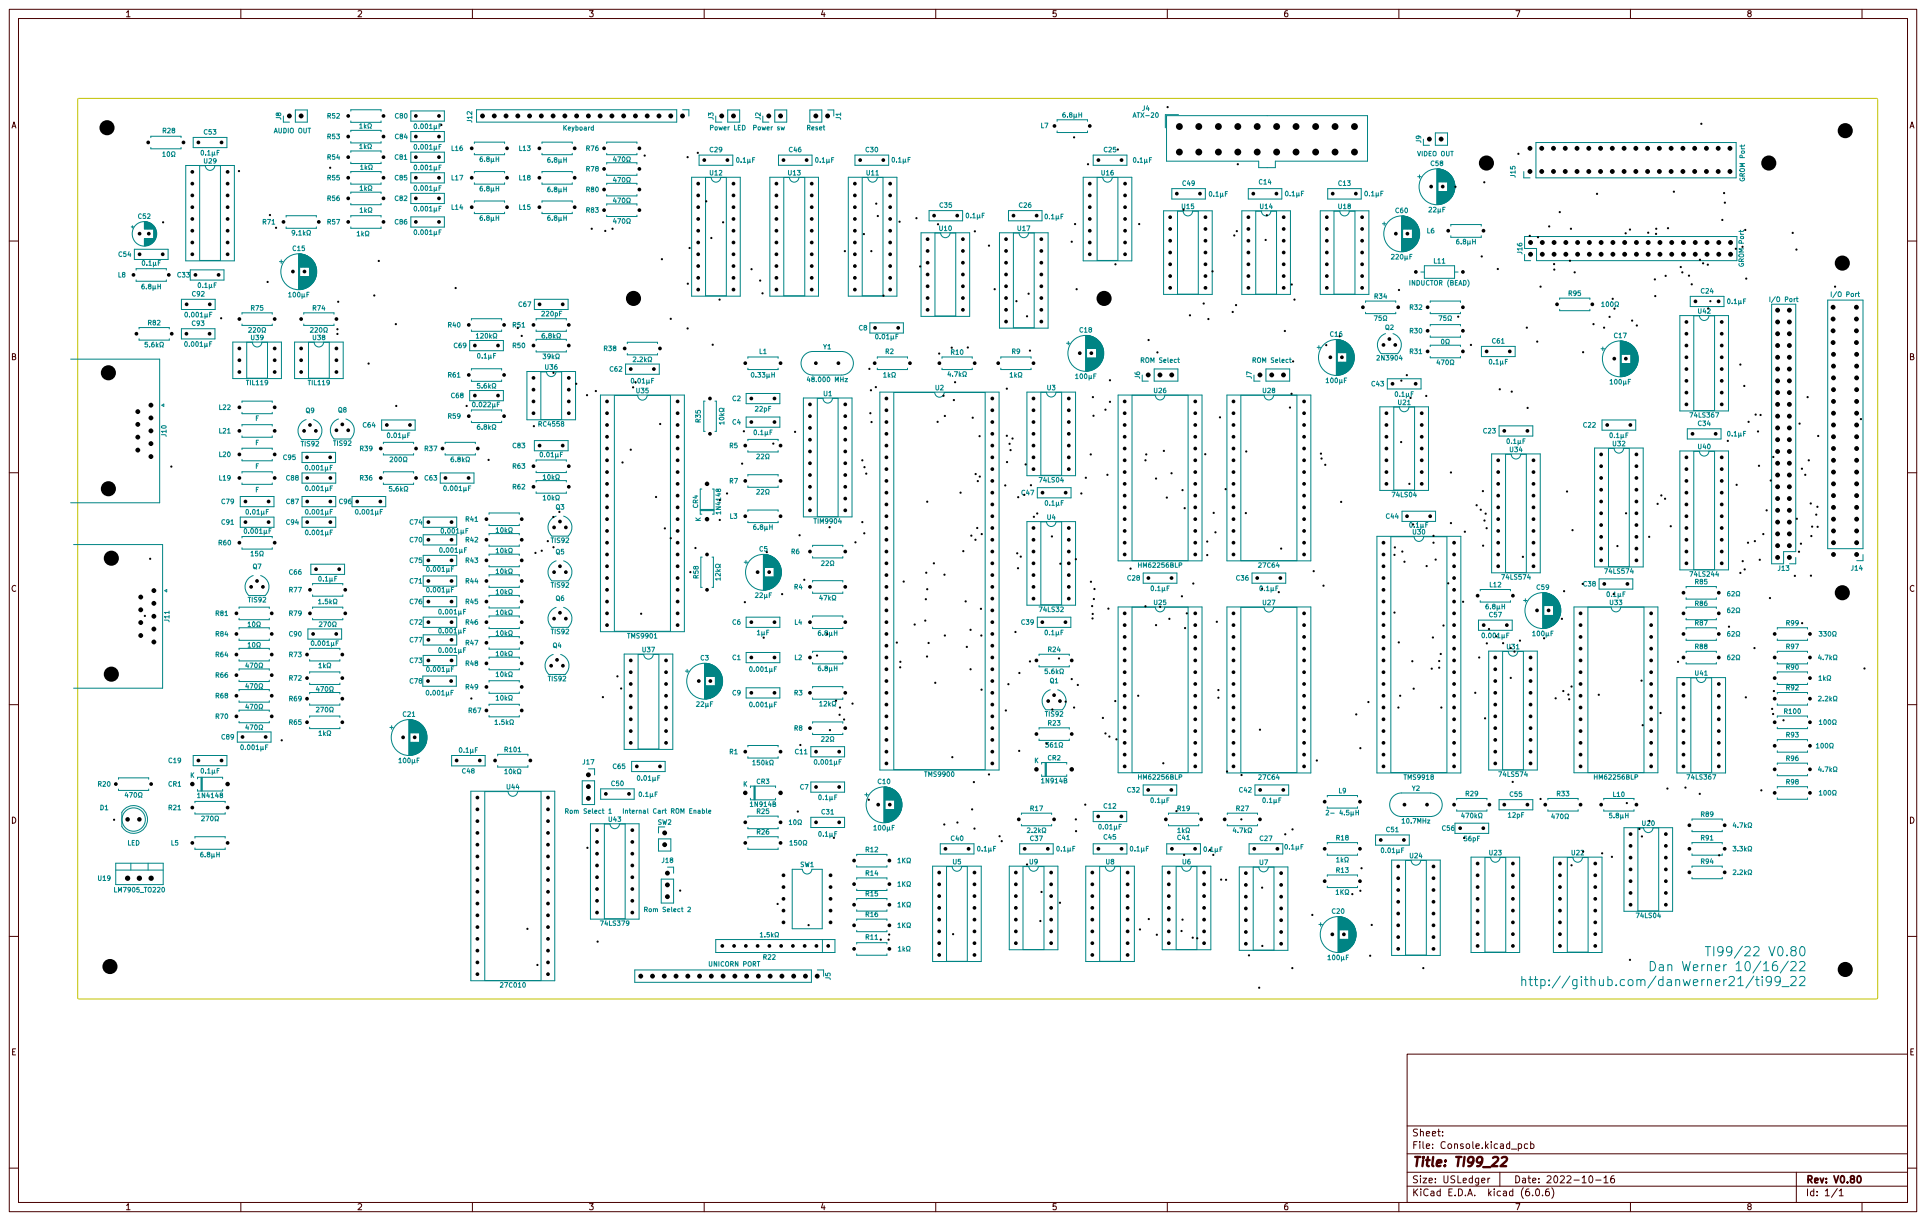
[picture p110: page 3]

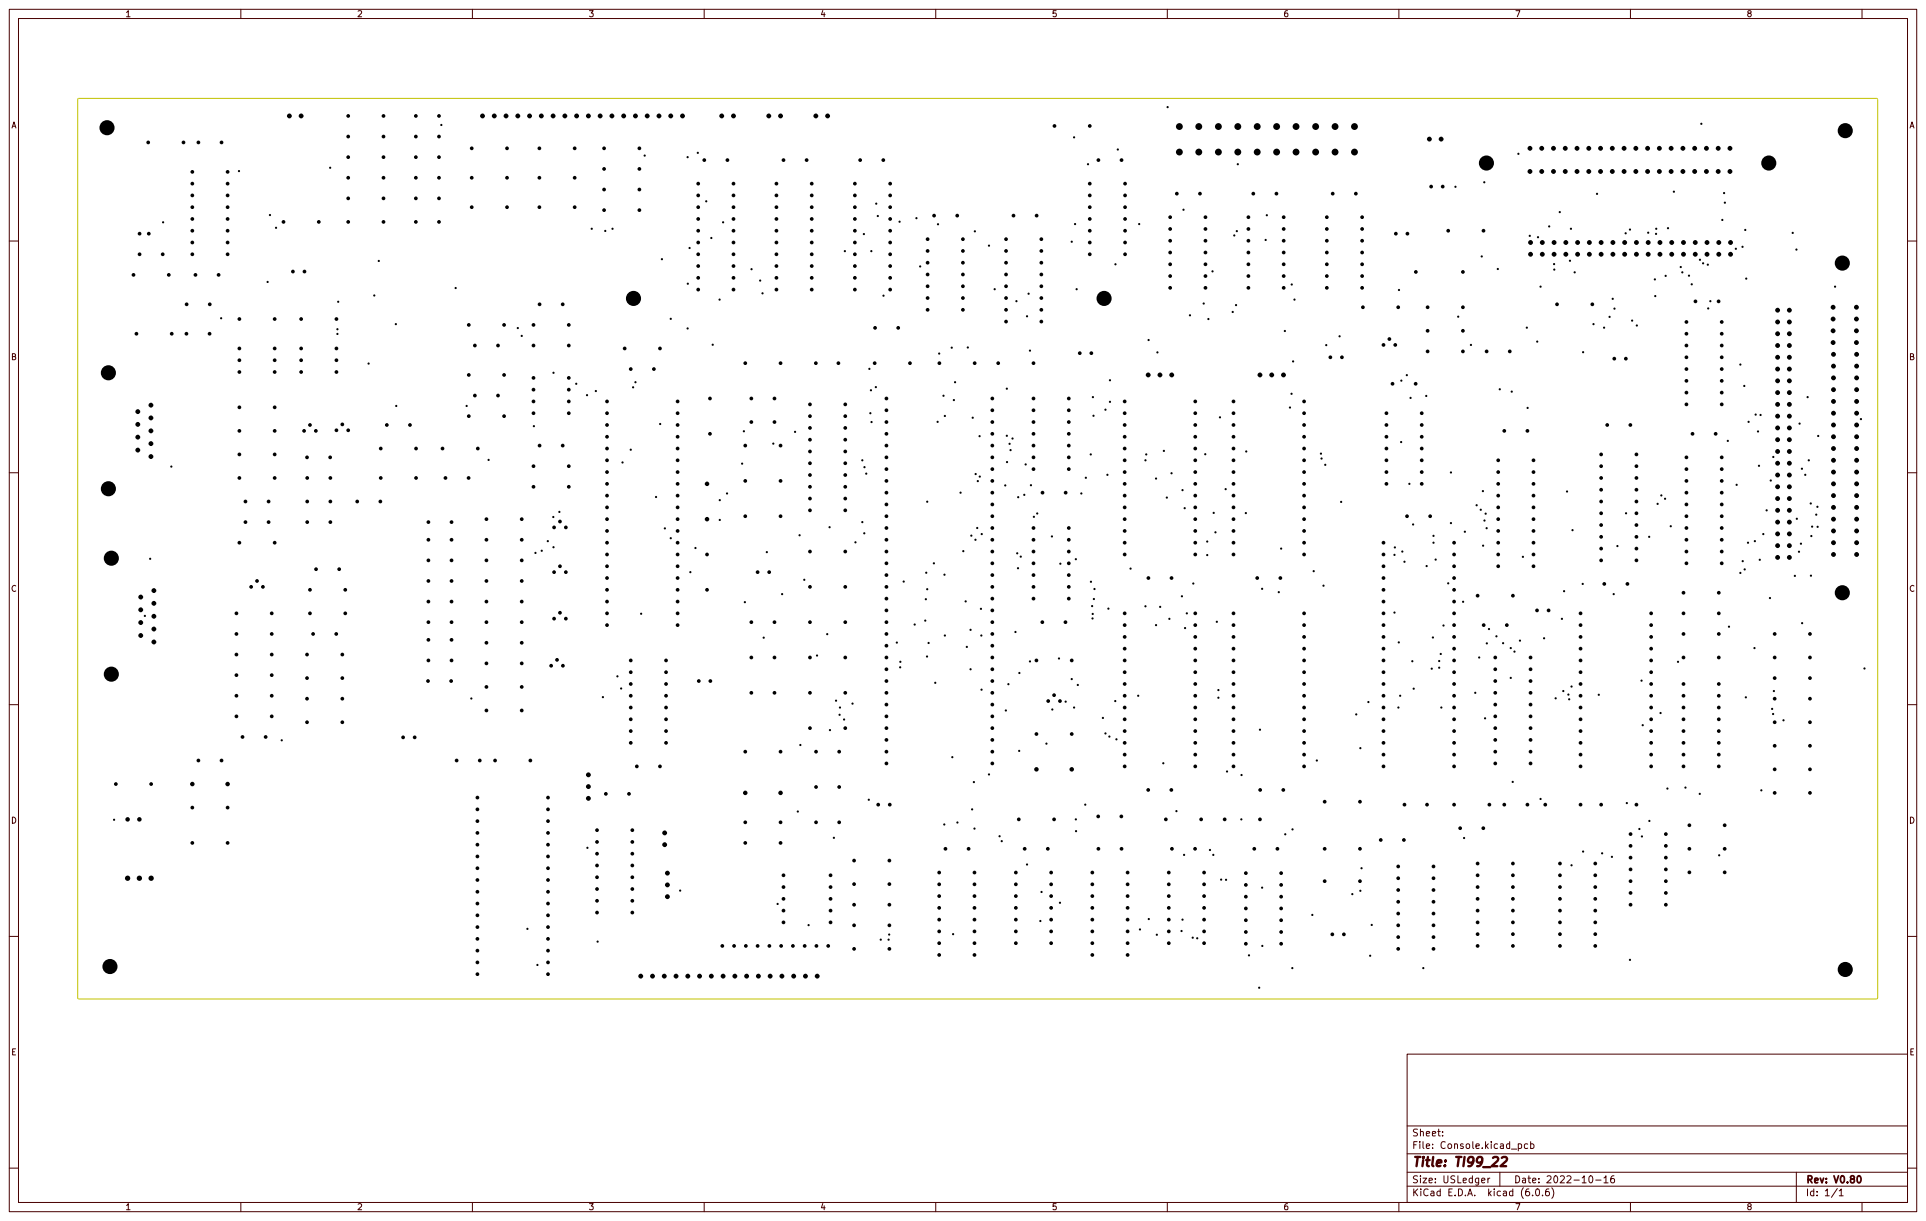
[picture p111: page 4]

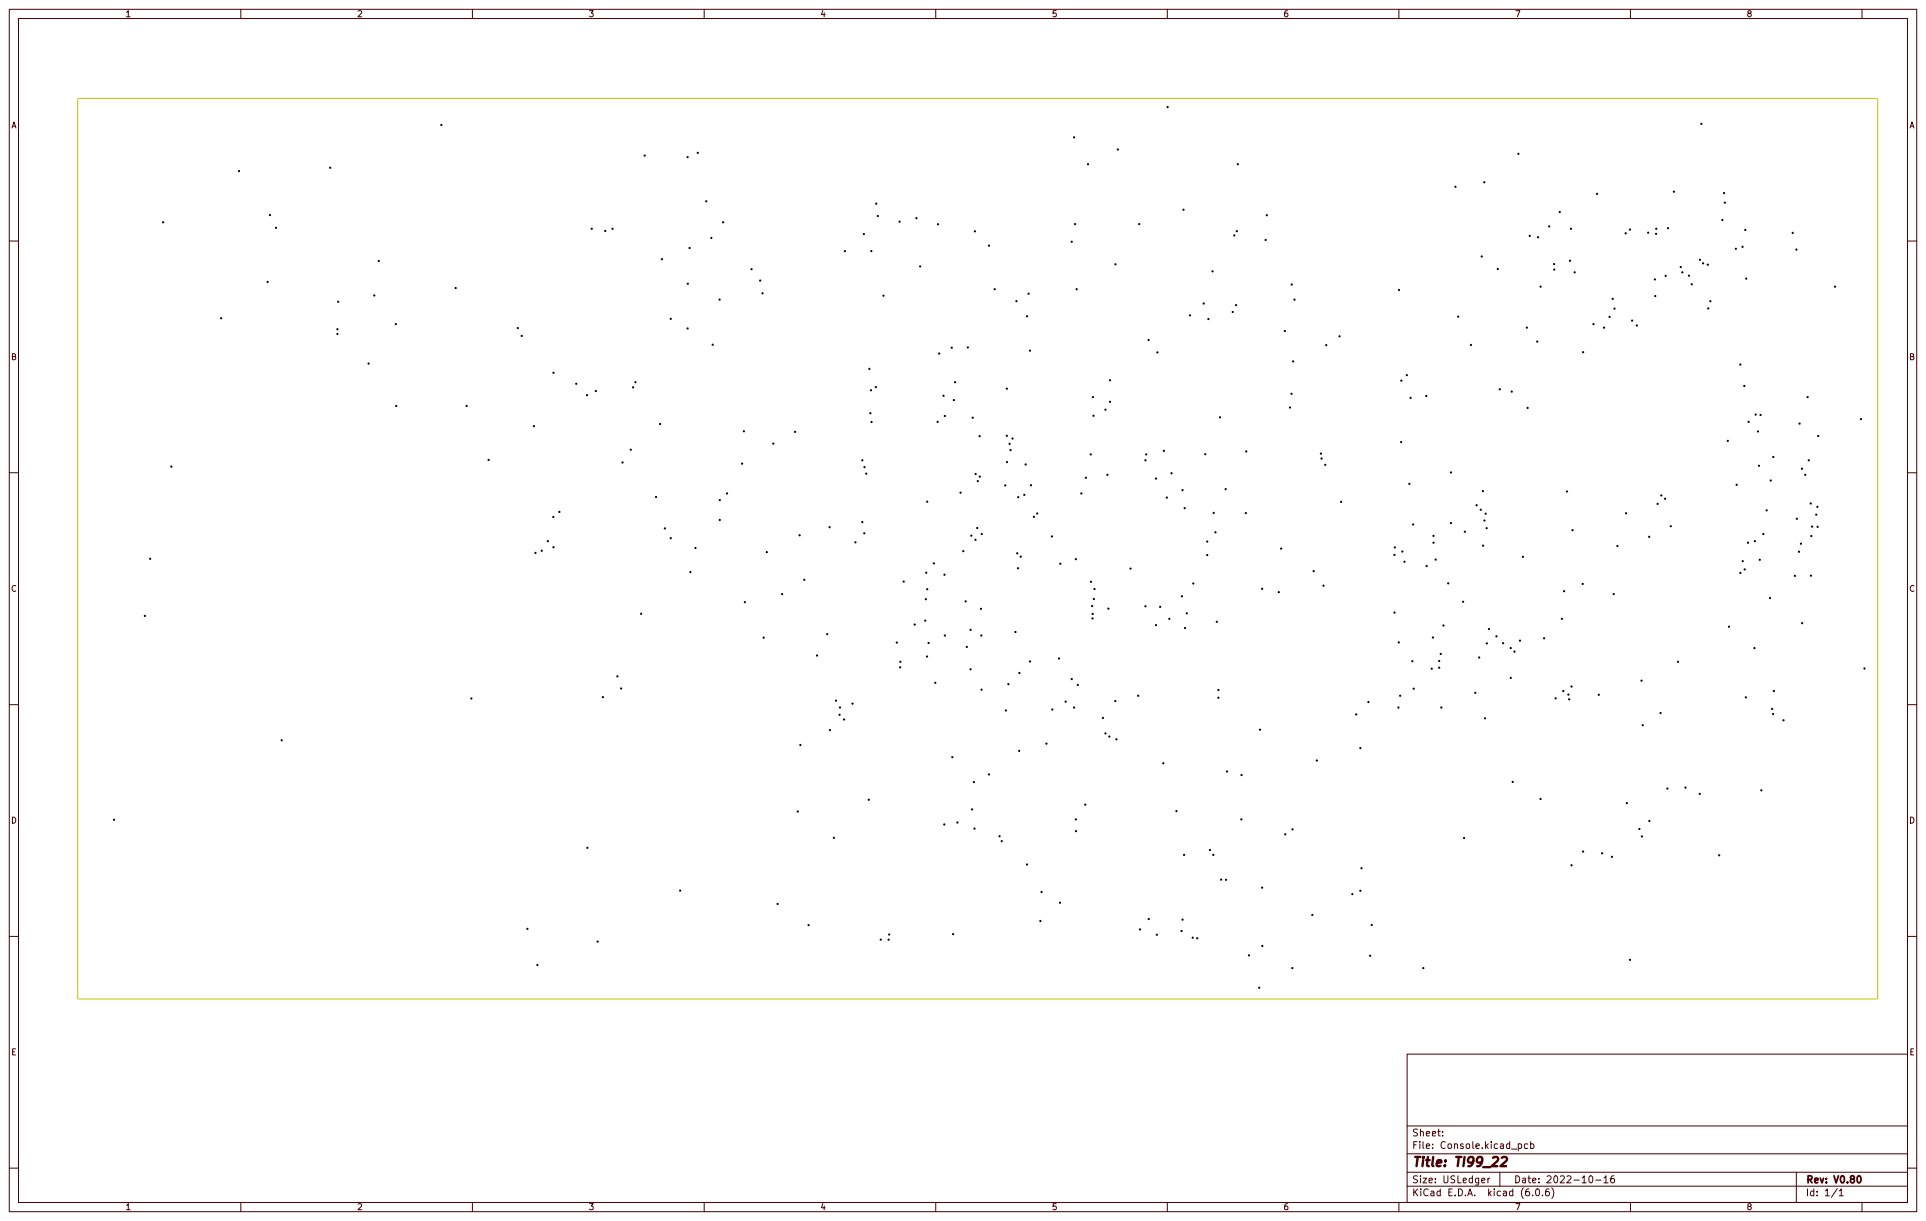
[picture p112: page 5]
