danwerner21/TI99_22/mainboard/mainboard_v0.80.pdf

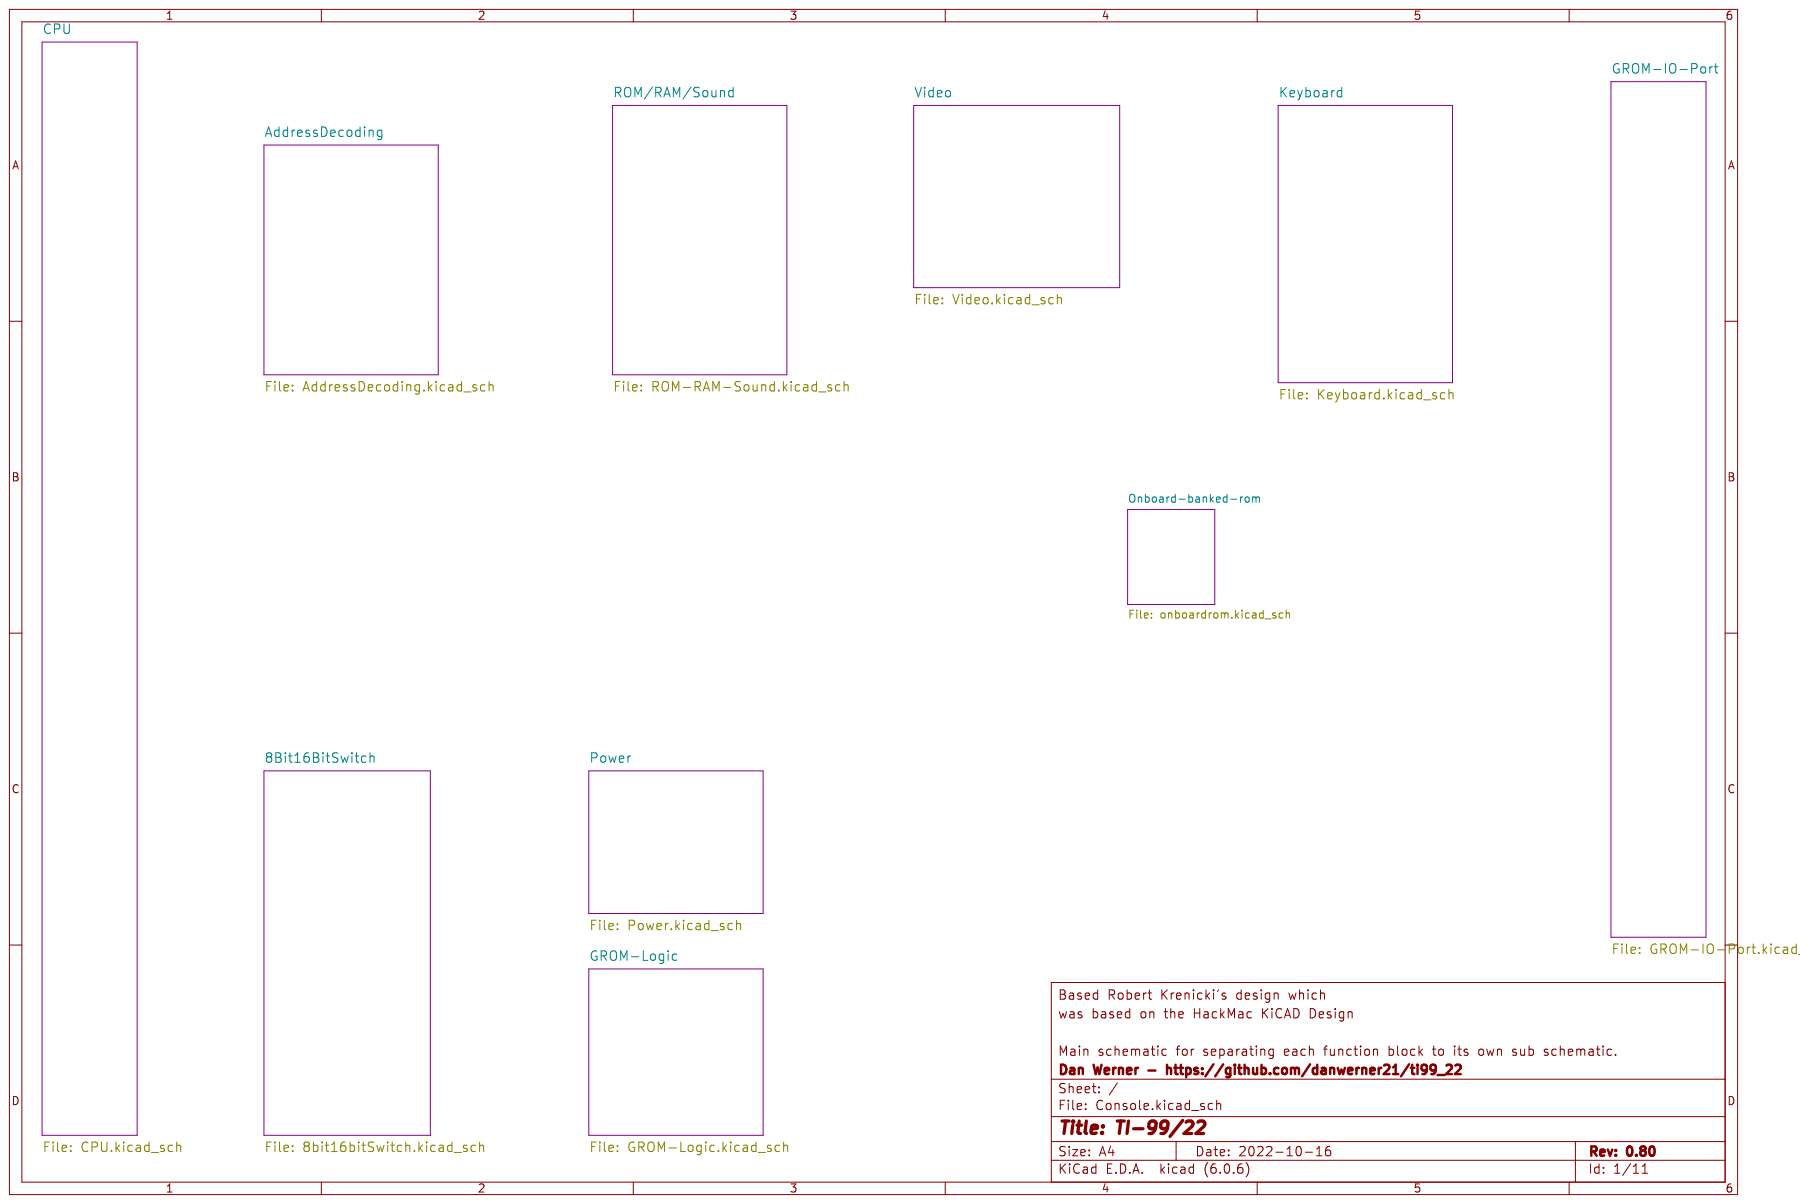
[picture p113: page 1]

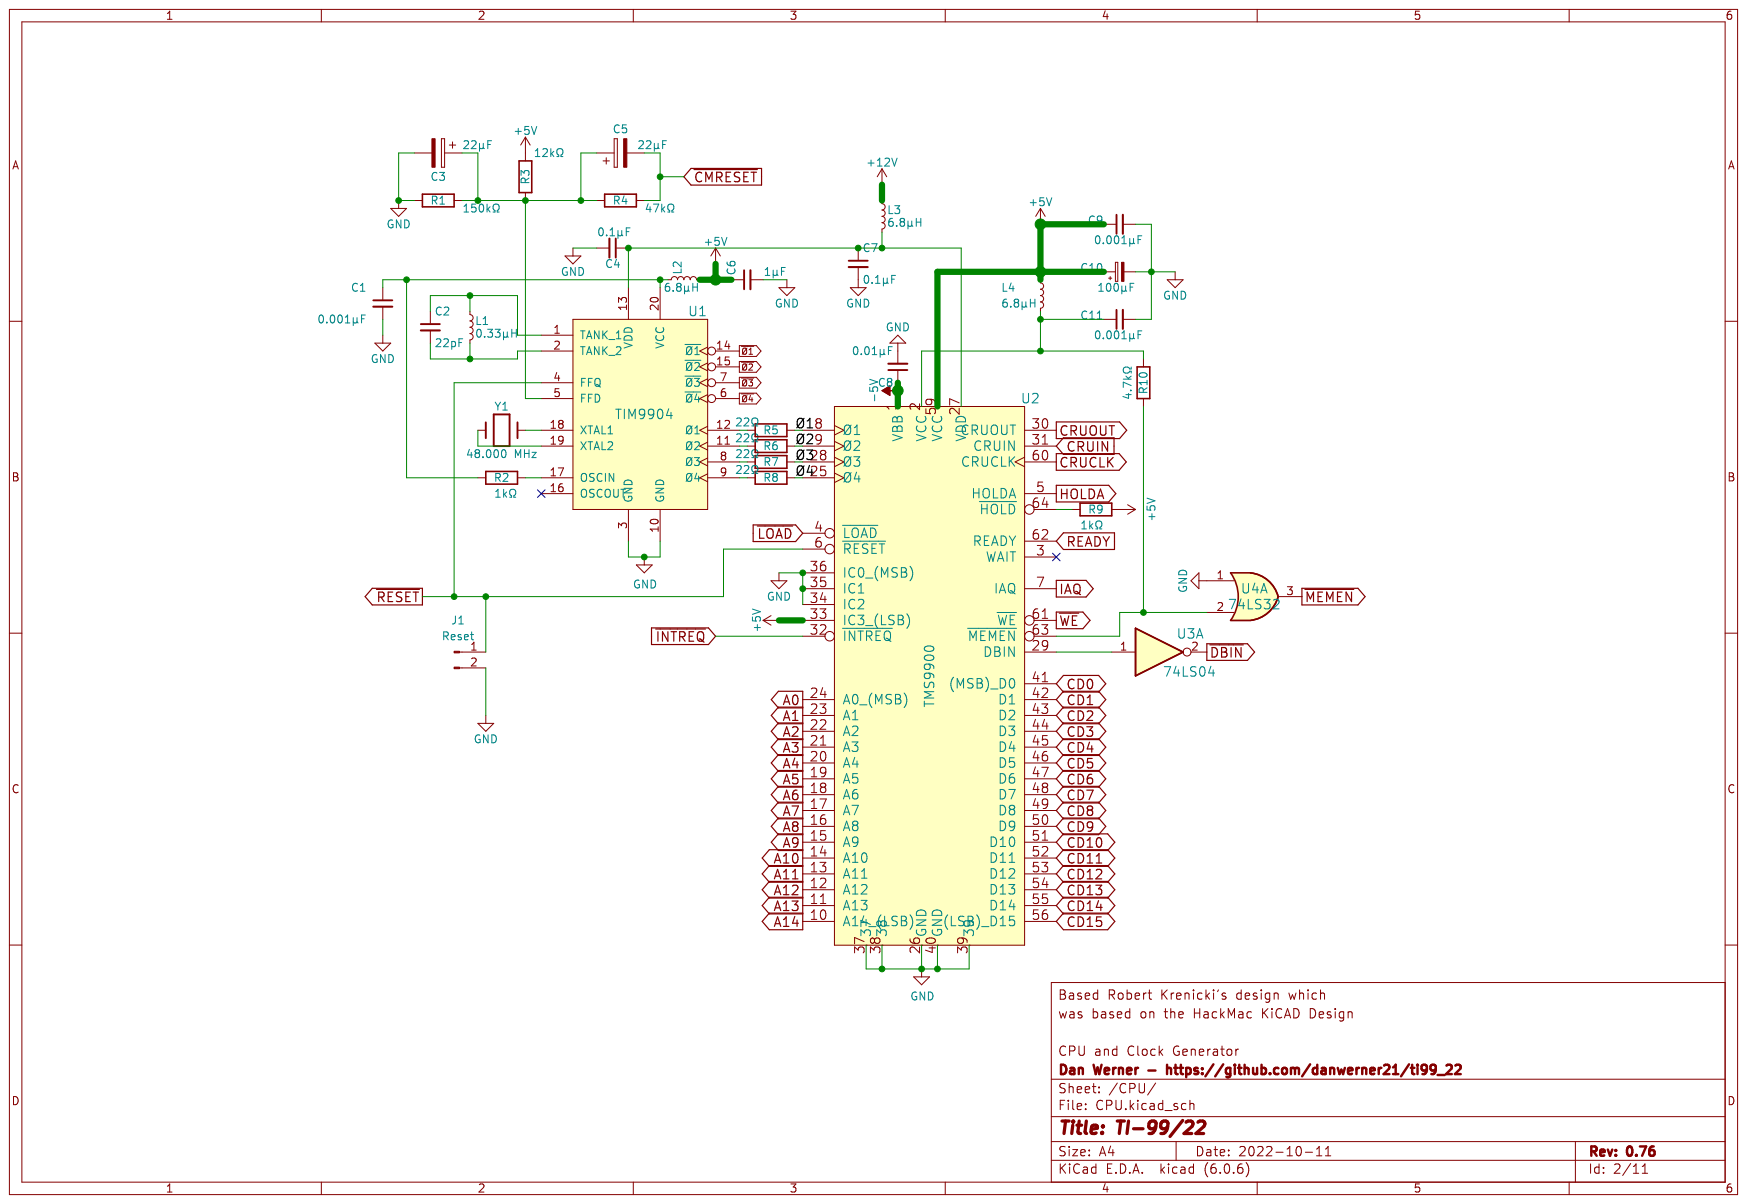
[picture p114: page 2]

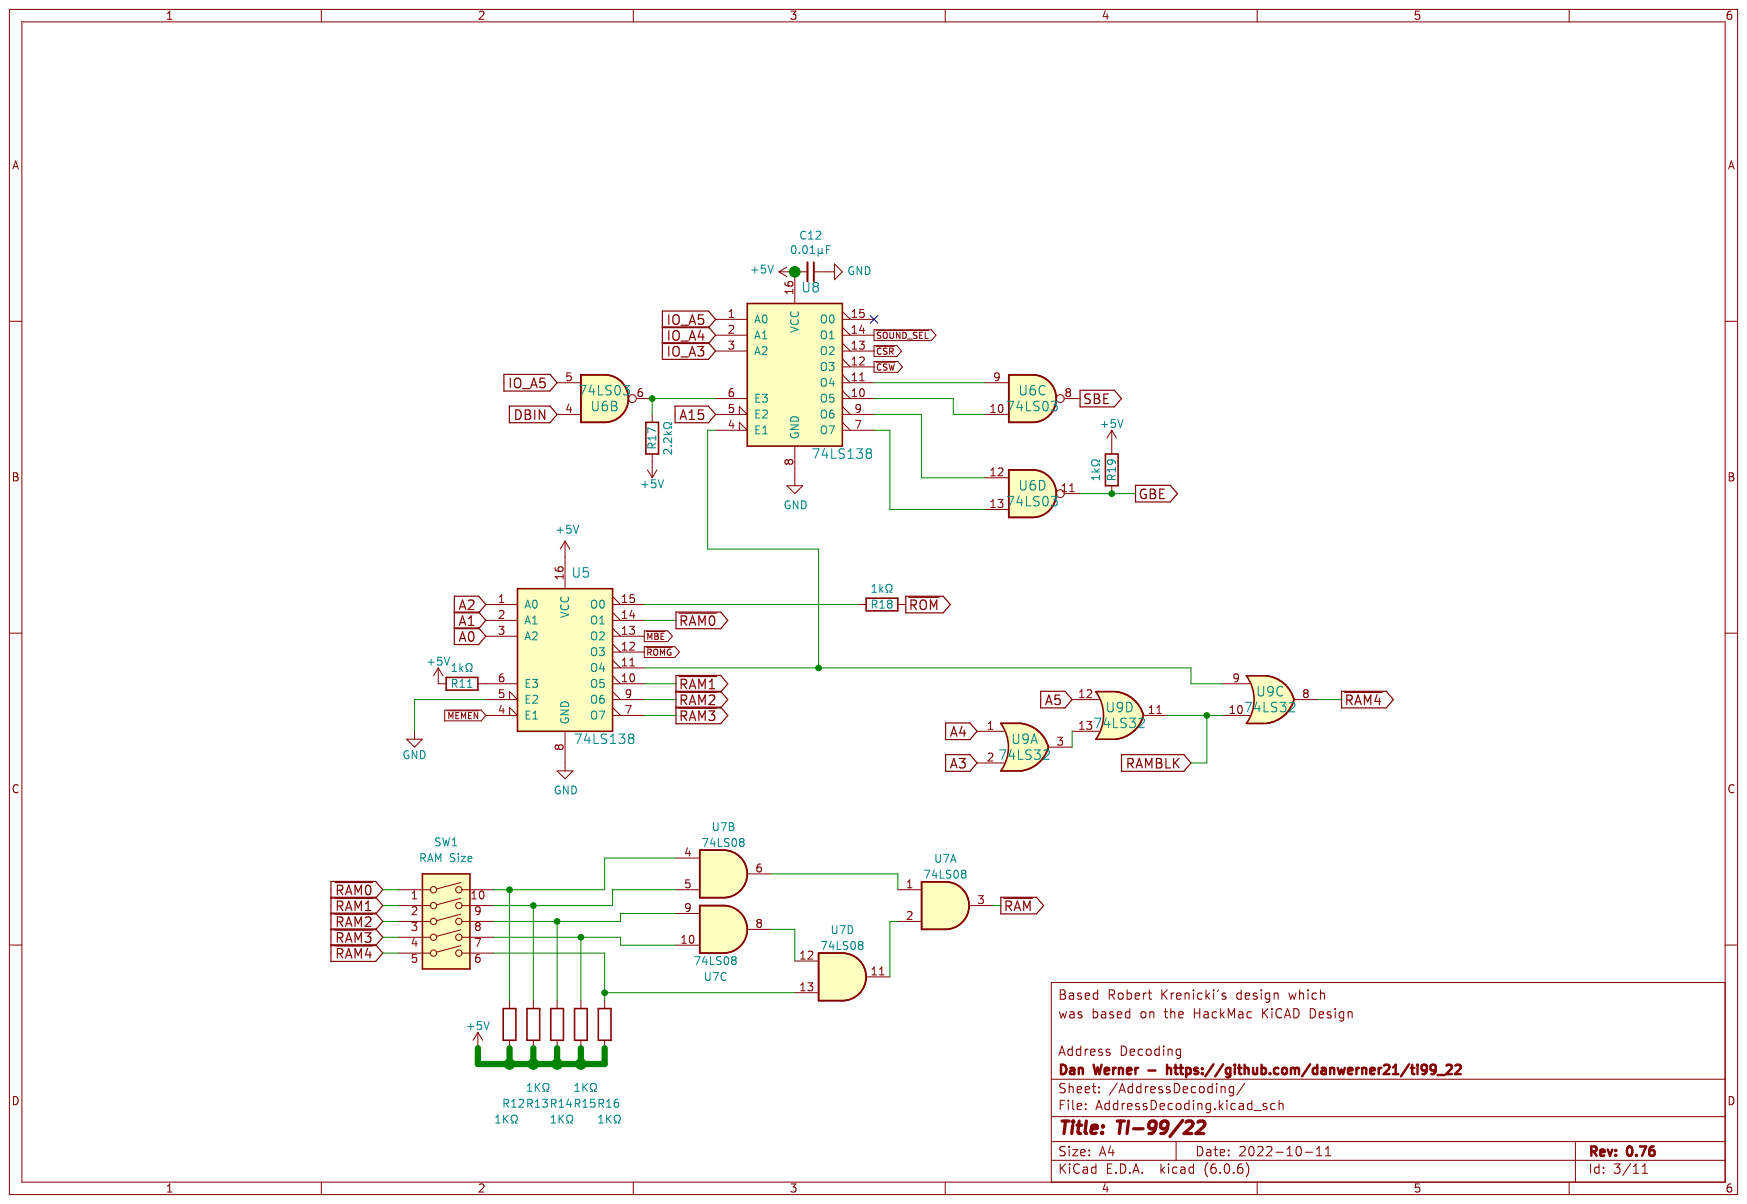
[picture p115: page 3]

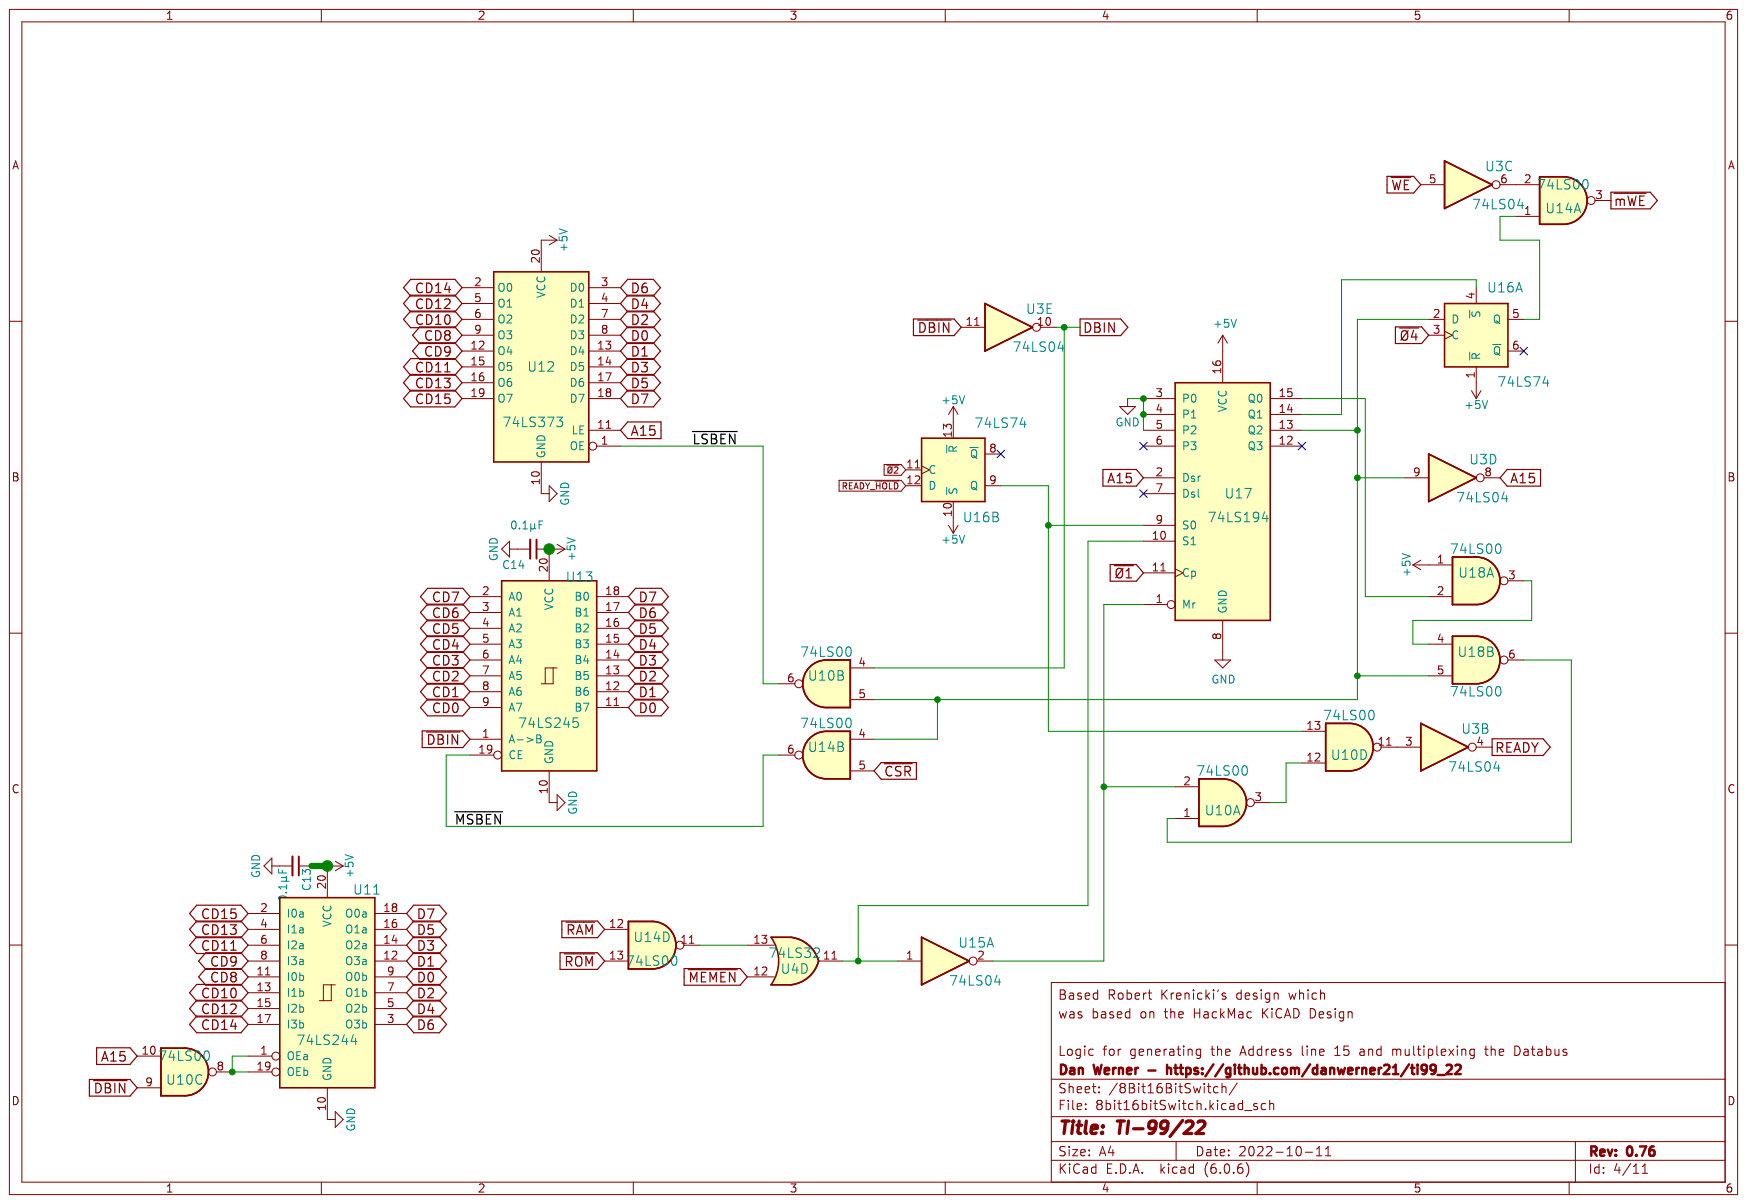
[picture p116: page 4]

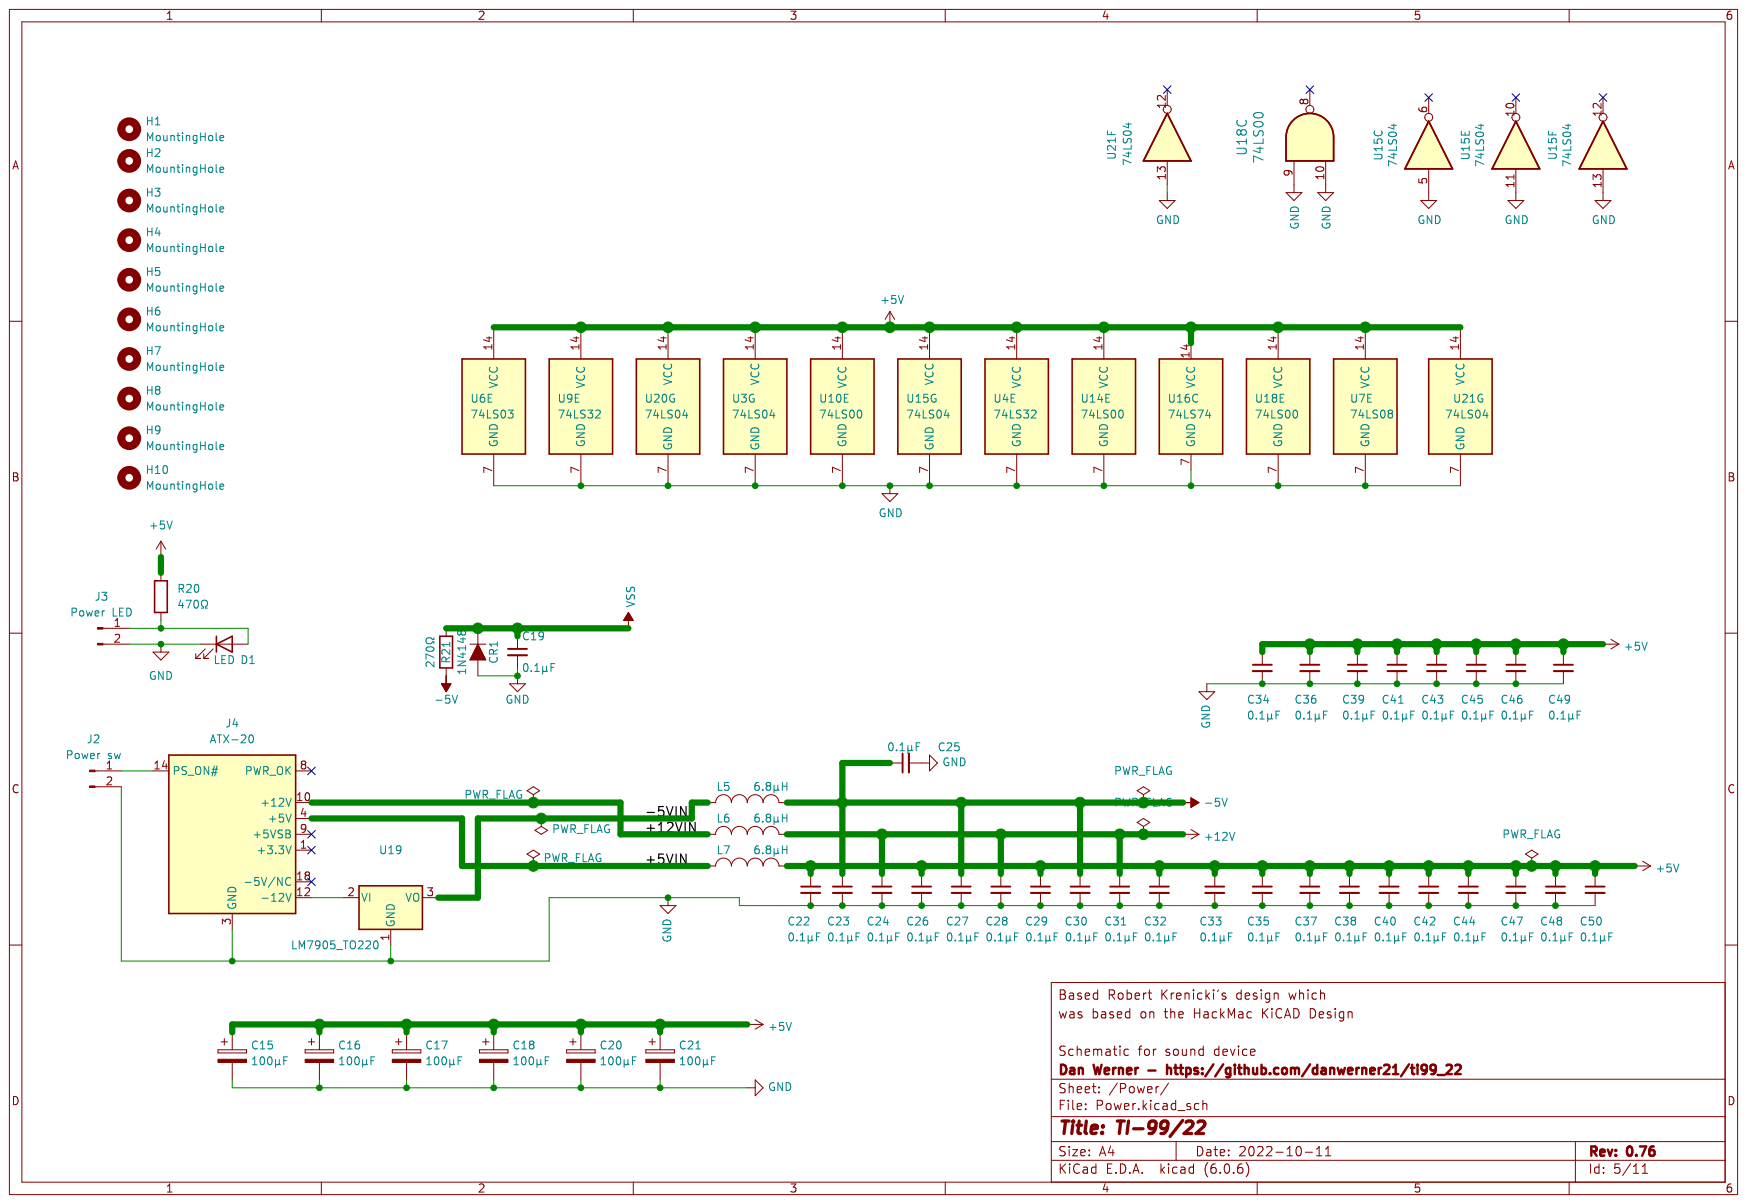
[picture p117: page 5]

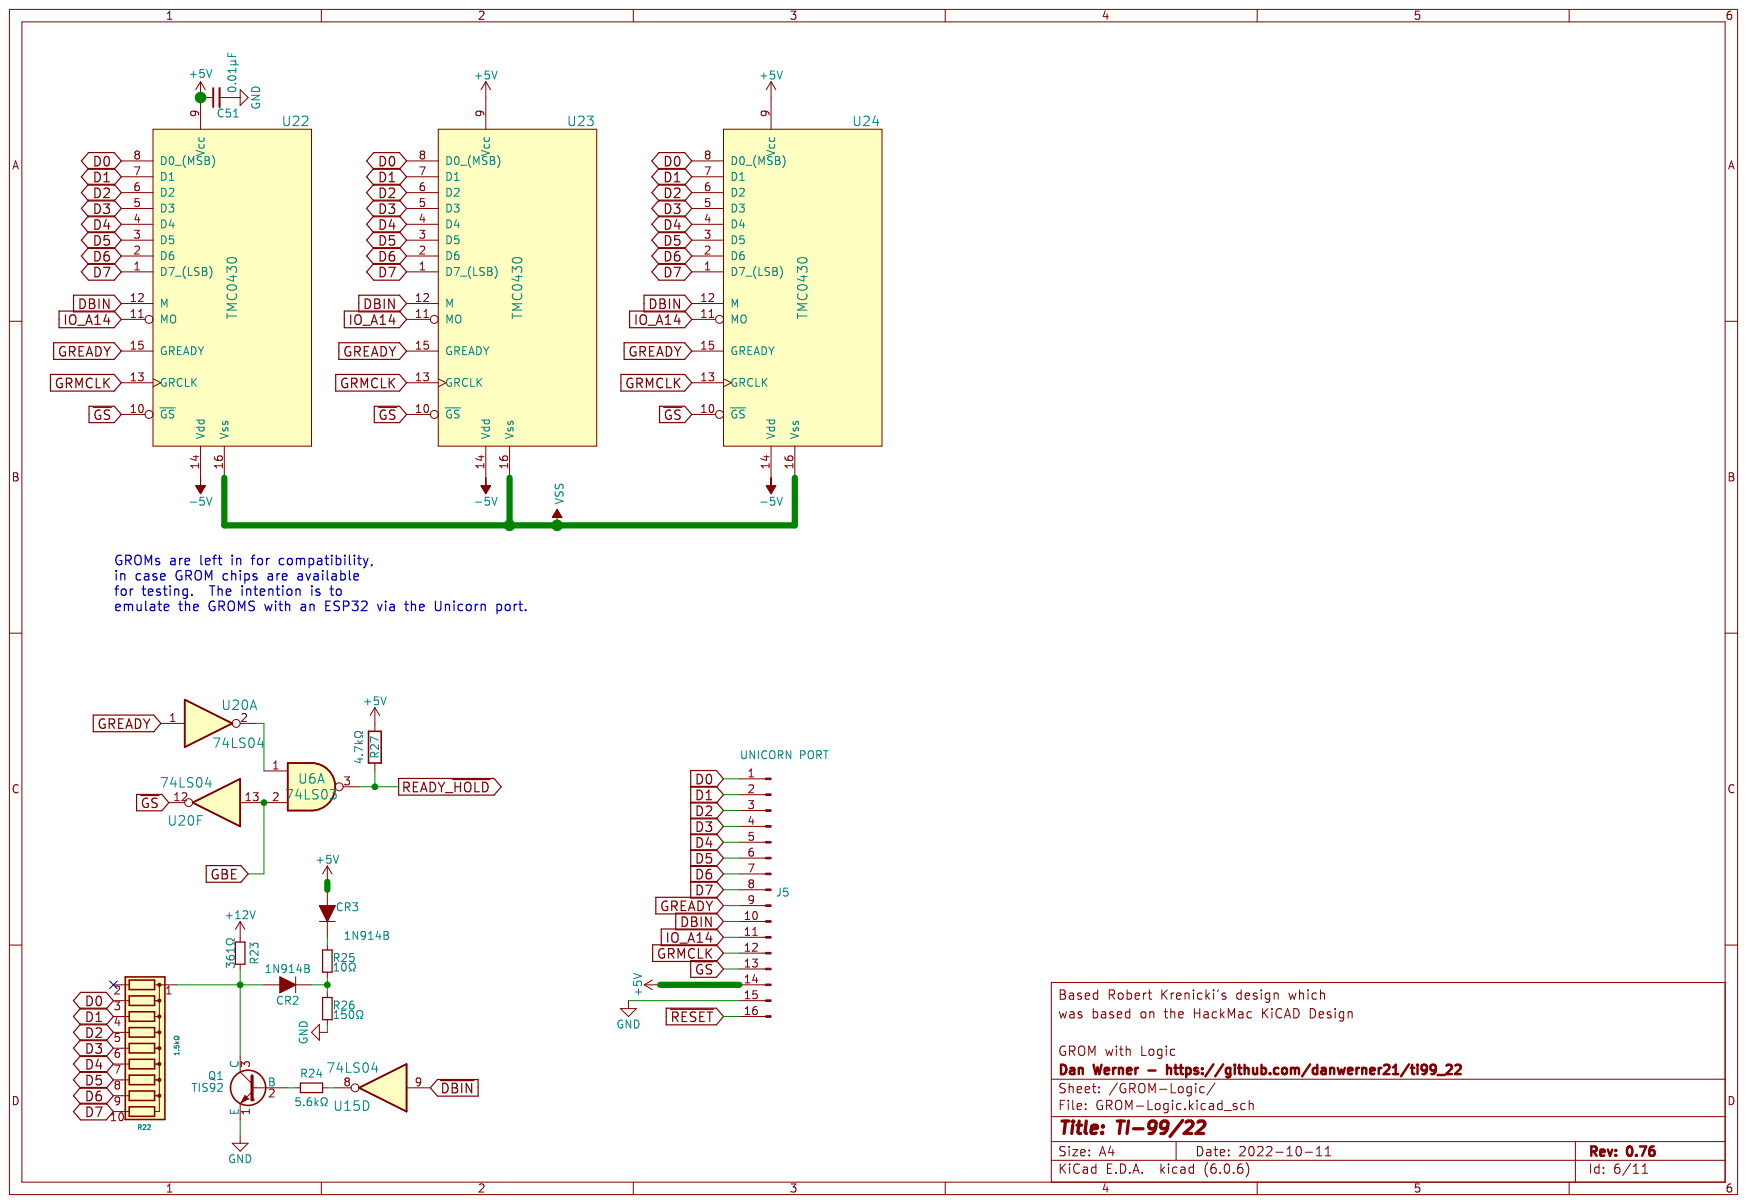
[picture p118: page 6]

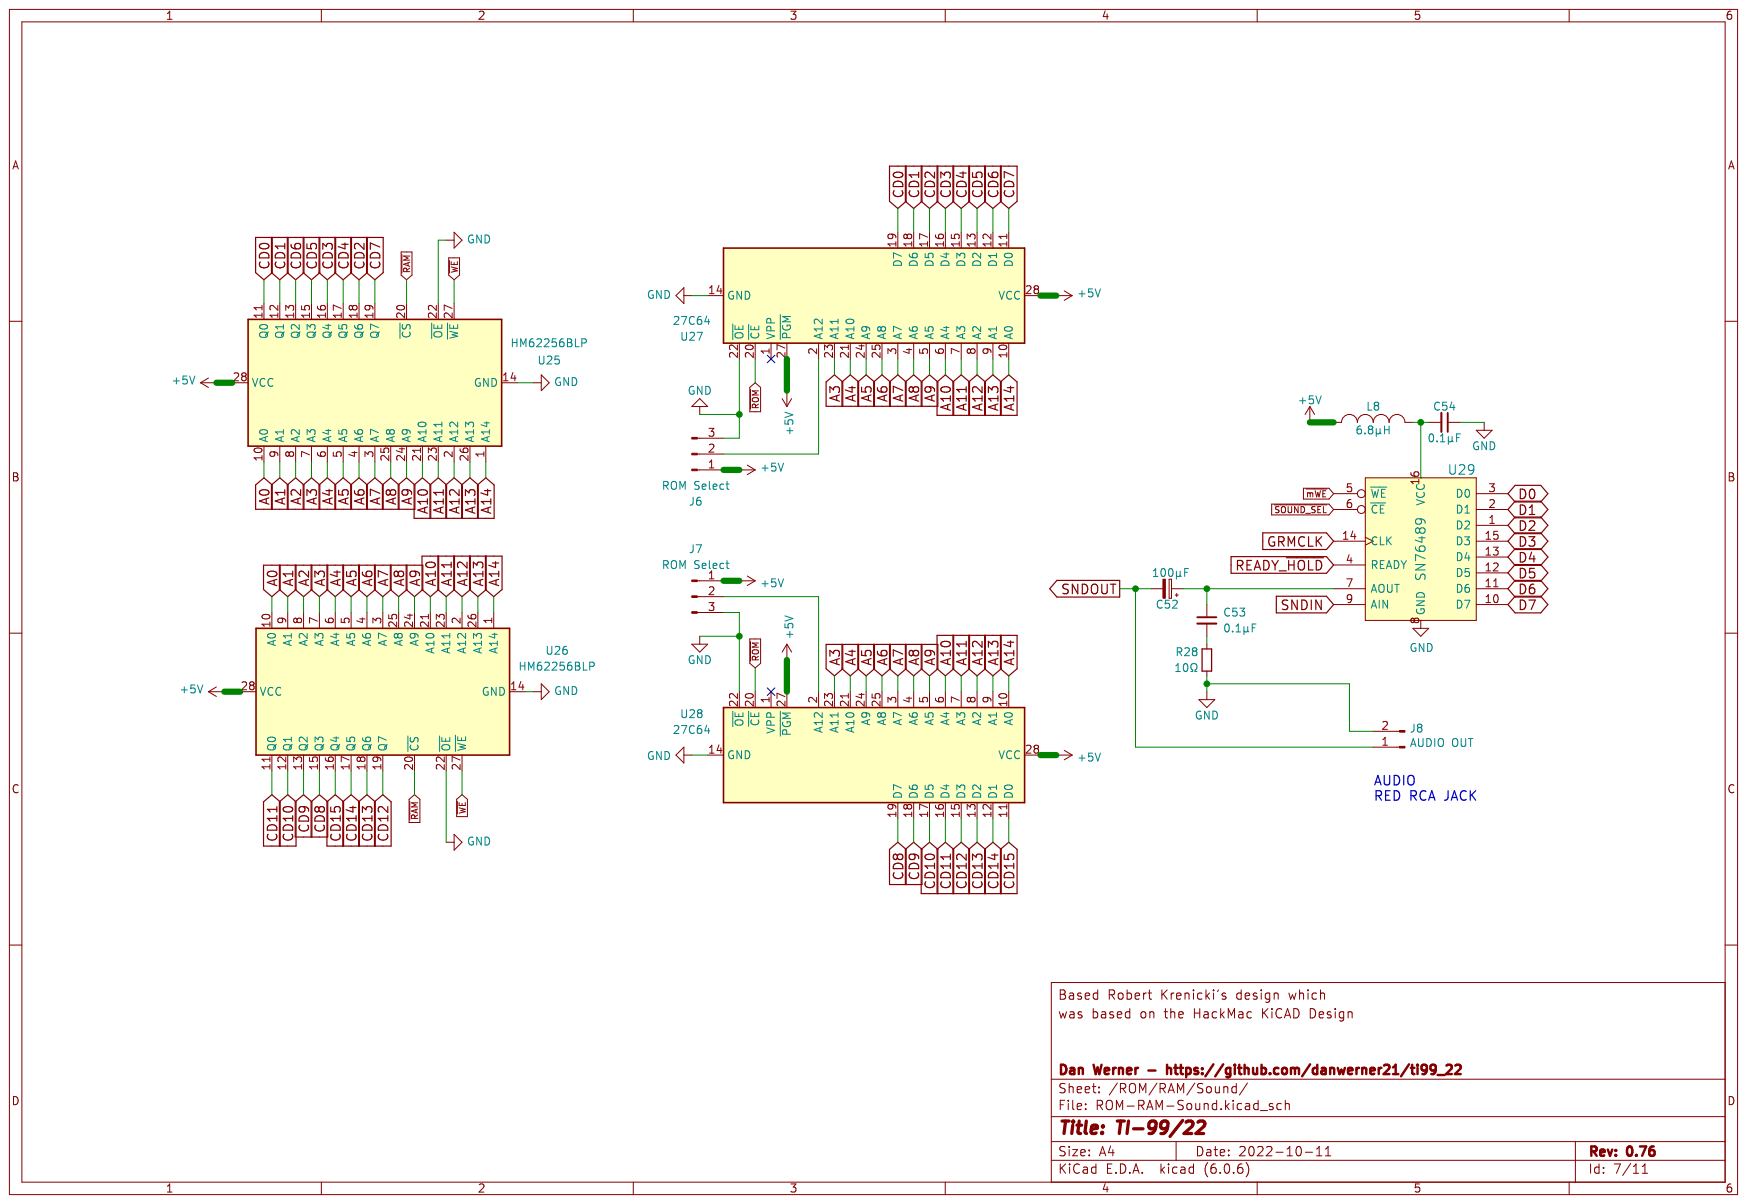
[picture p119: page 7]

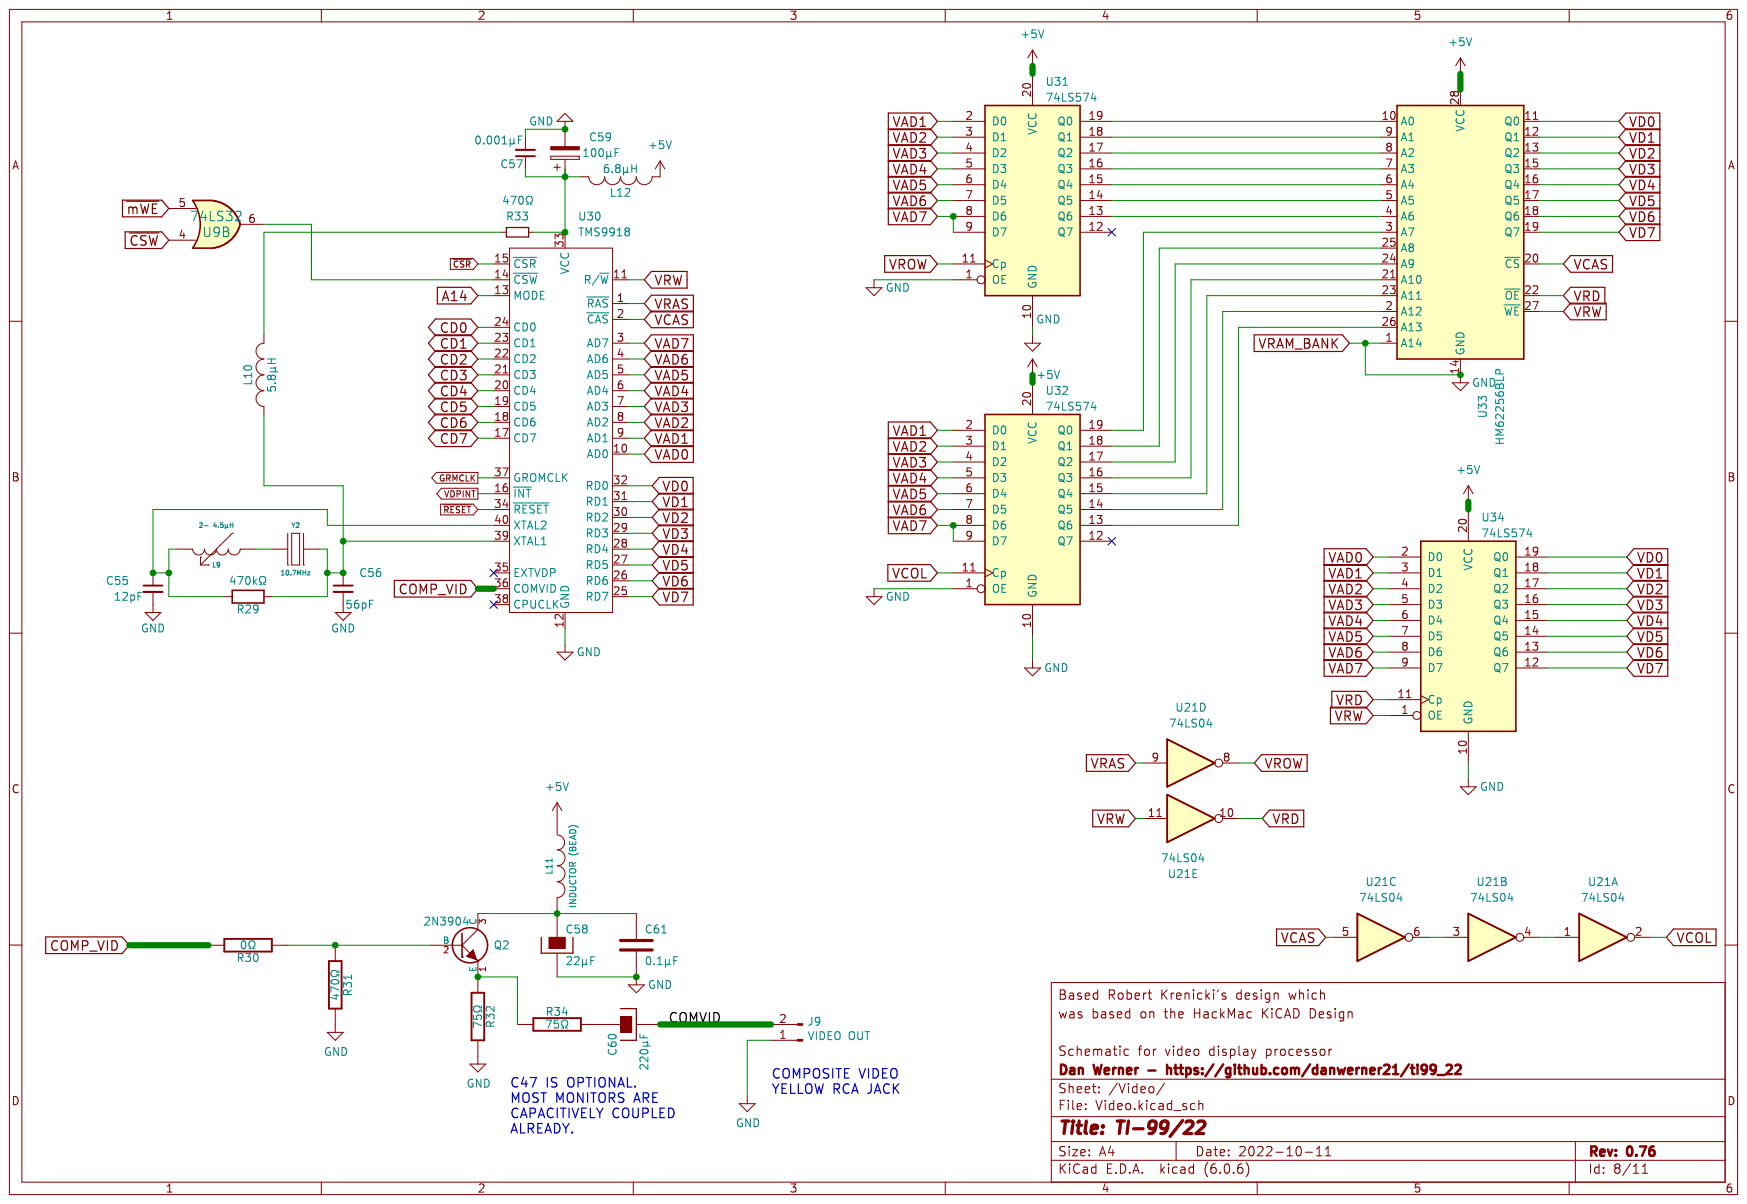
[picture p120: page 8]

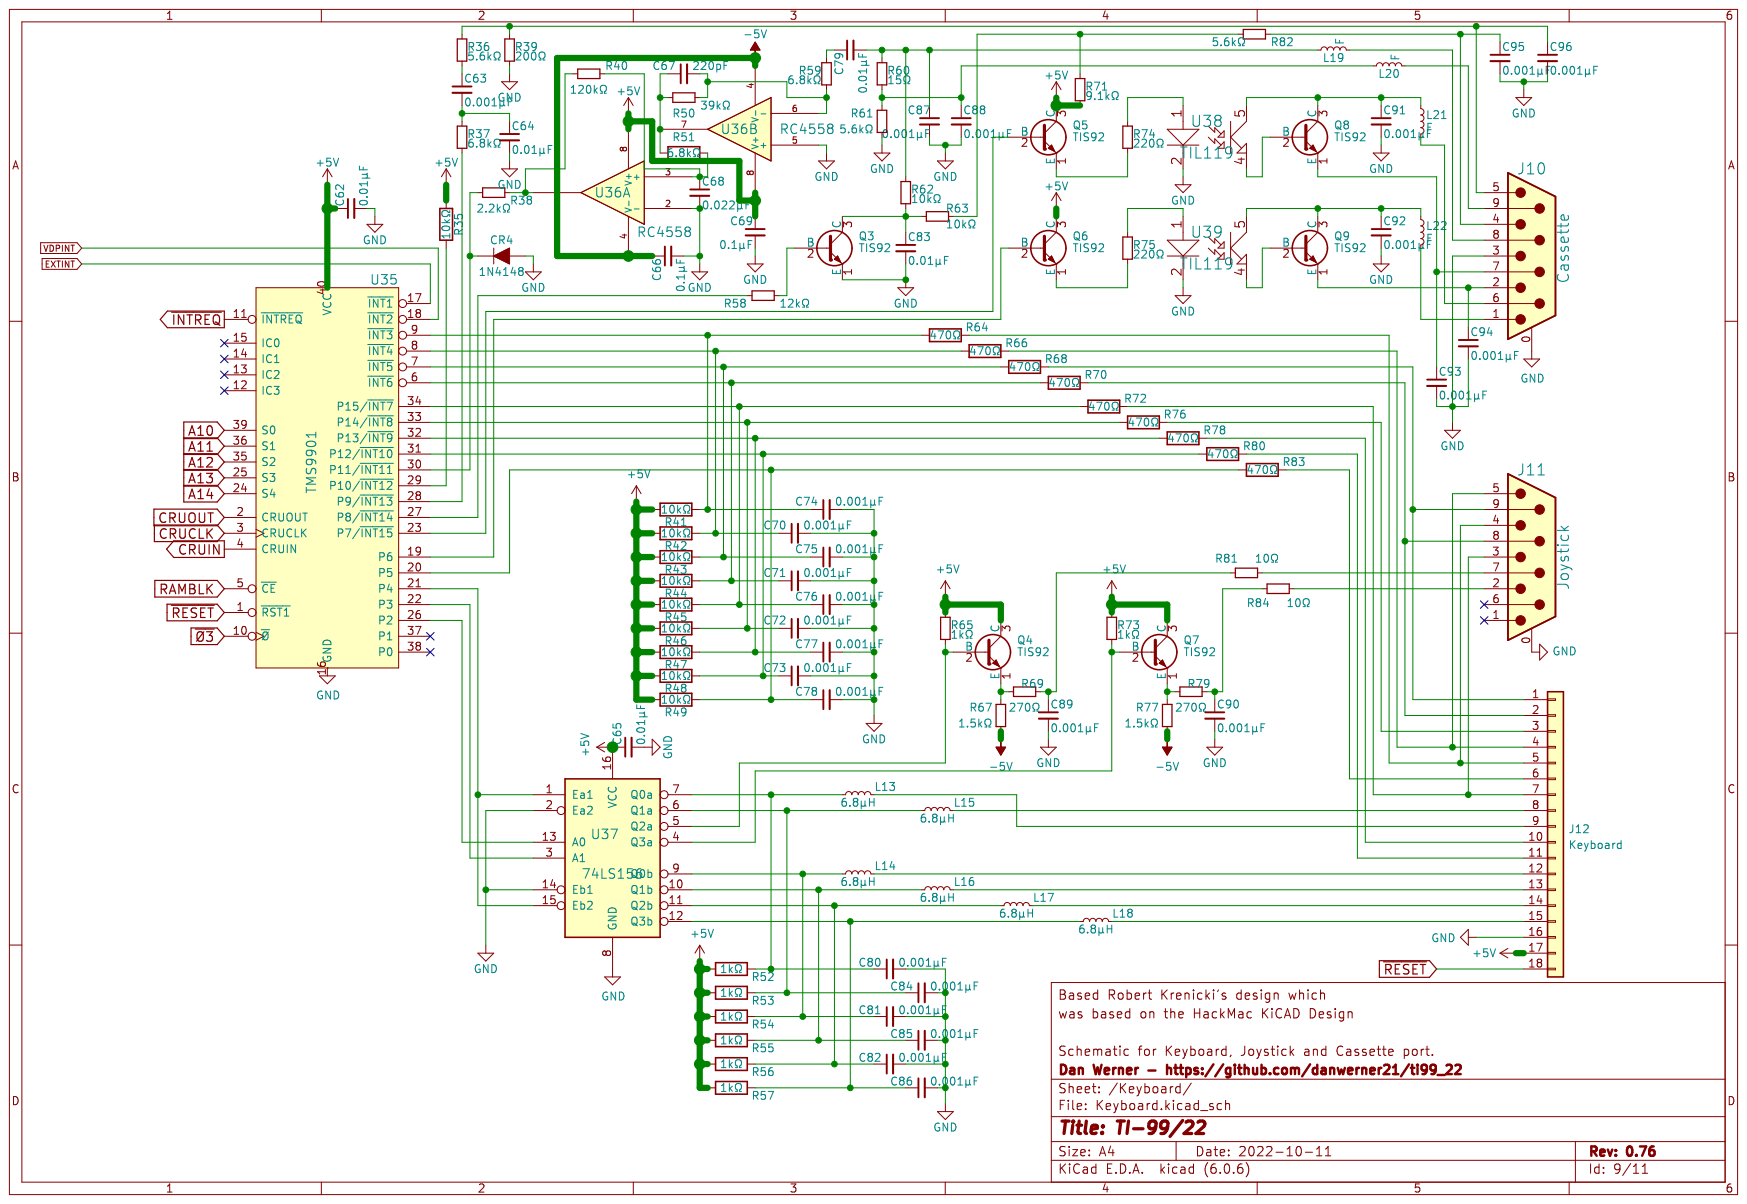
[picture p121: page 9]

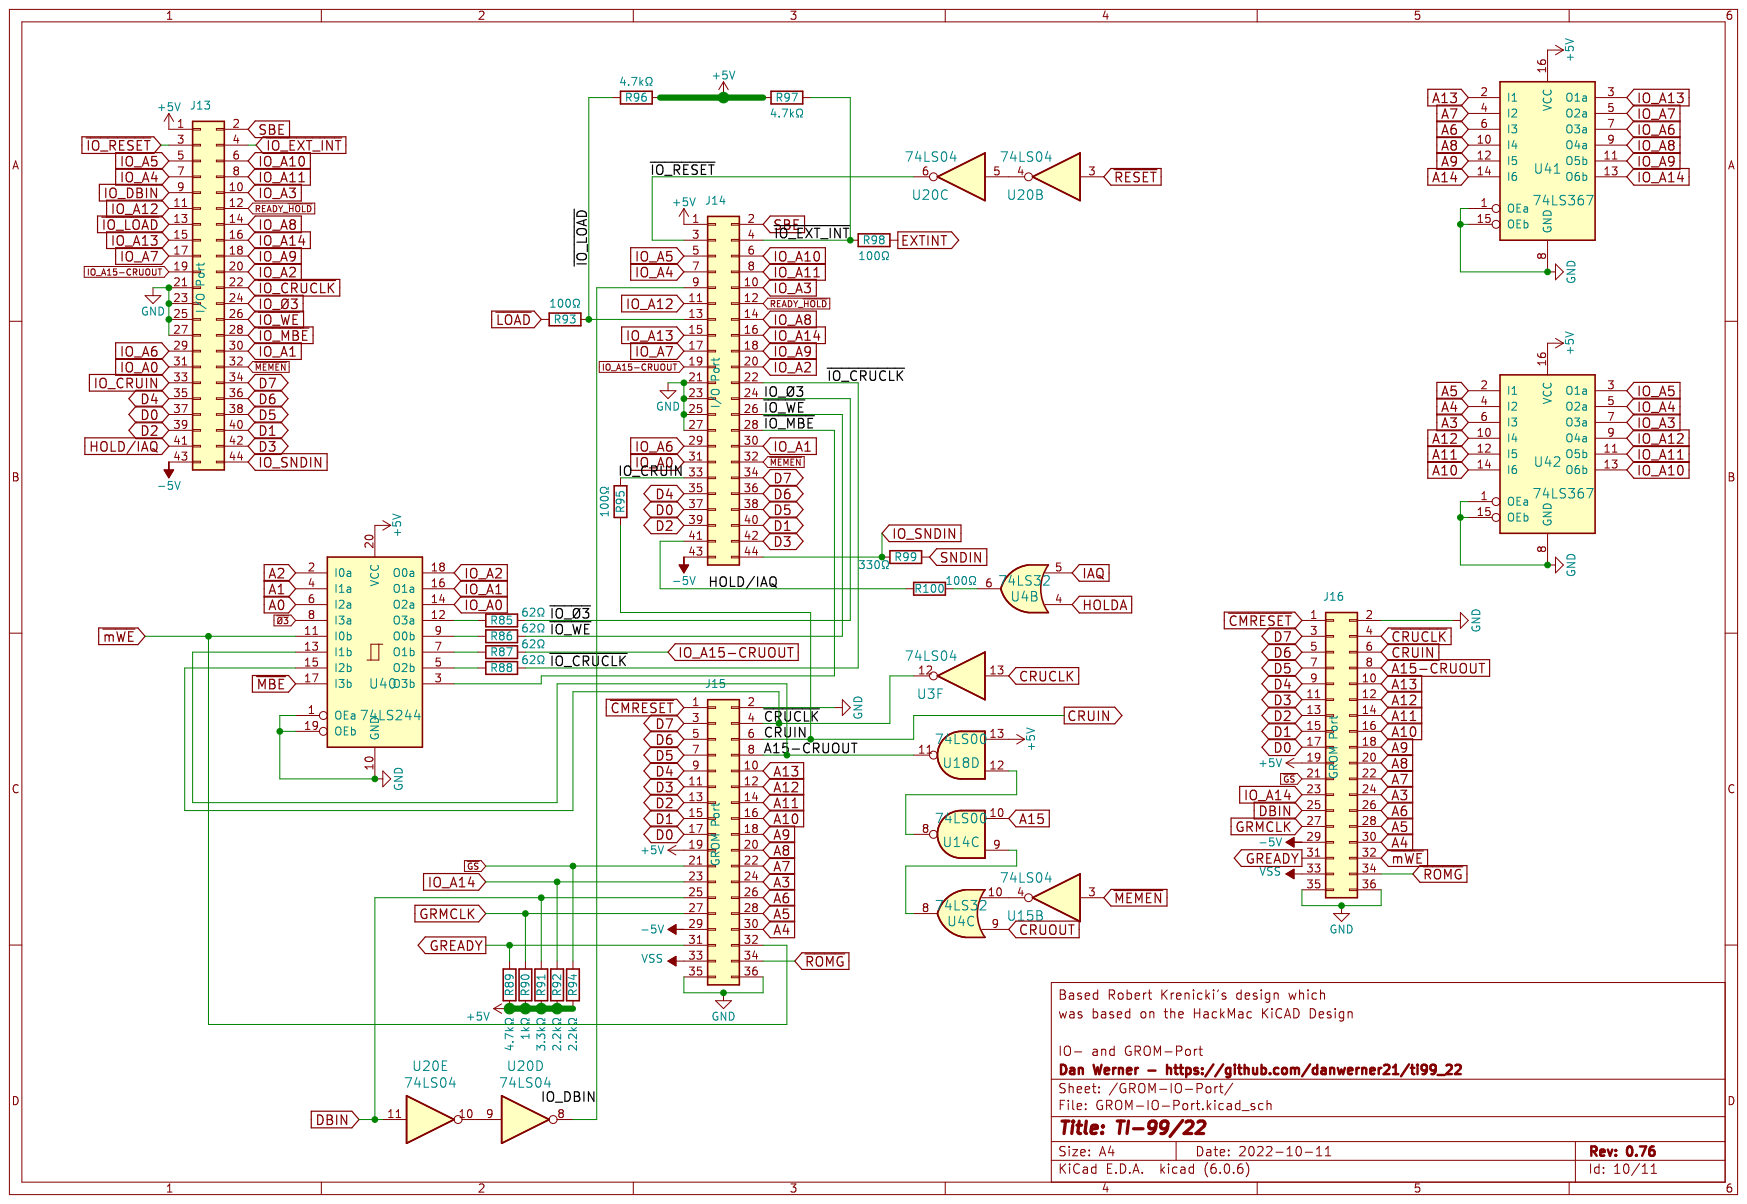
[picture p122: page 10]

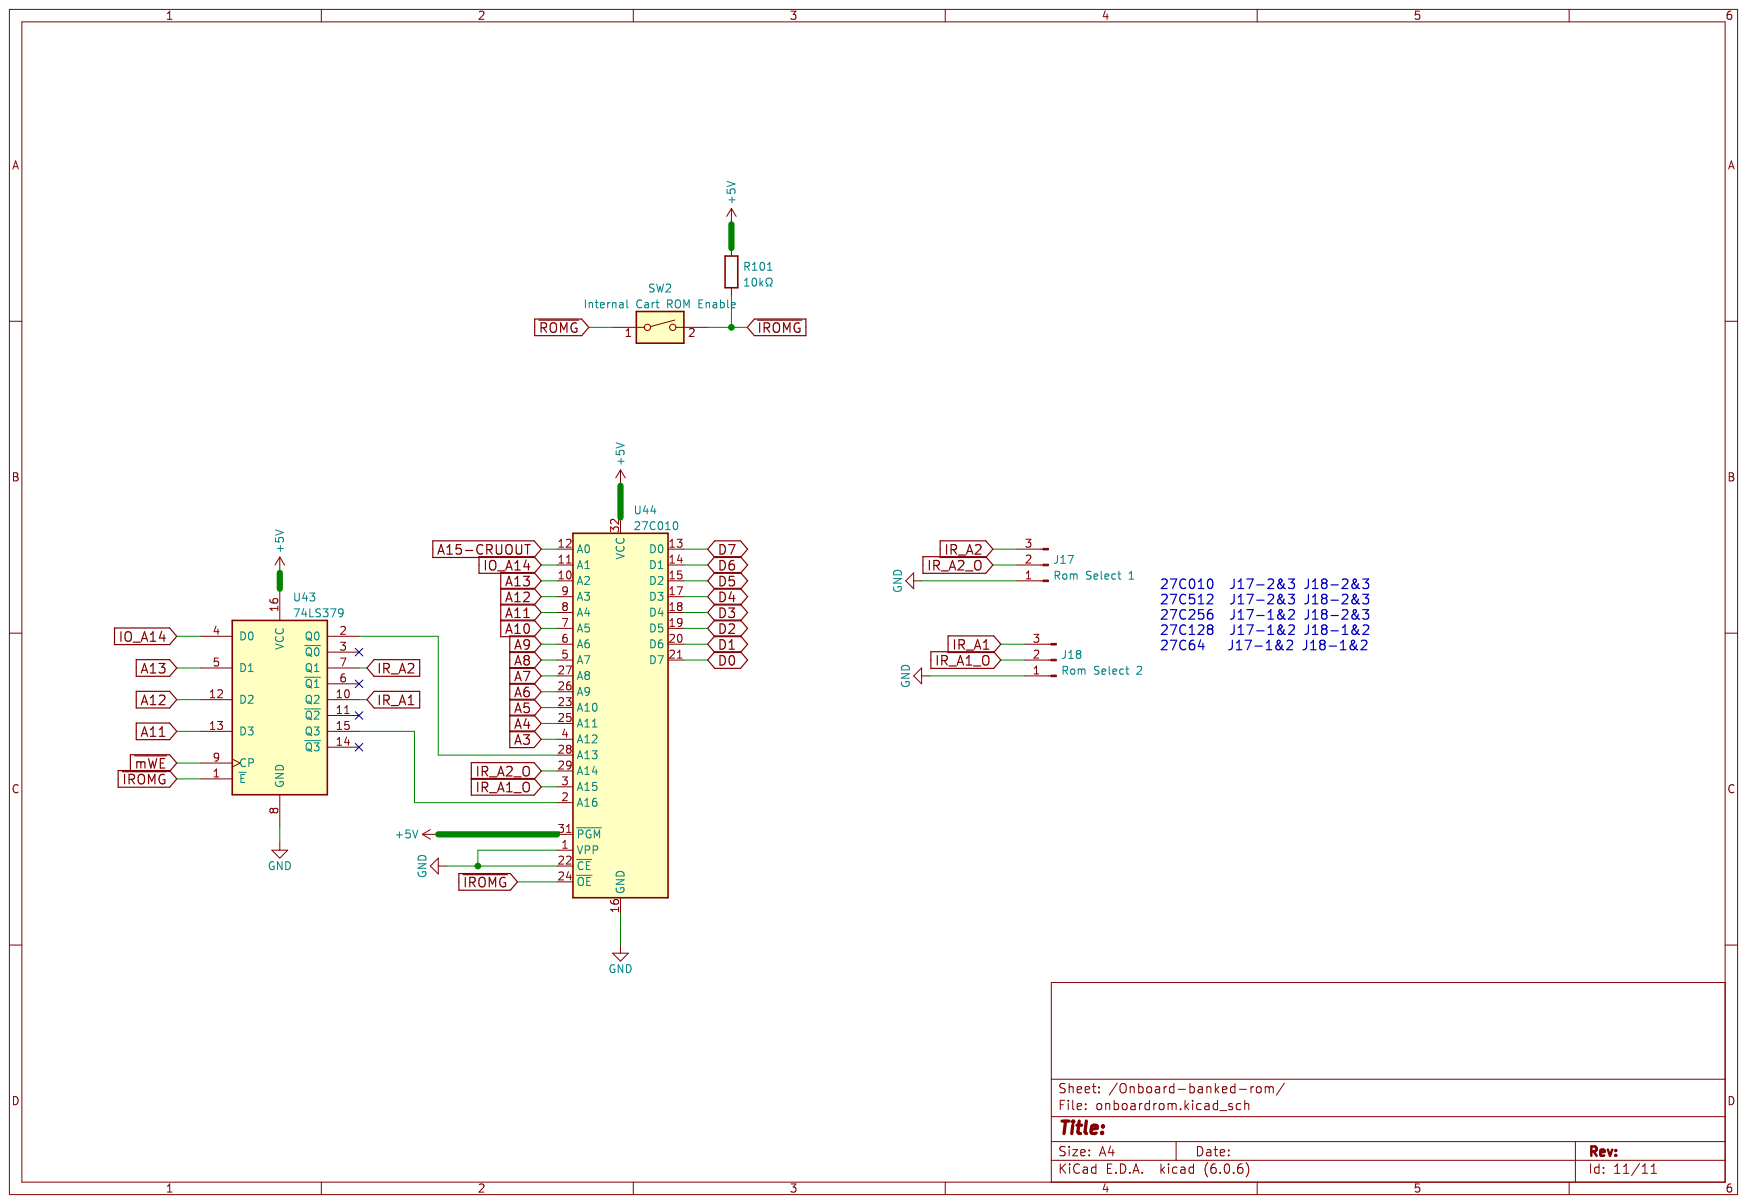
[picture p123: page 11]
