danwerner21/TI99_22/Keyboard/KeyboardV0.5.pdf

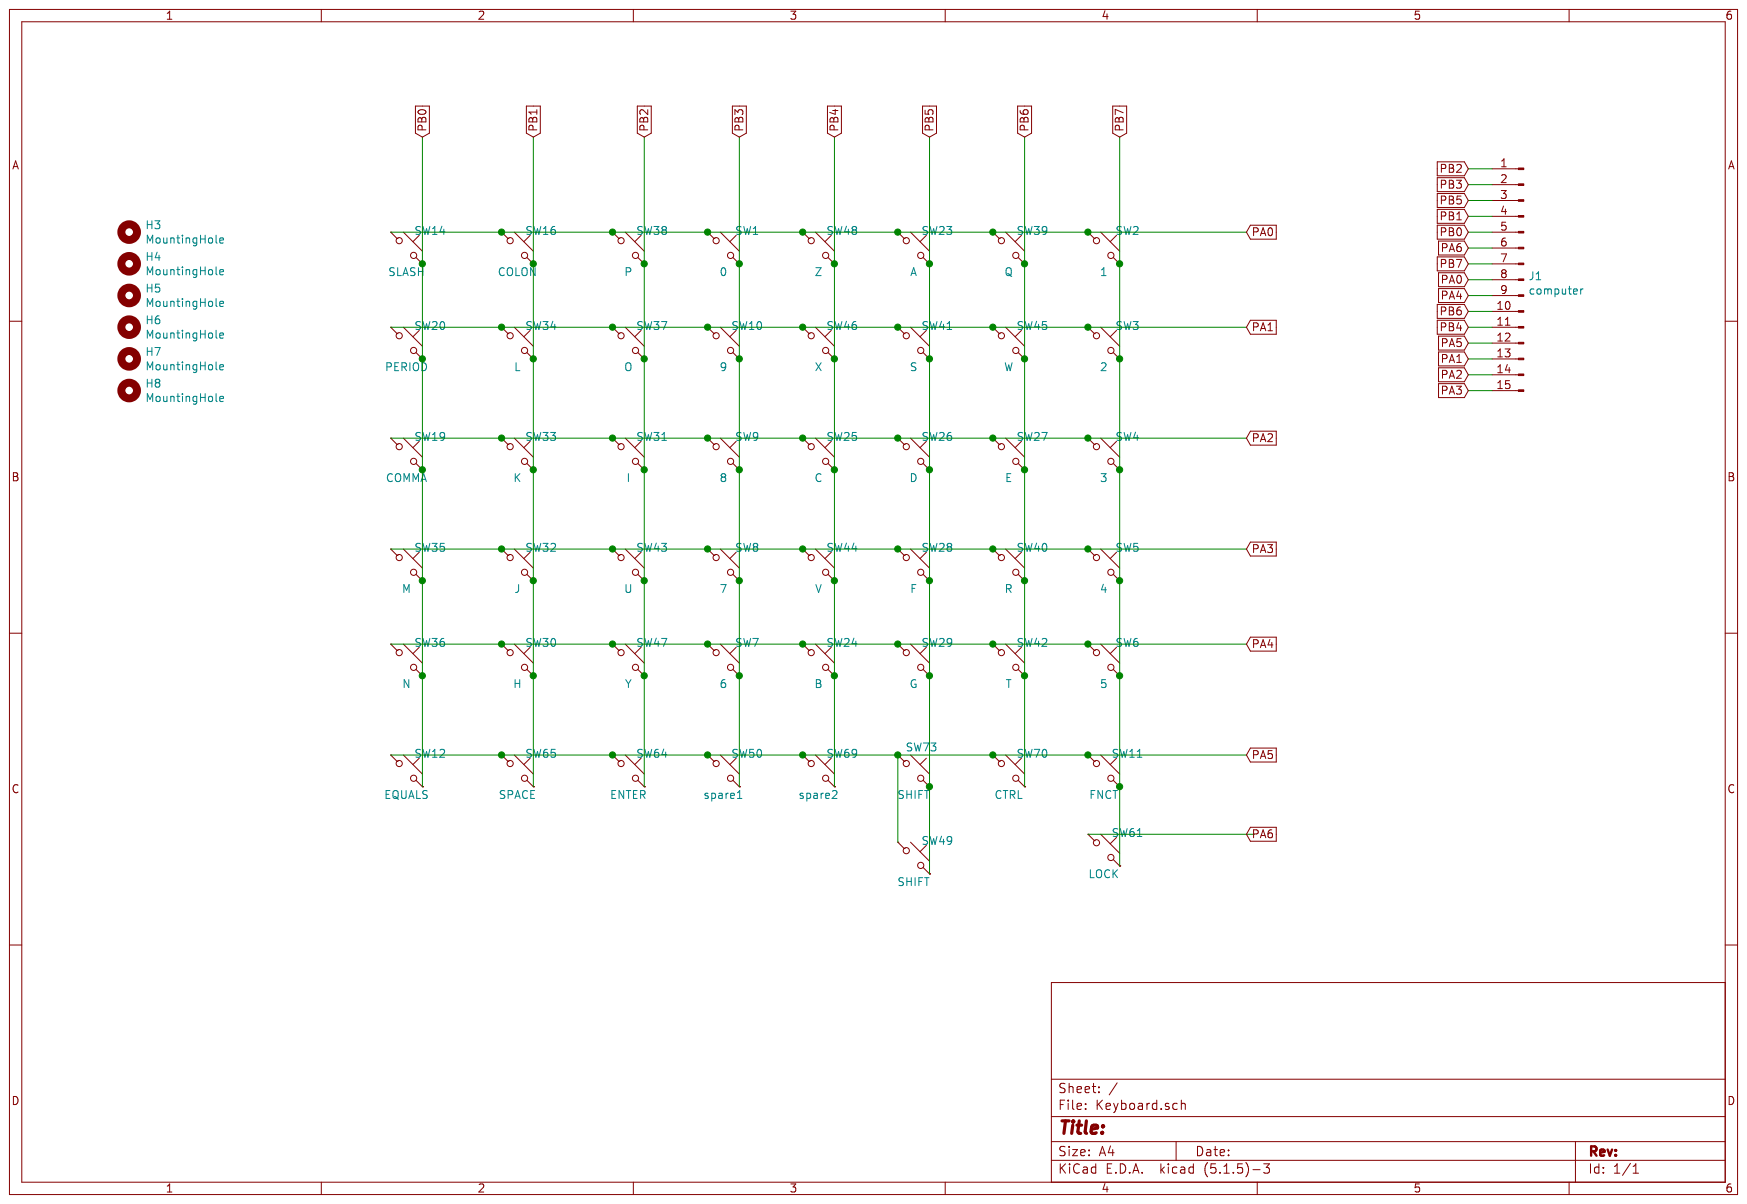
[picture p124: page 1]
