danwerner21/TI99_22/Keyboard/KeyboardV0.8.pdf

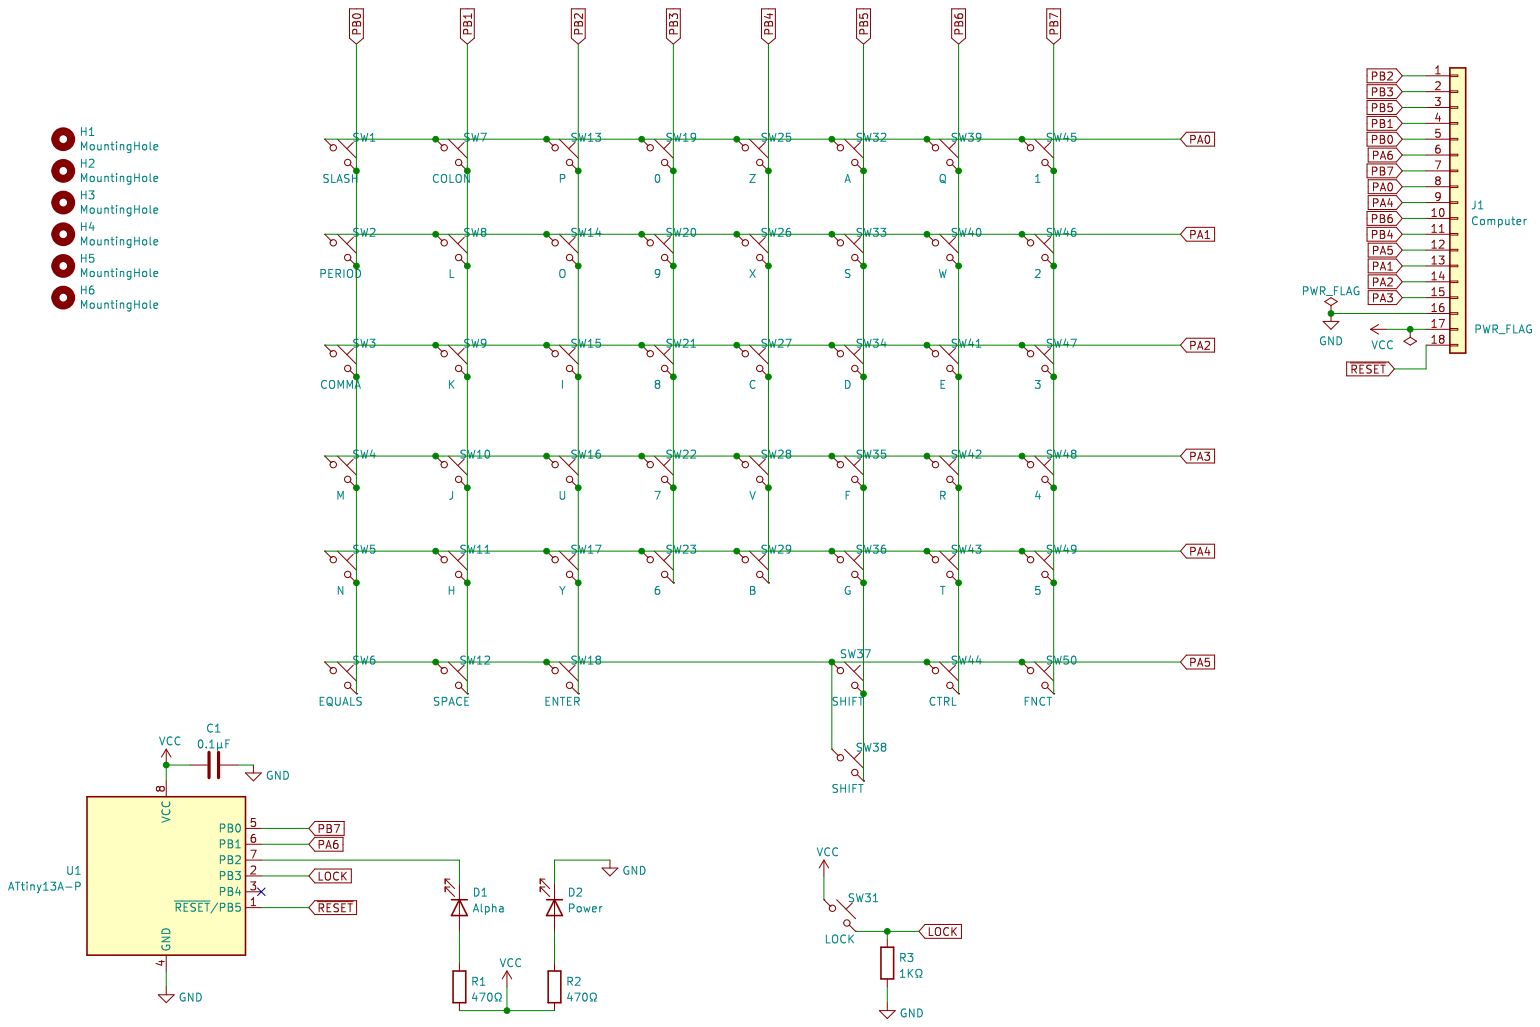
[picture p125: page 1]
