danwerner21/TI99_22/mainboard/mainboard_v0.76.pdf

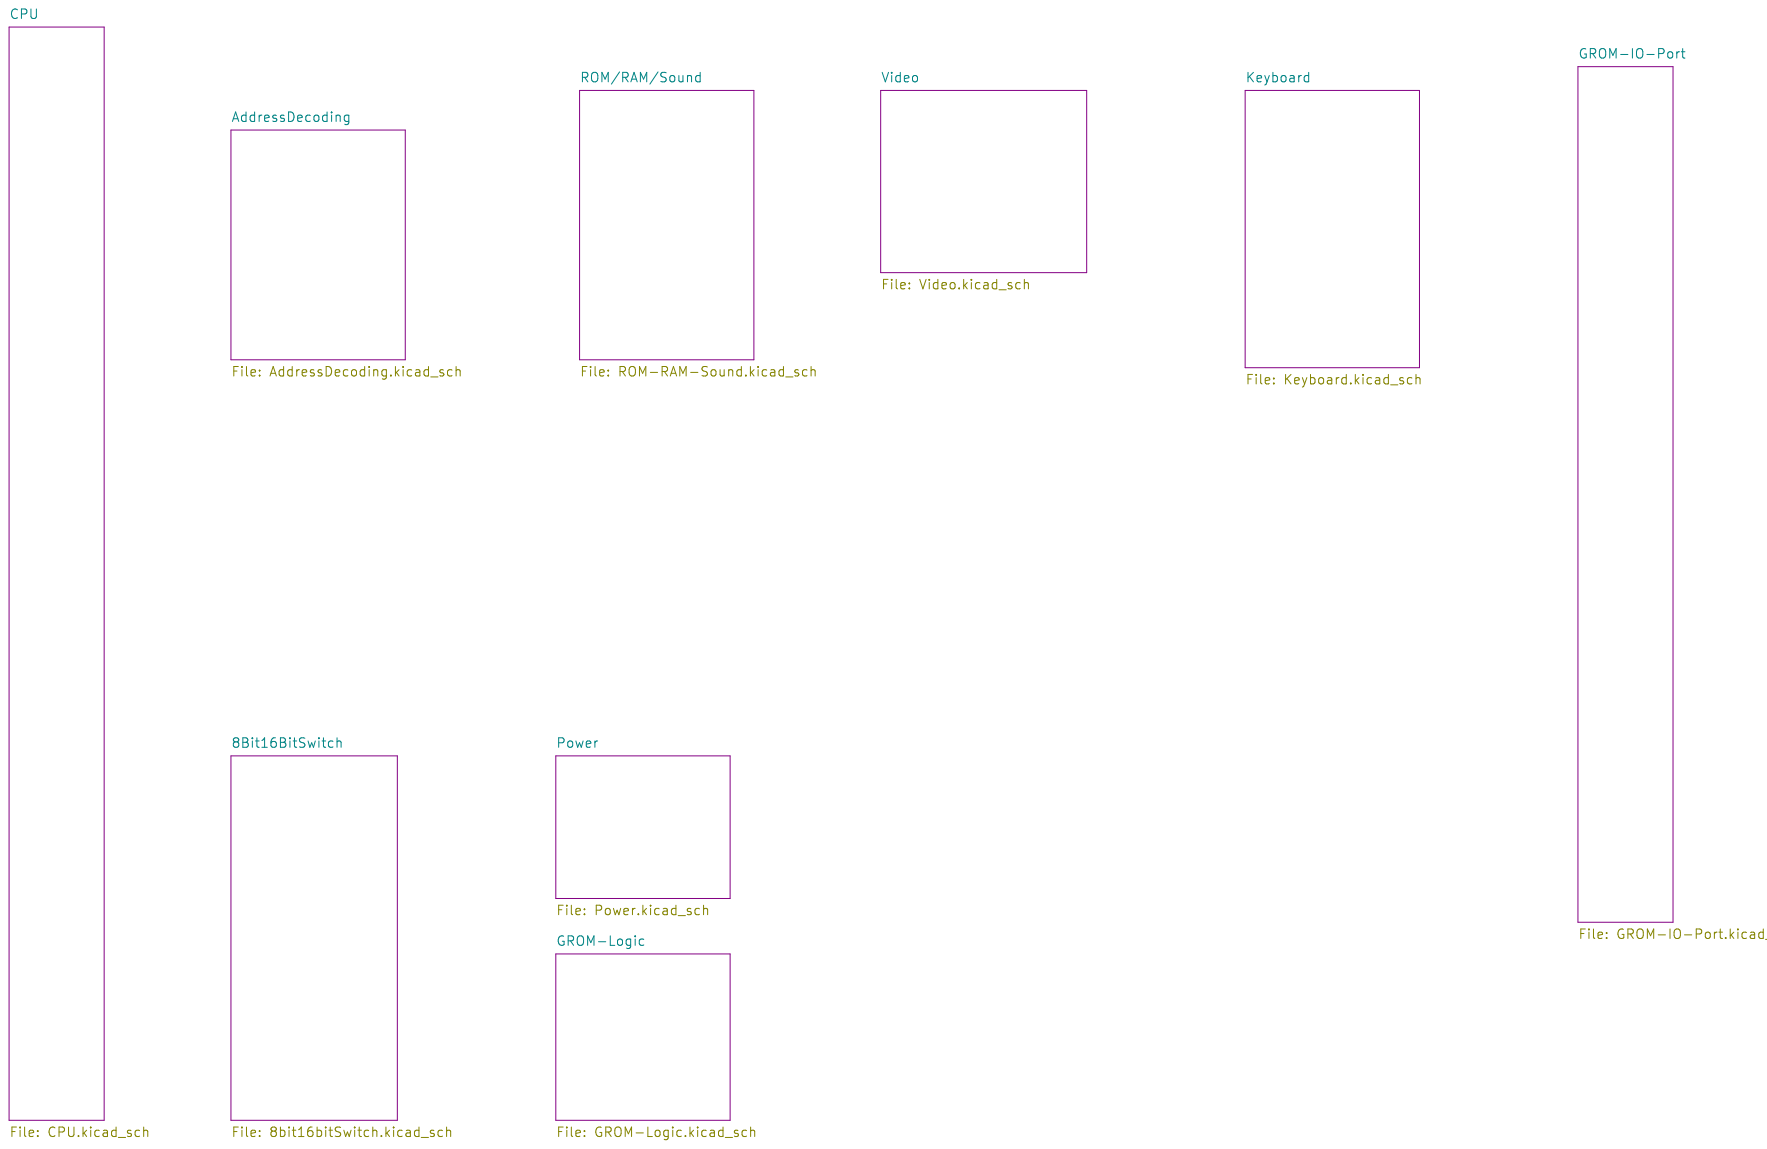
[picture p126: page 1]

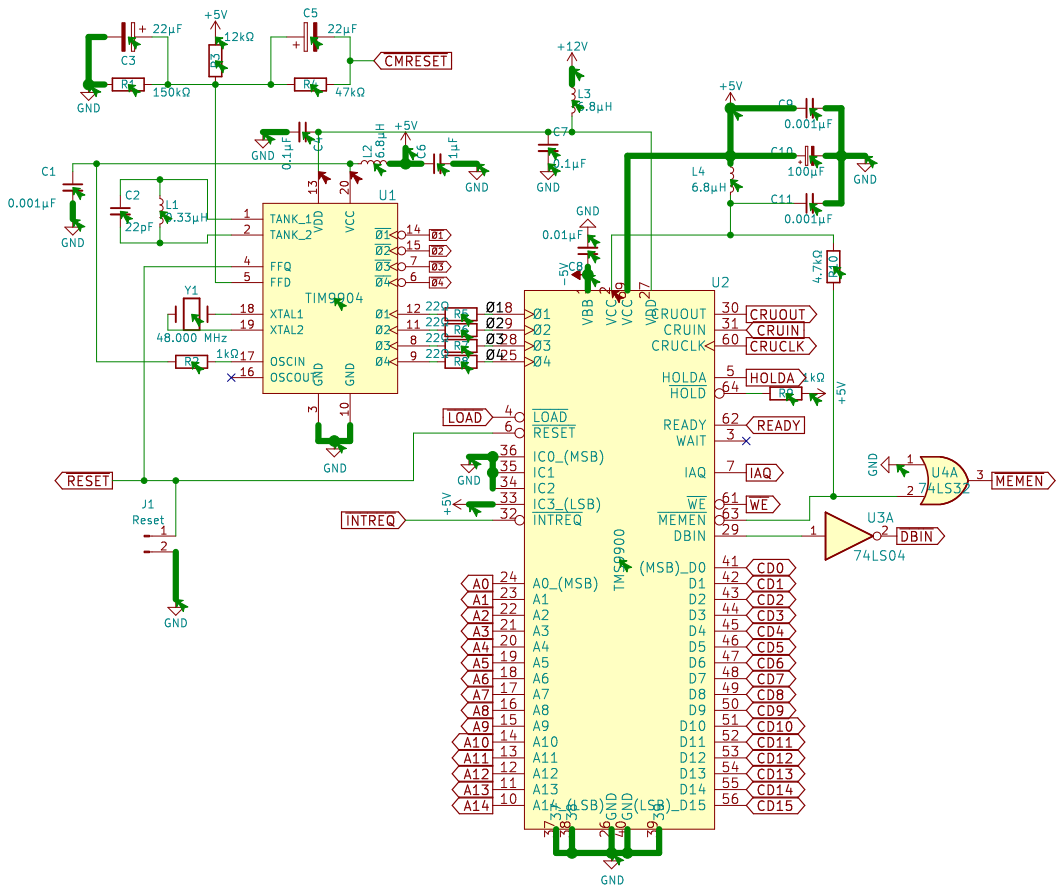
[picture p127: page 2]

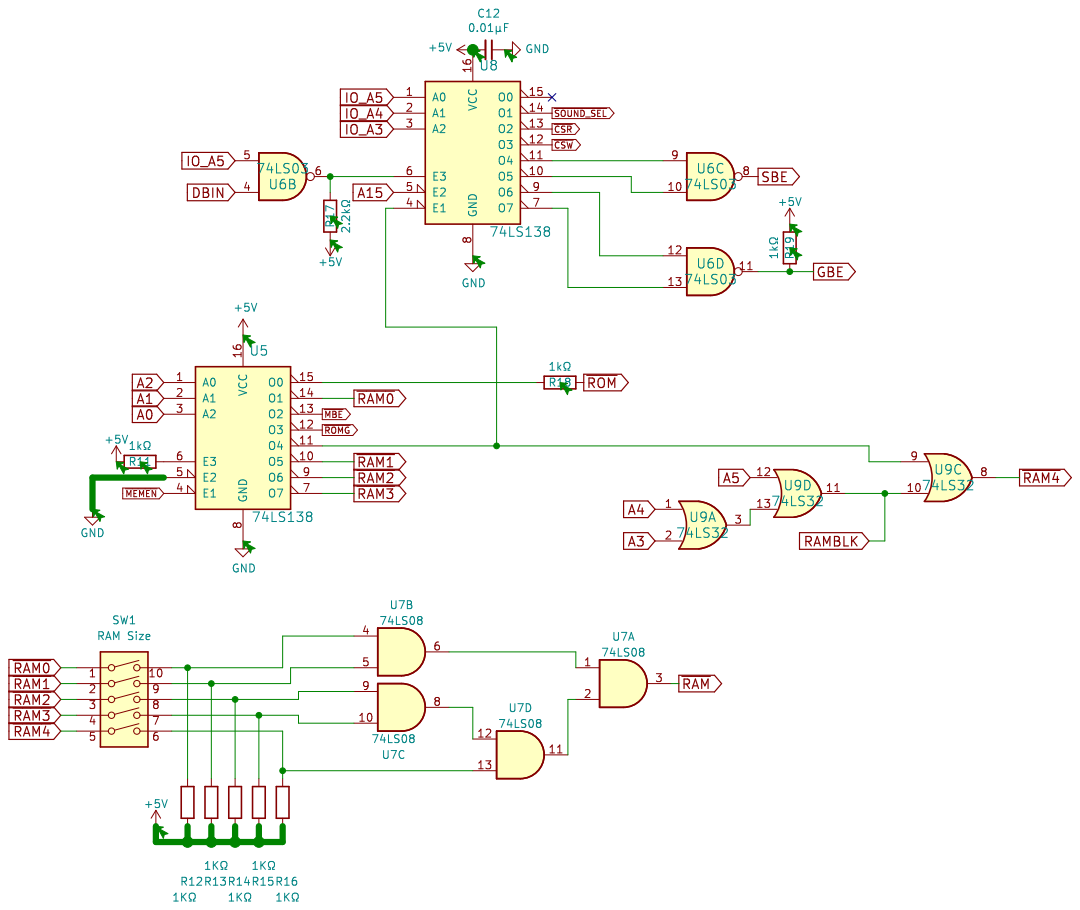
[picture p128: page 3]

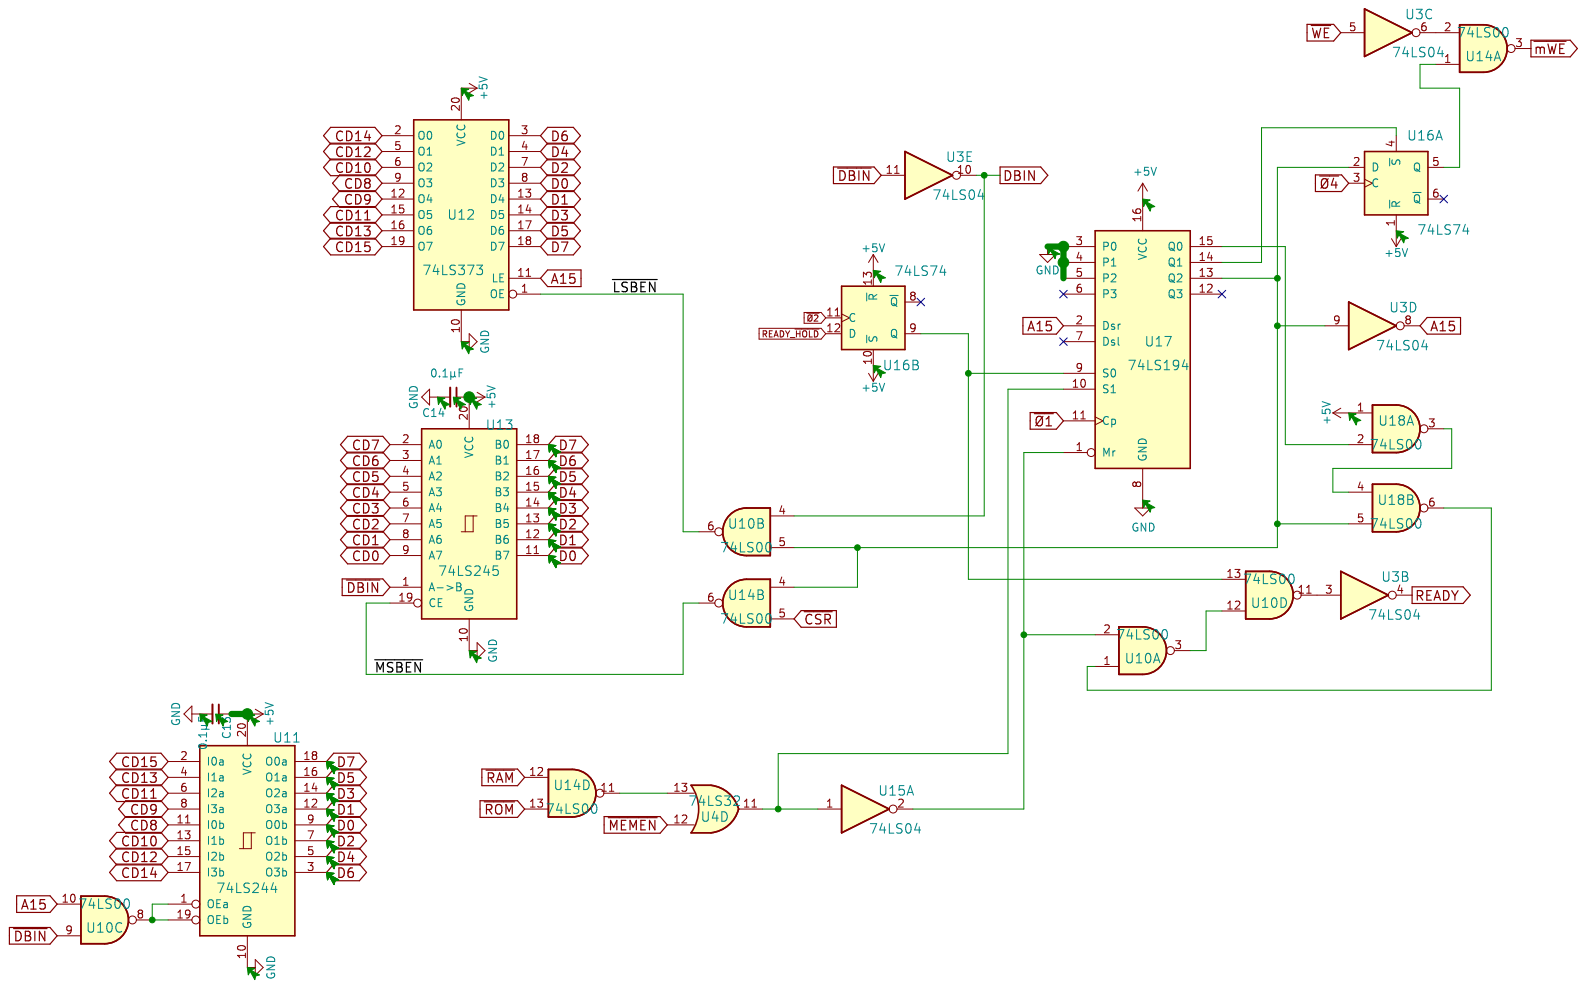
[picture p129: page 4]

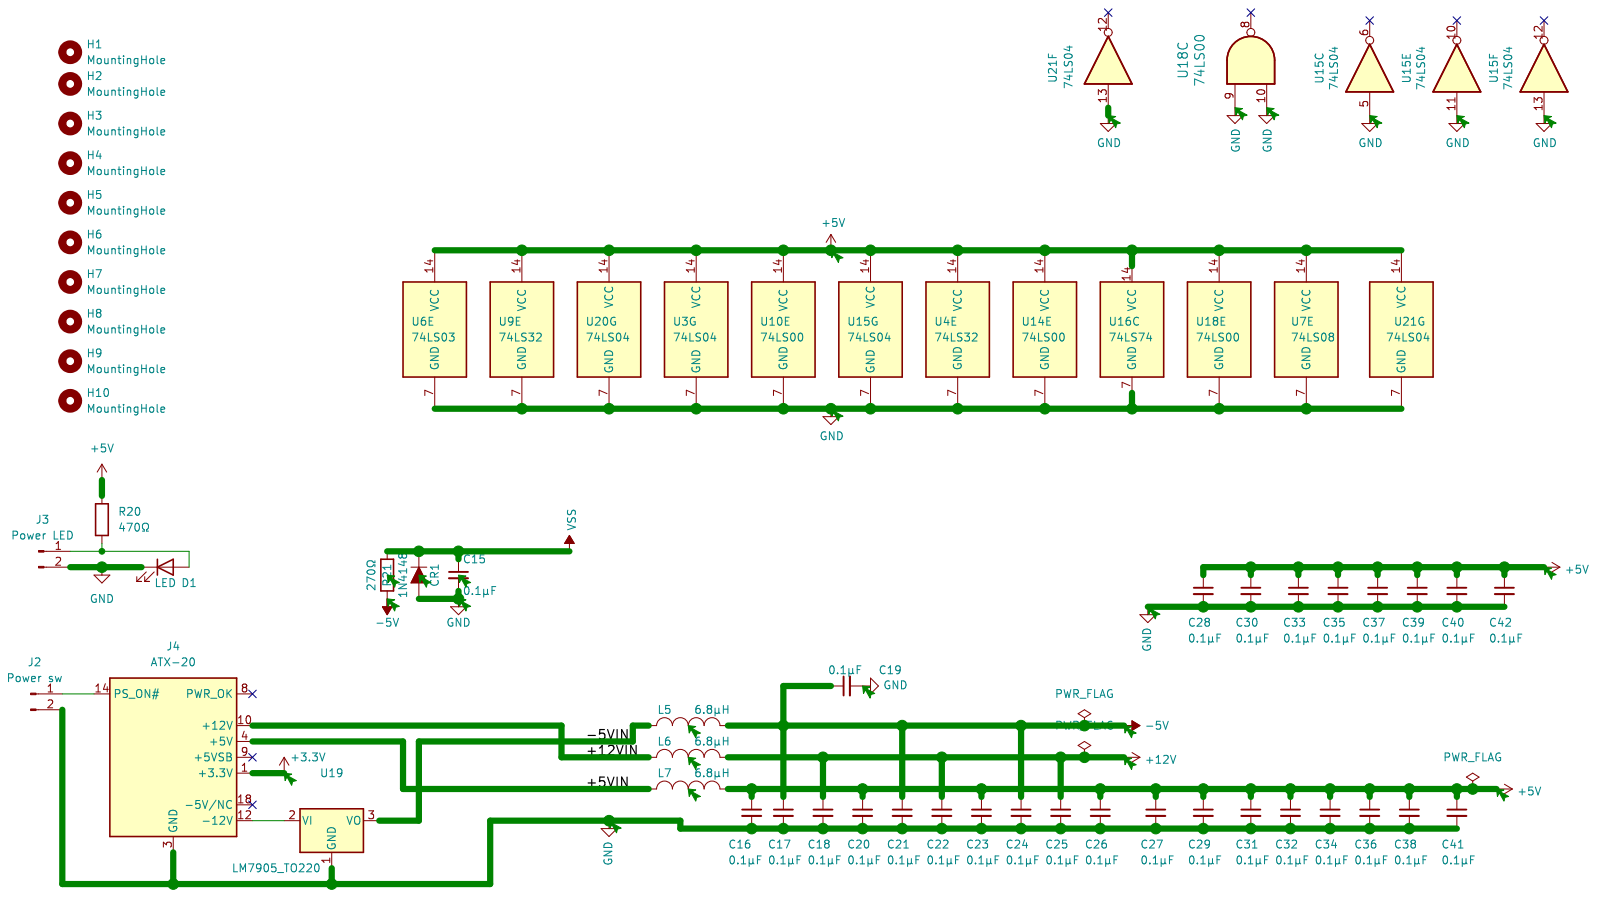
[picture p130: page 5]

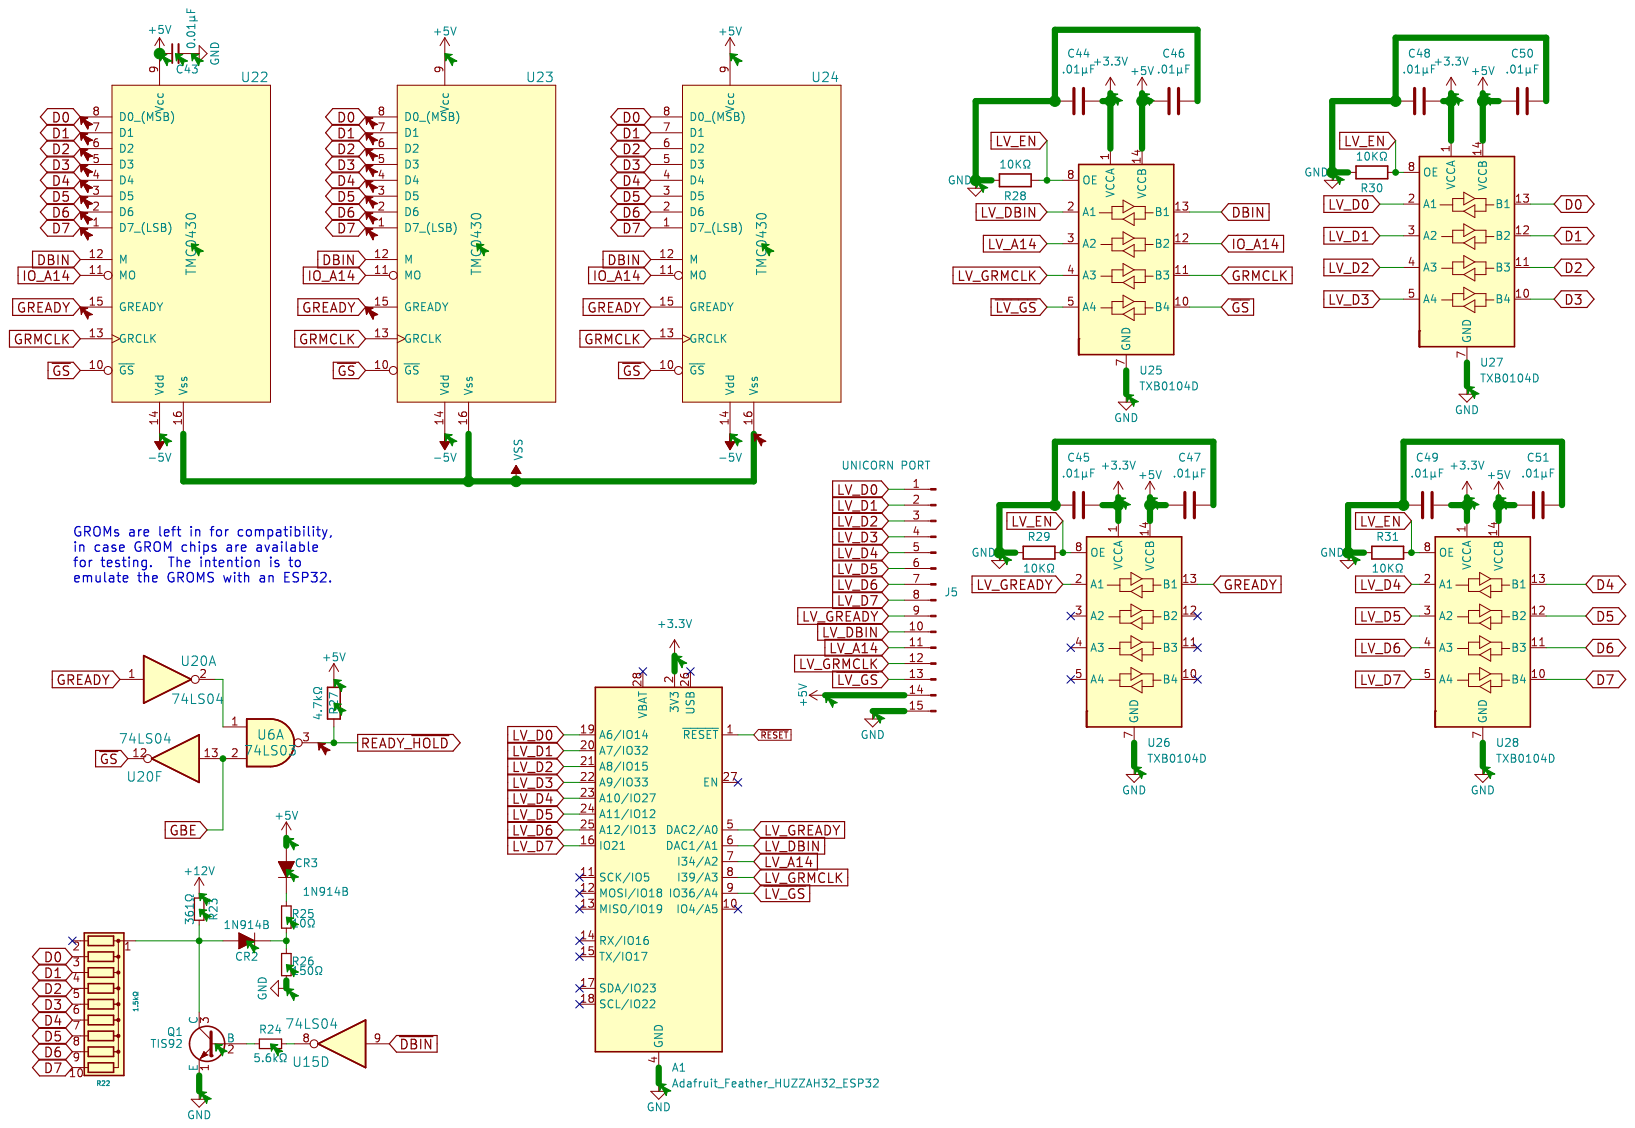
[picture p131: page 6]

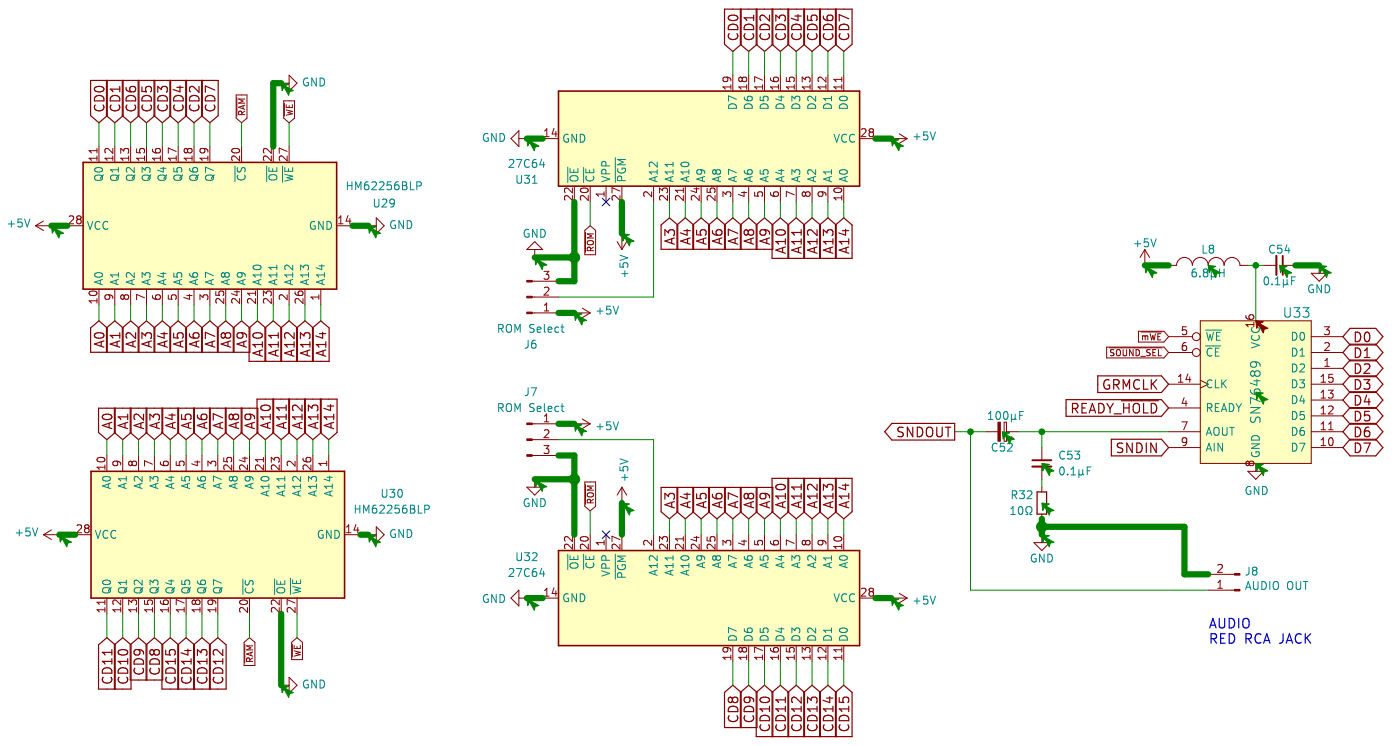
[picture p132: page 7]

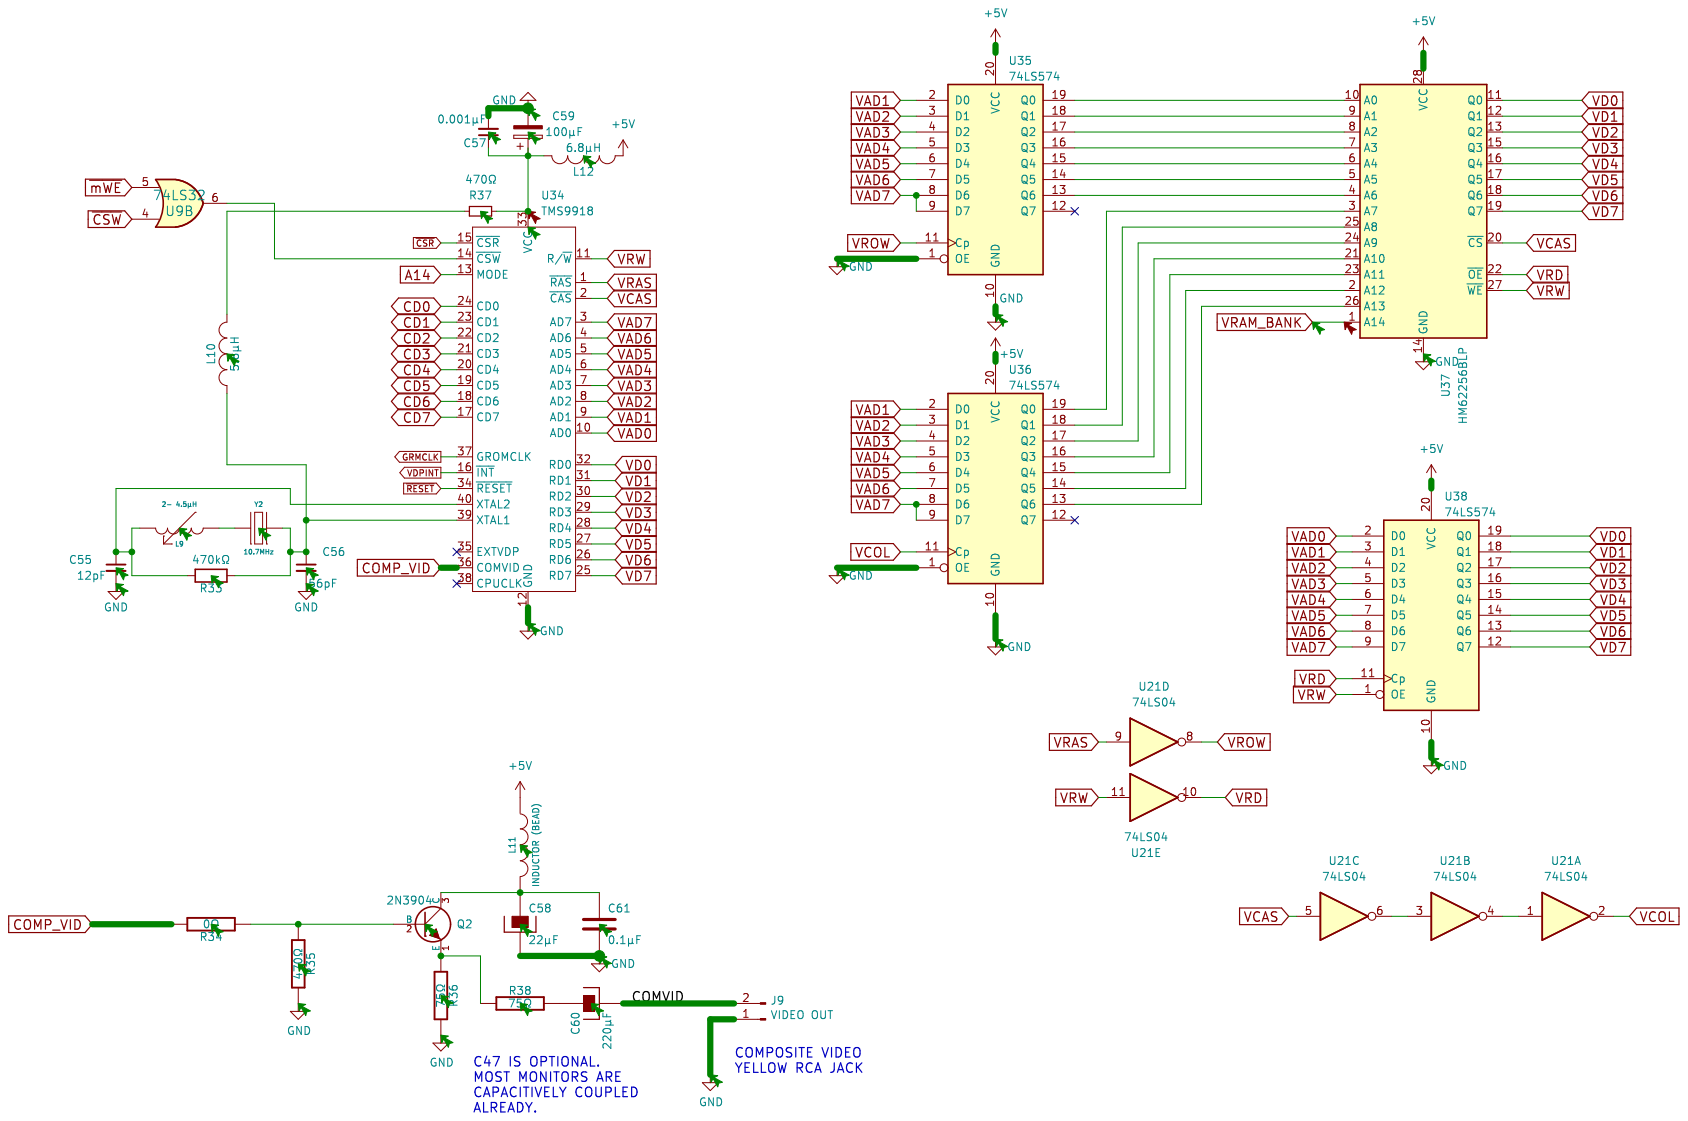
[picture p133: page 8]

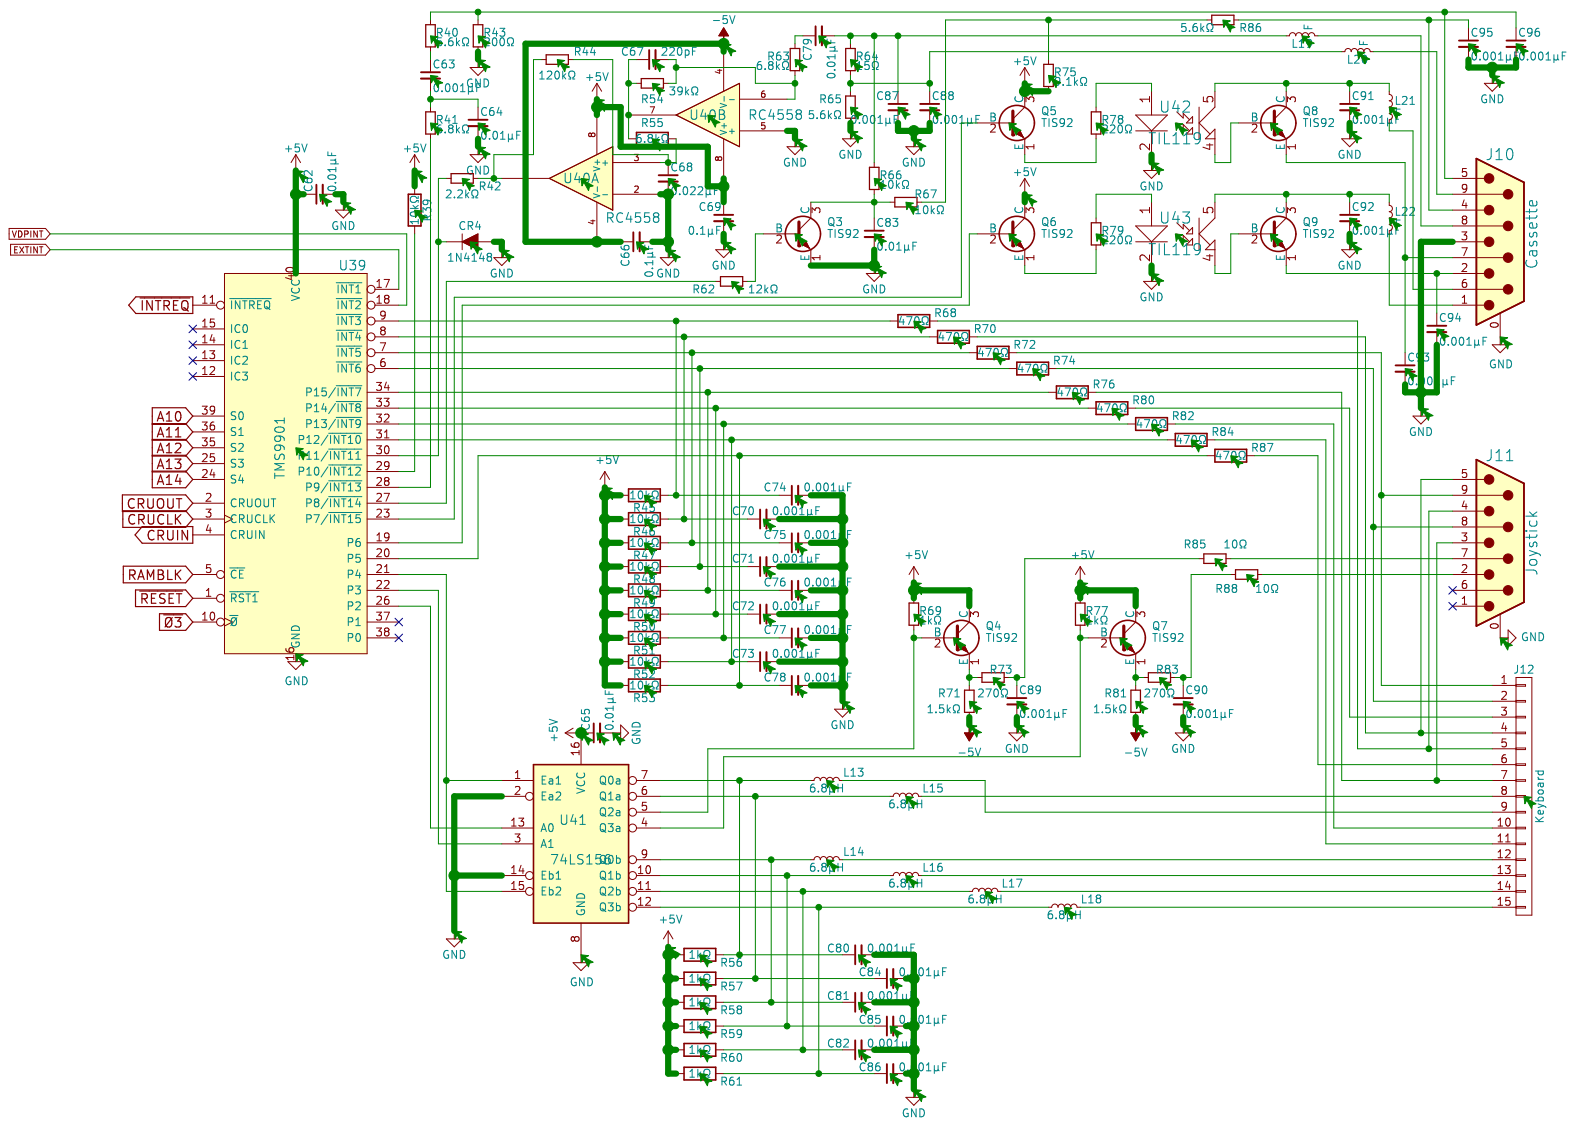
[picture p134: page 9]

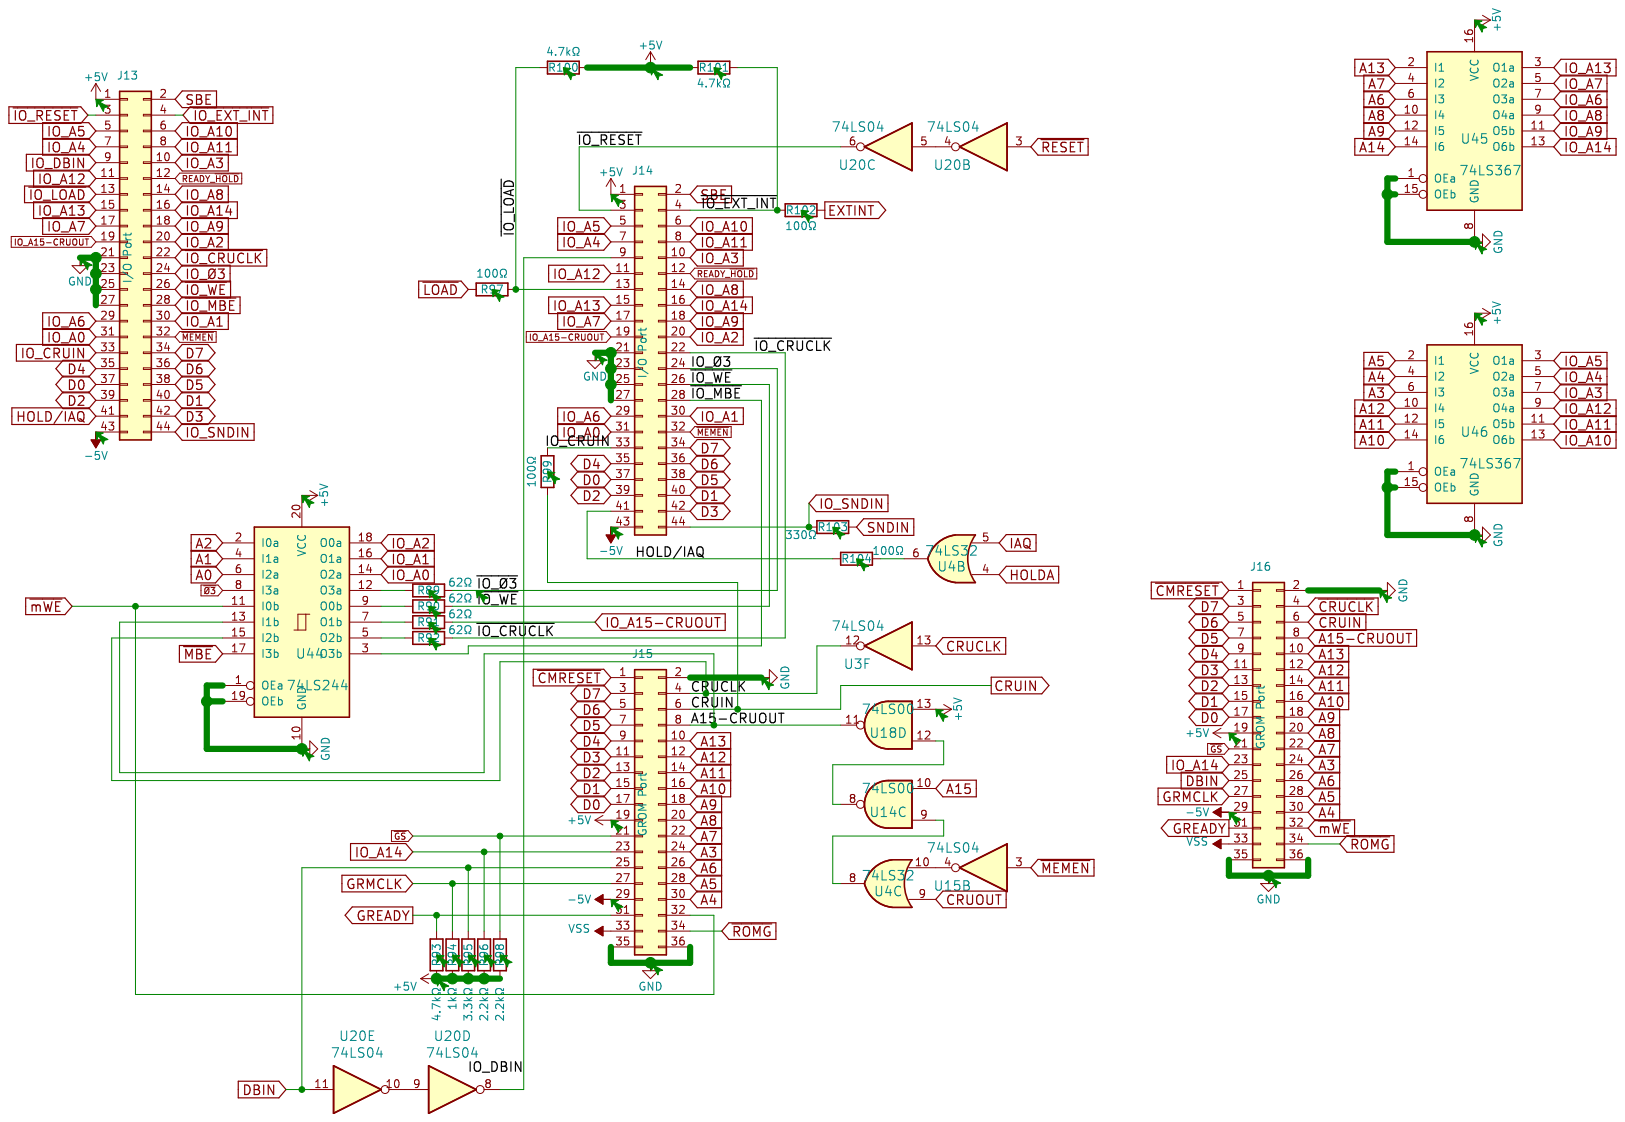
[picture p135: page 10]
