danwerner21/TI99_22/mainboard/mainboard_pcb_V0.75.pdf

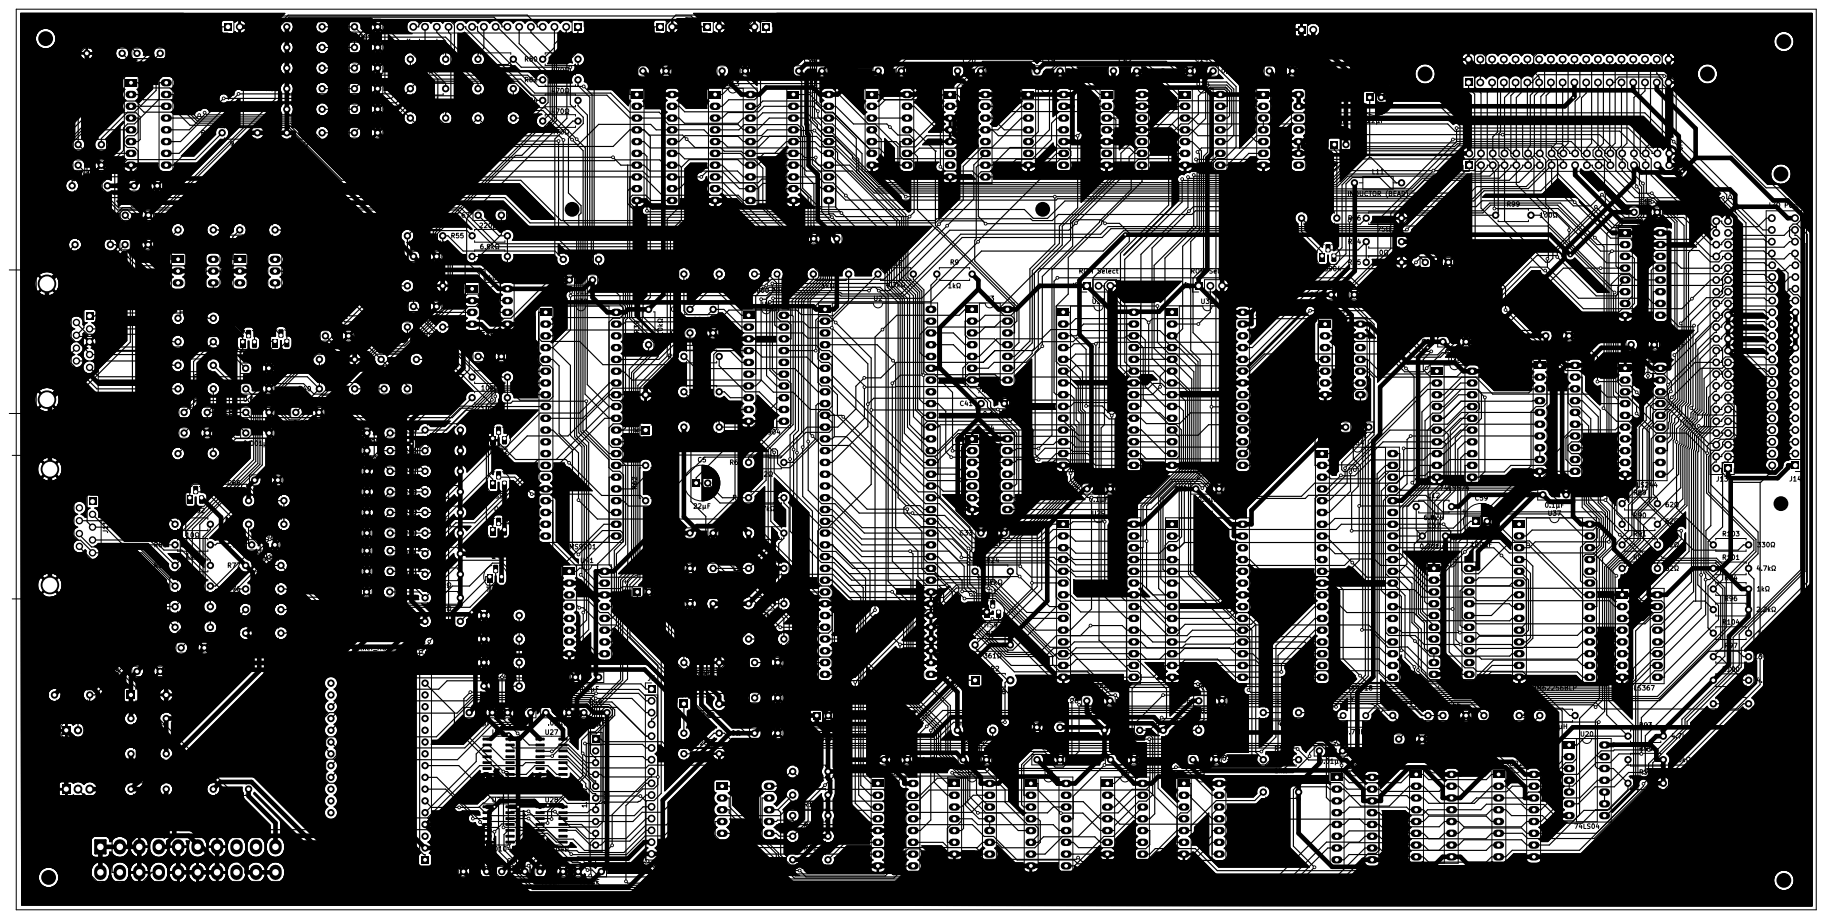
[picture p136: page 1]
