danwerner21/TI99_22/mainboard/mainboard_v0.75.pdf

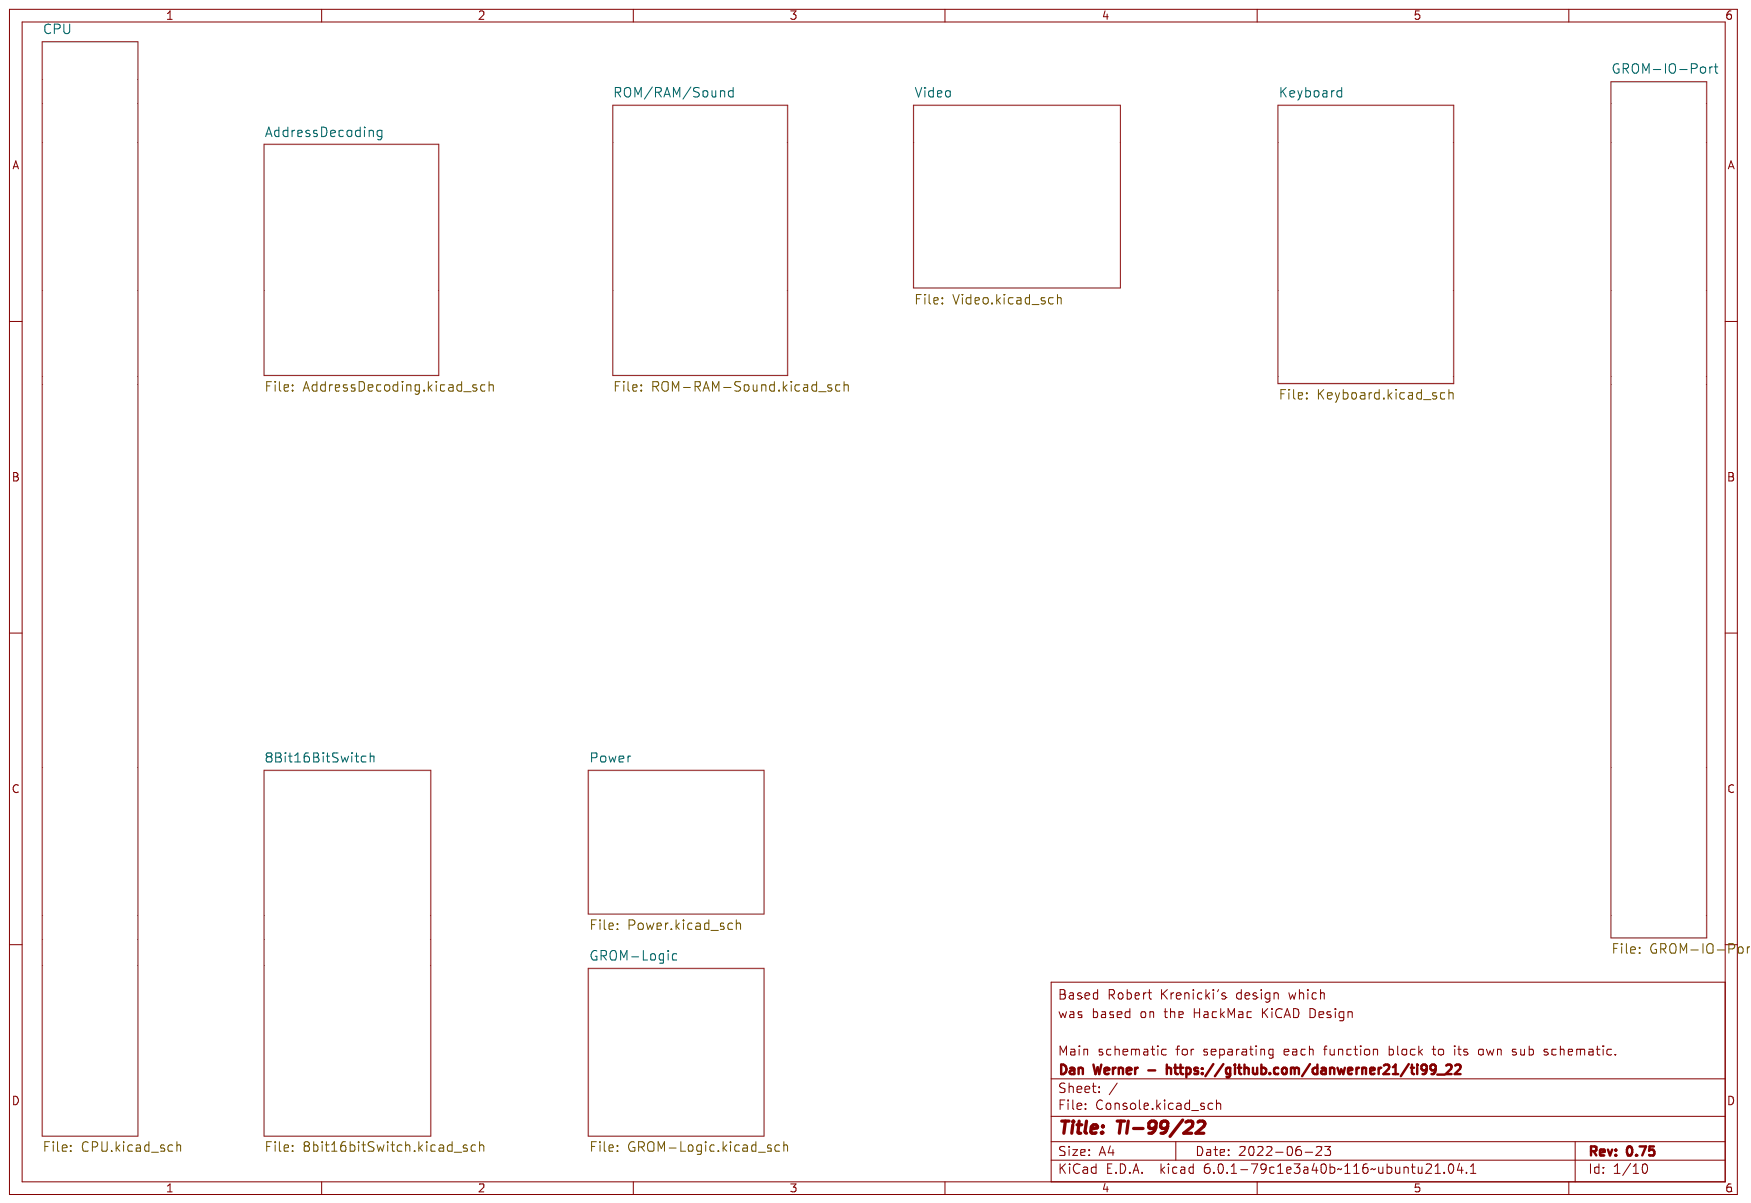
[picture p137: page 1]

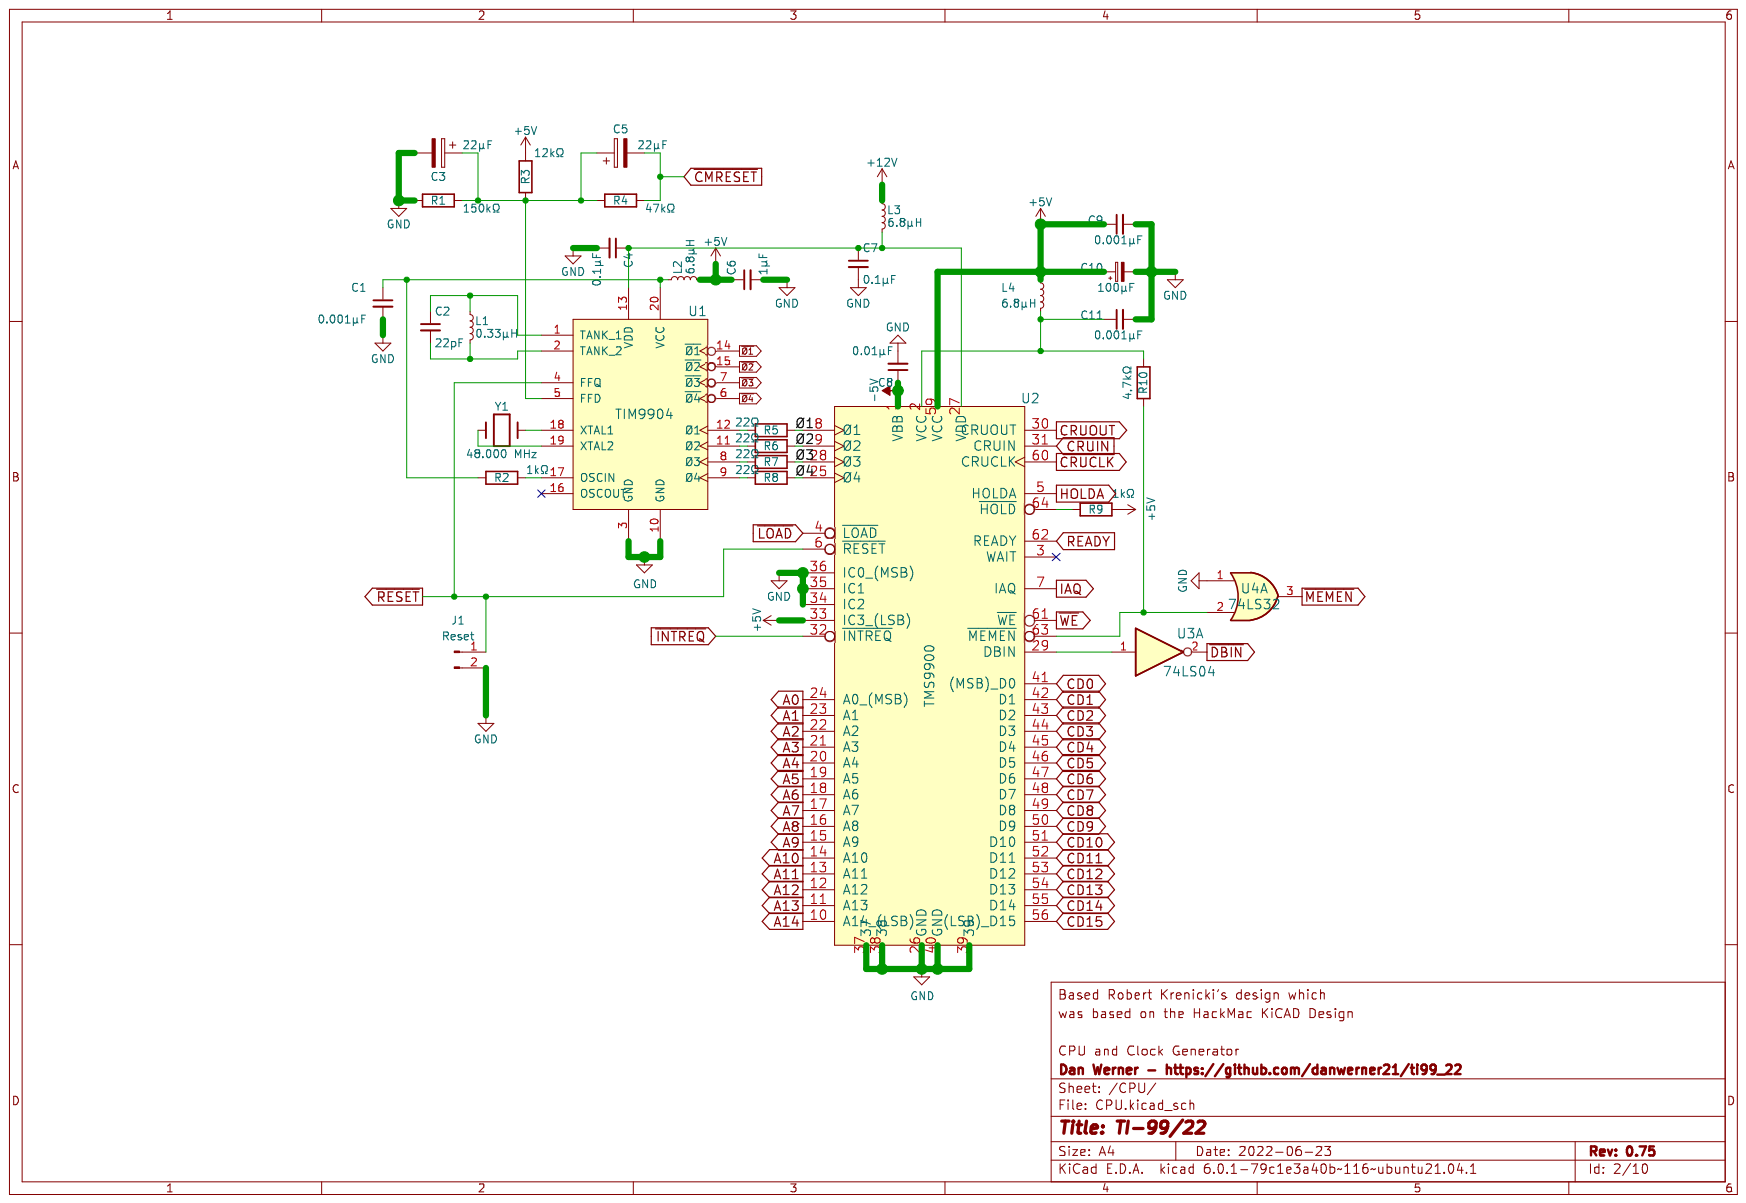
[picture p138: page 2]

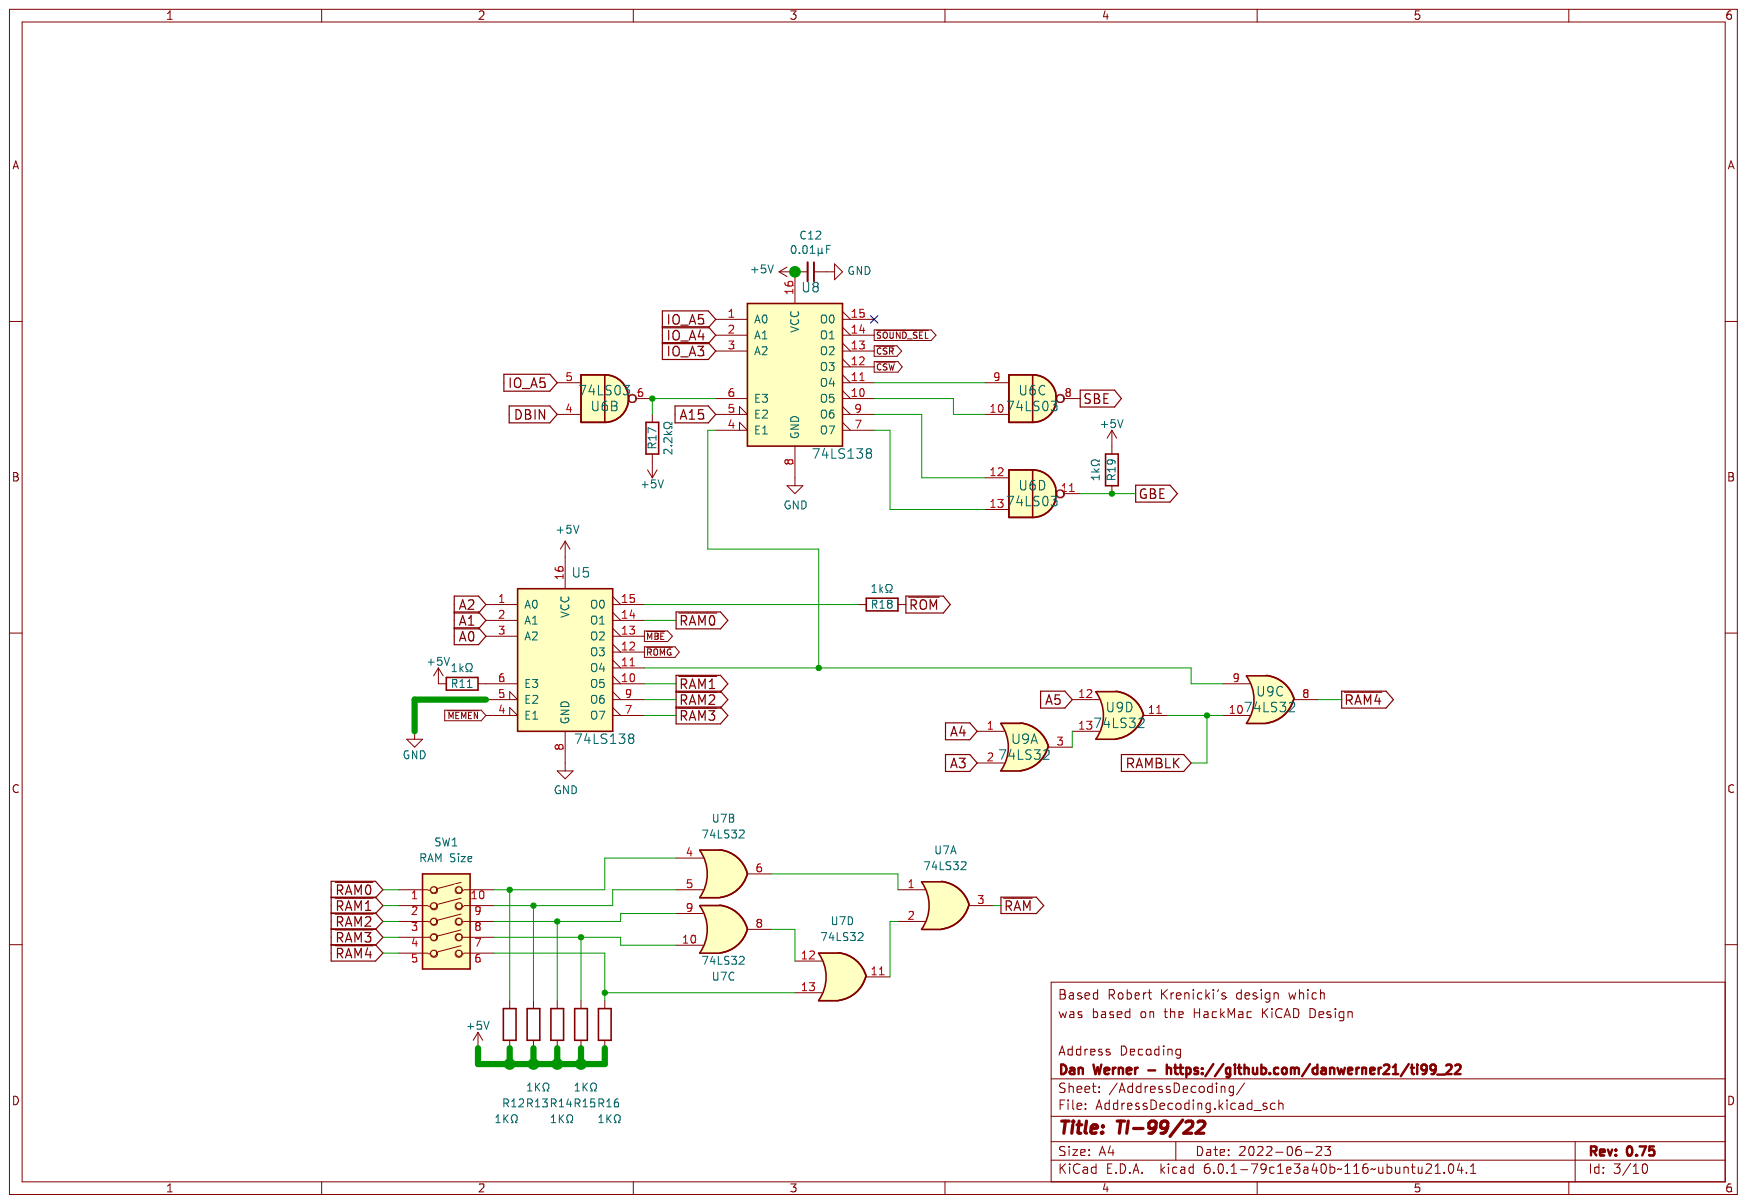
[picture p139: page 3]

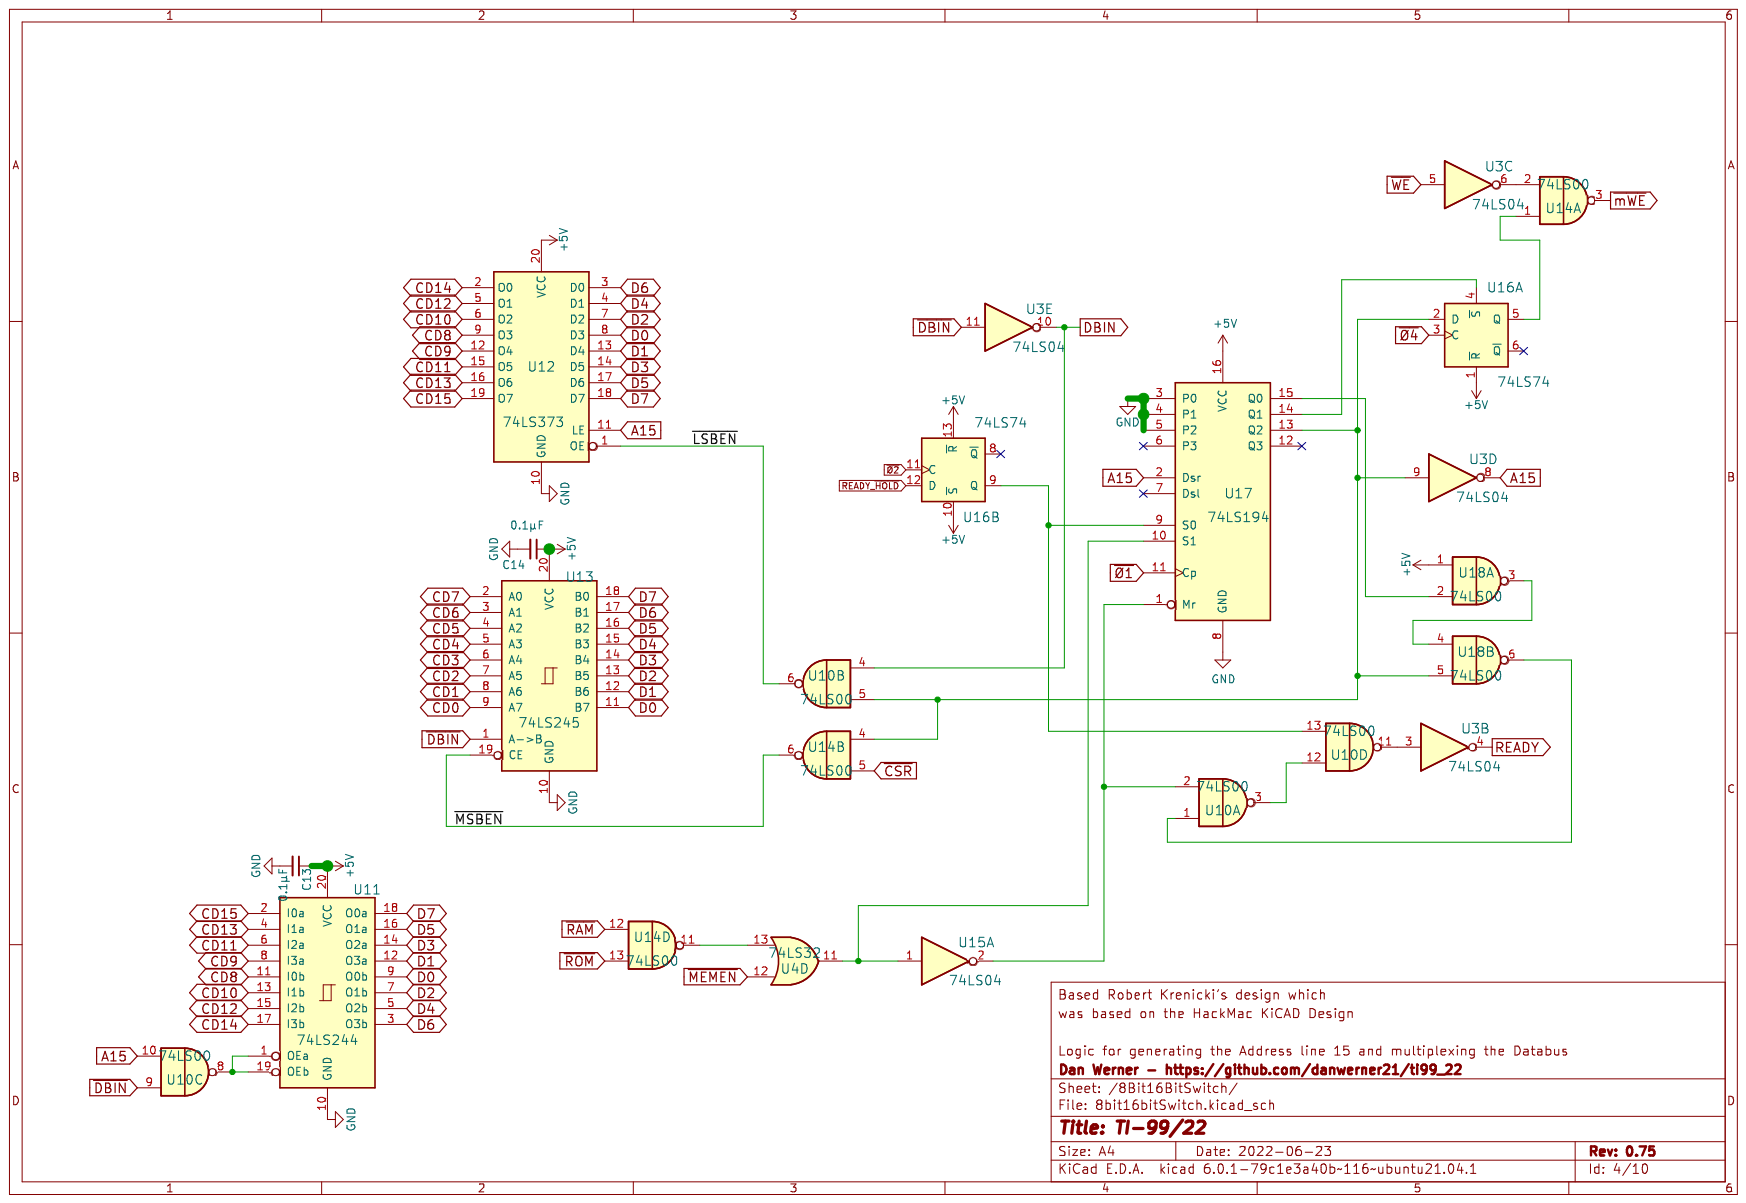
[picture p140: page 4]

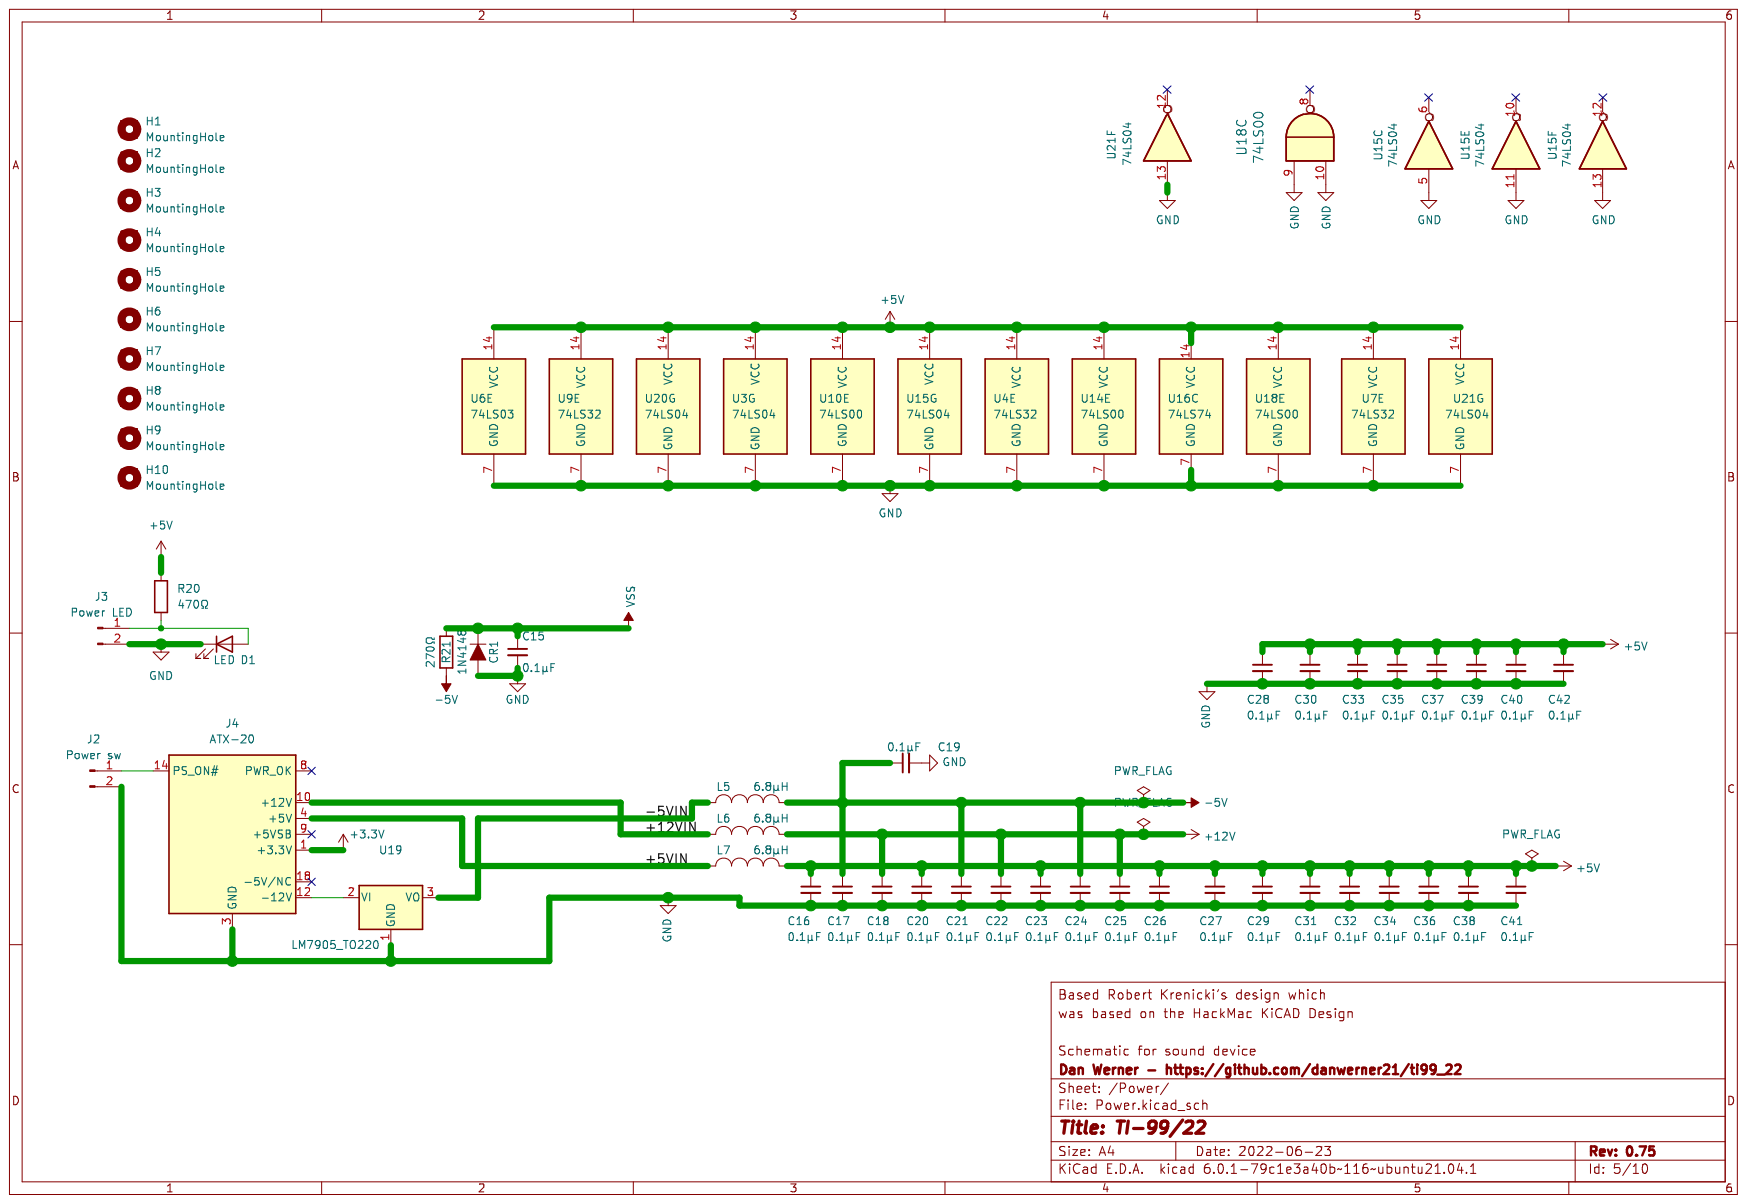
[picture p141: page 5]

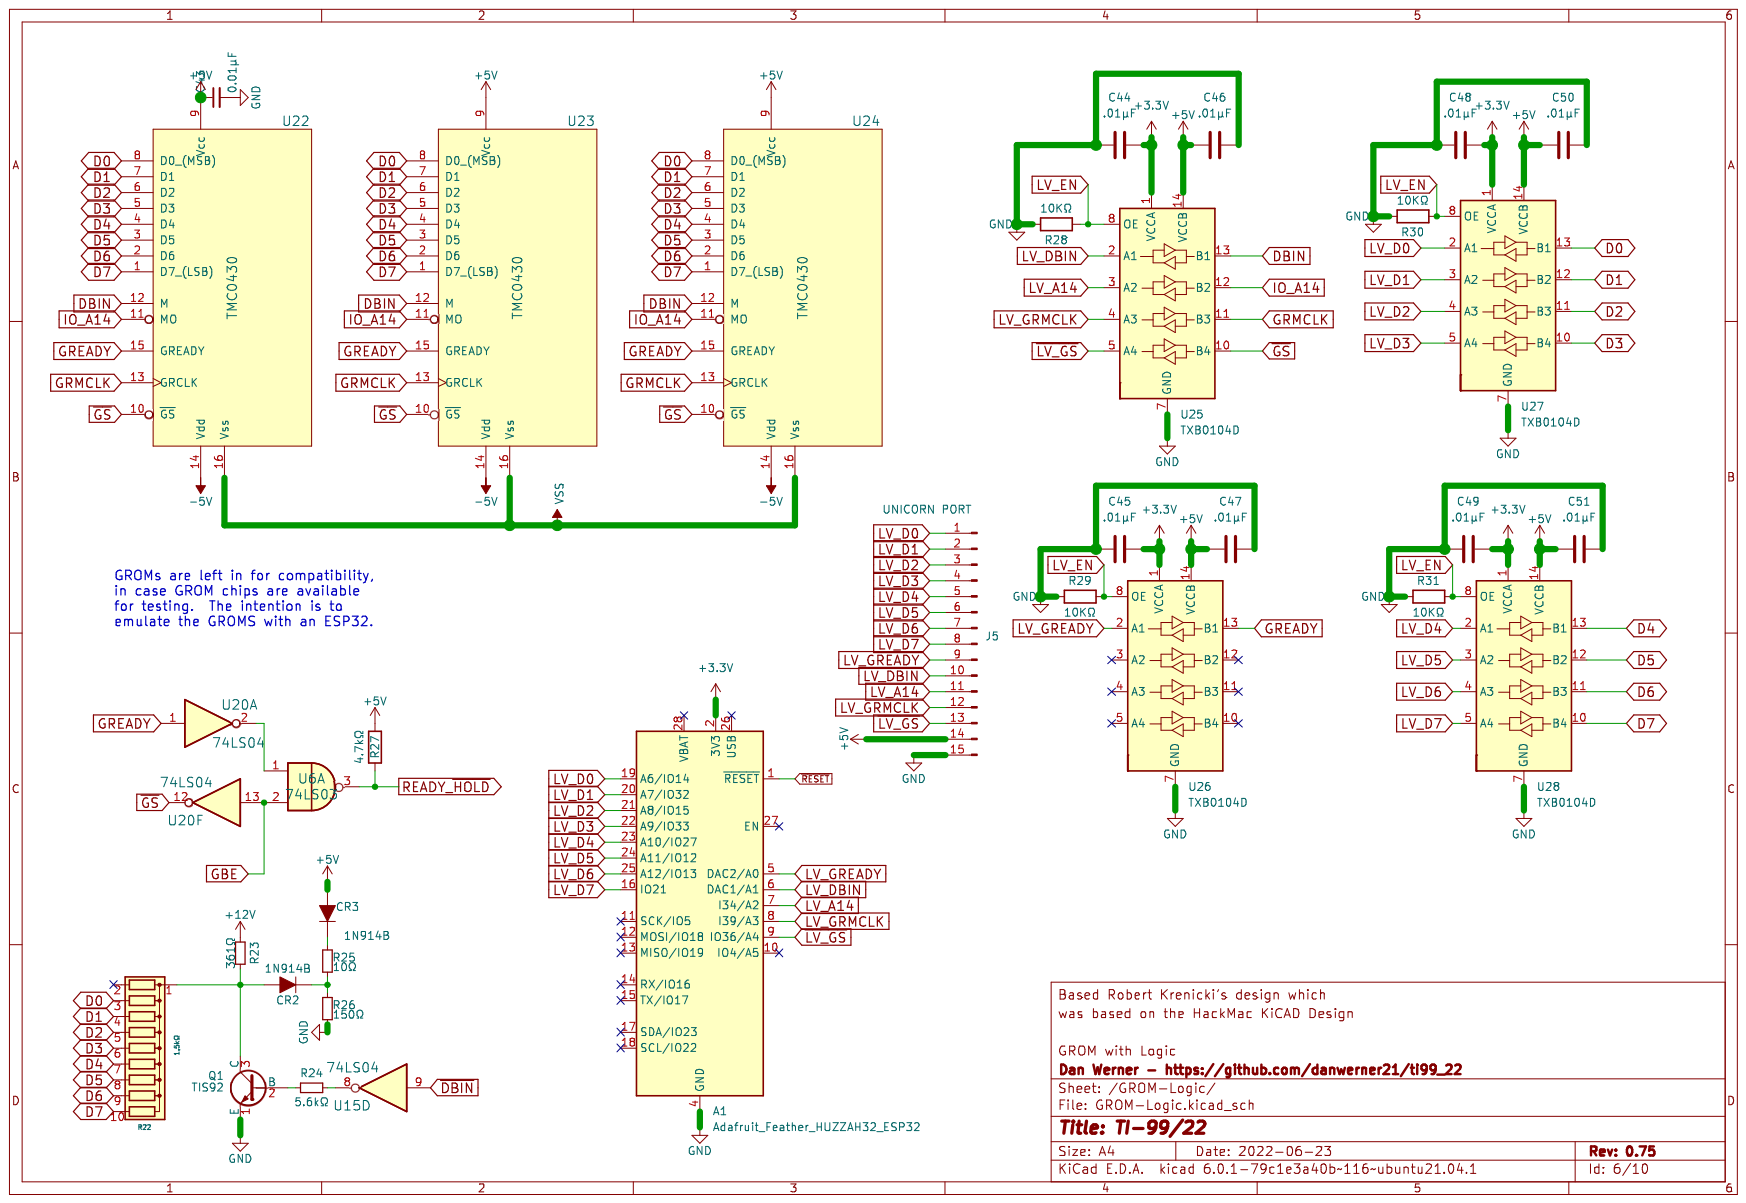
[picture p142: page 6]

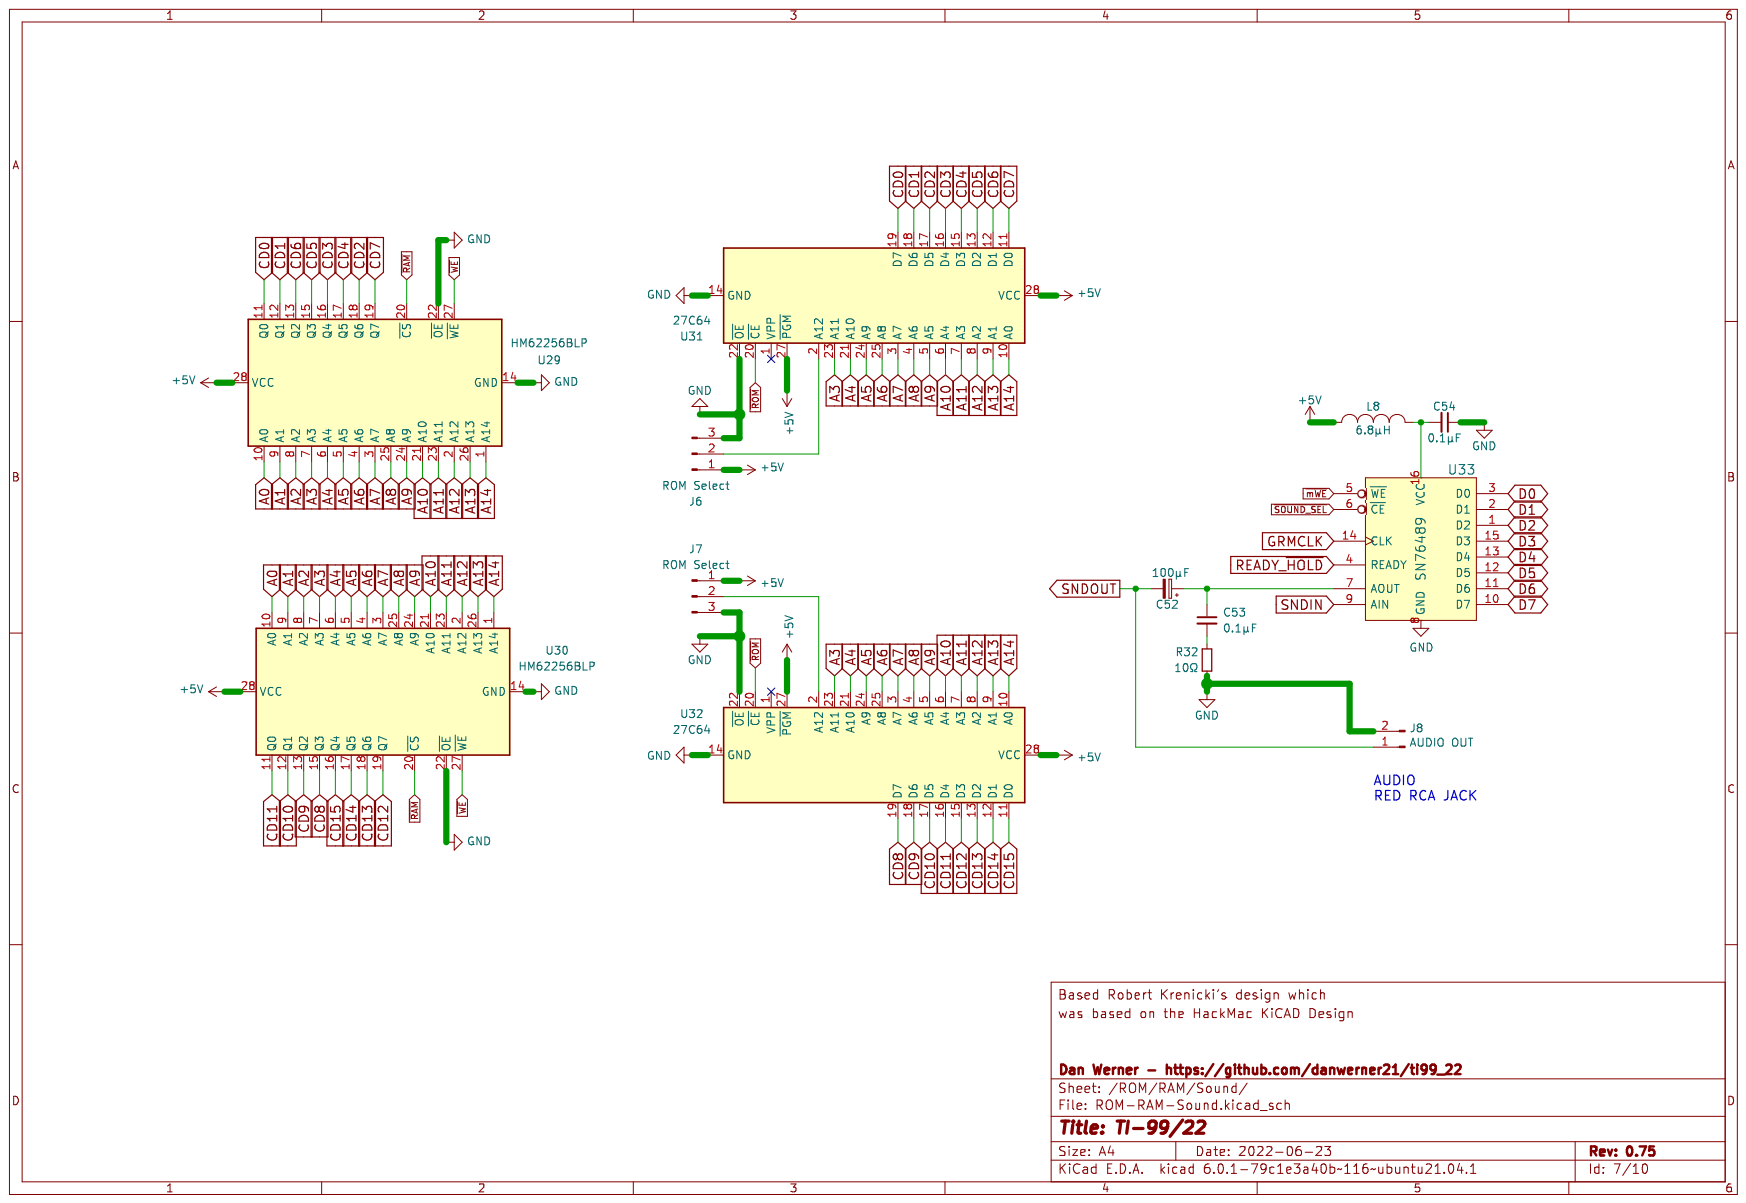
[picture p143: page 7]

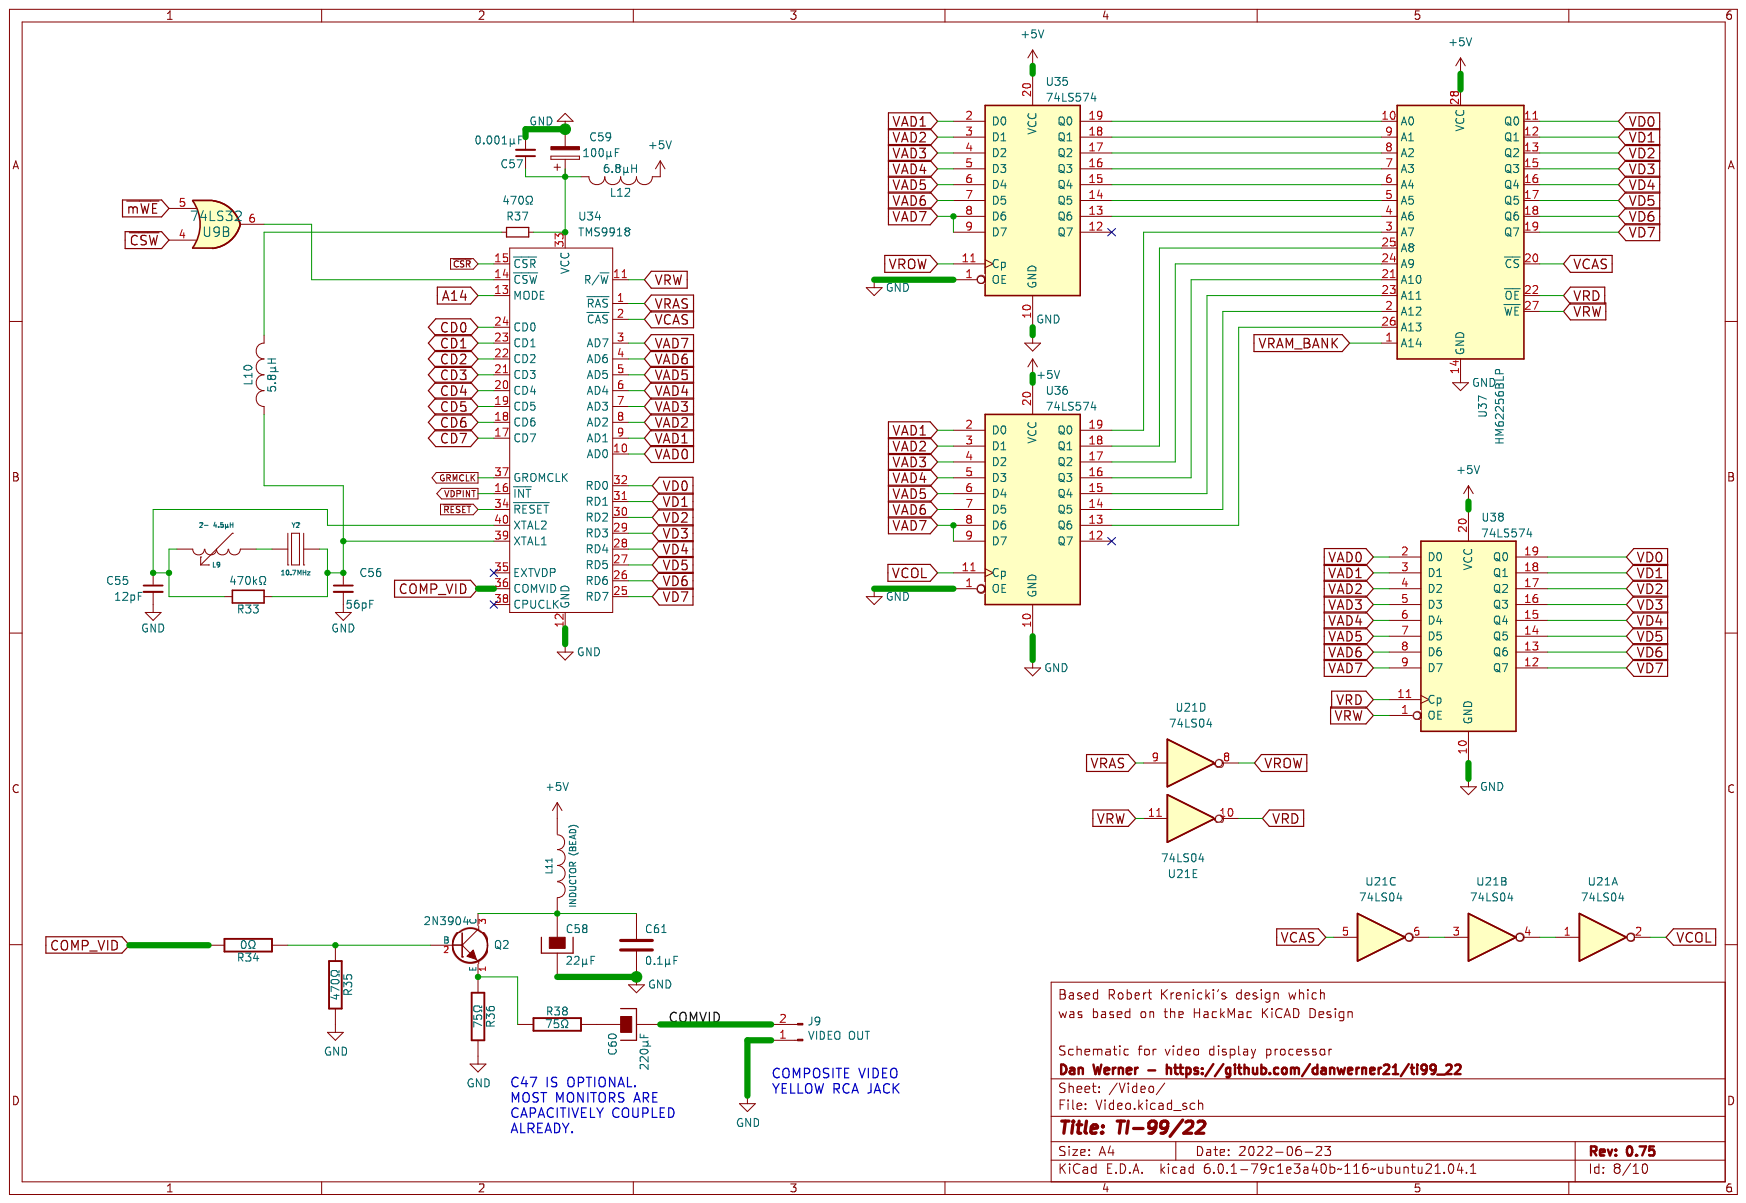
[picture p144: page 8]

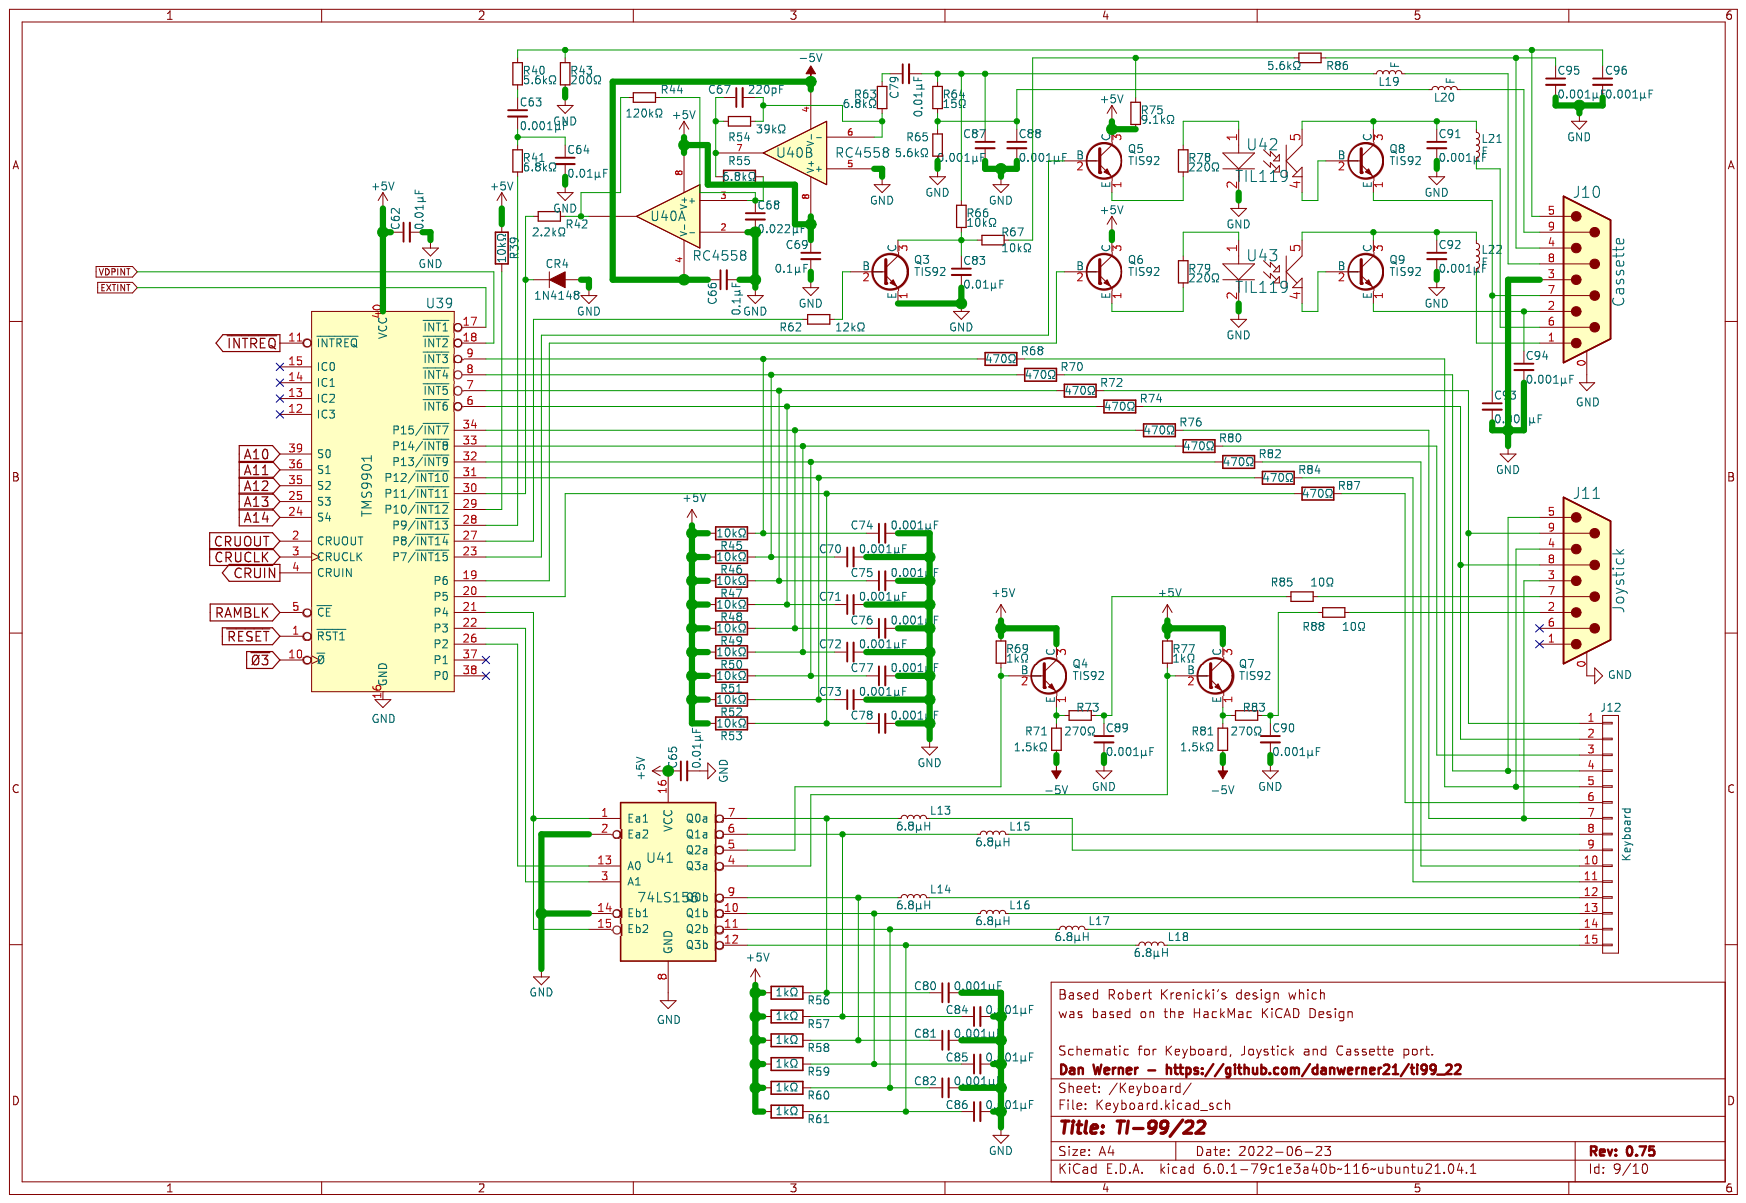
[picture p145: page 9]

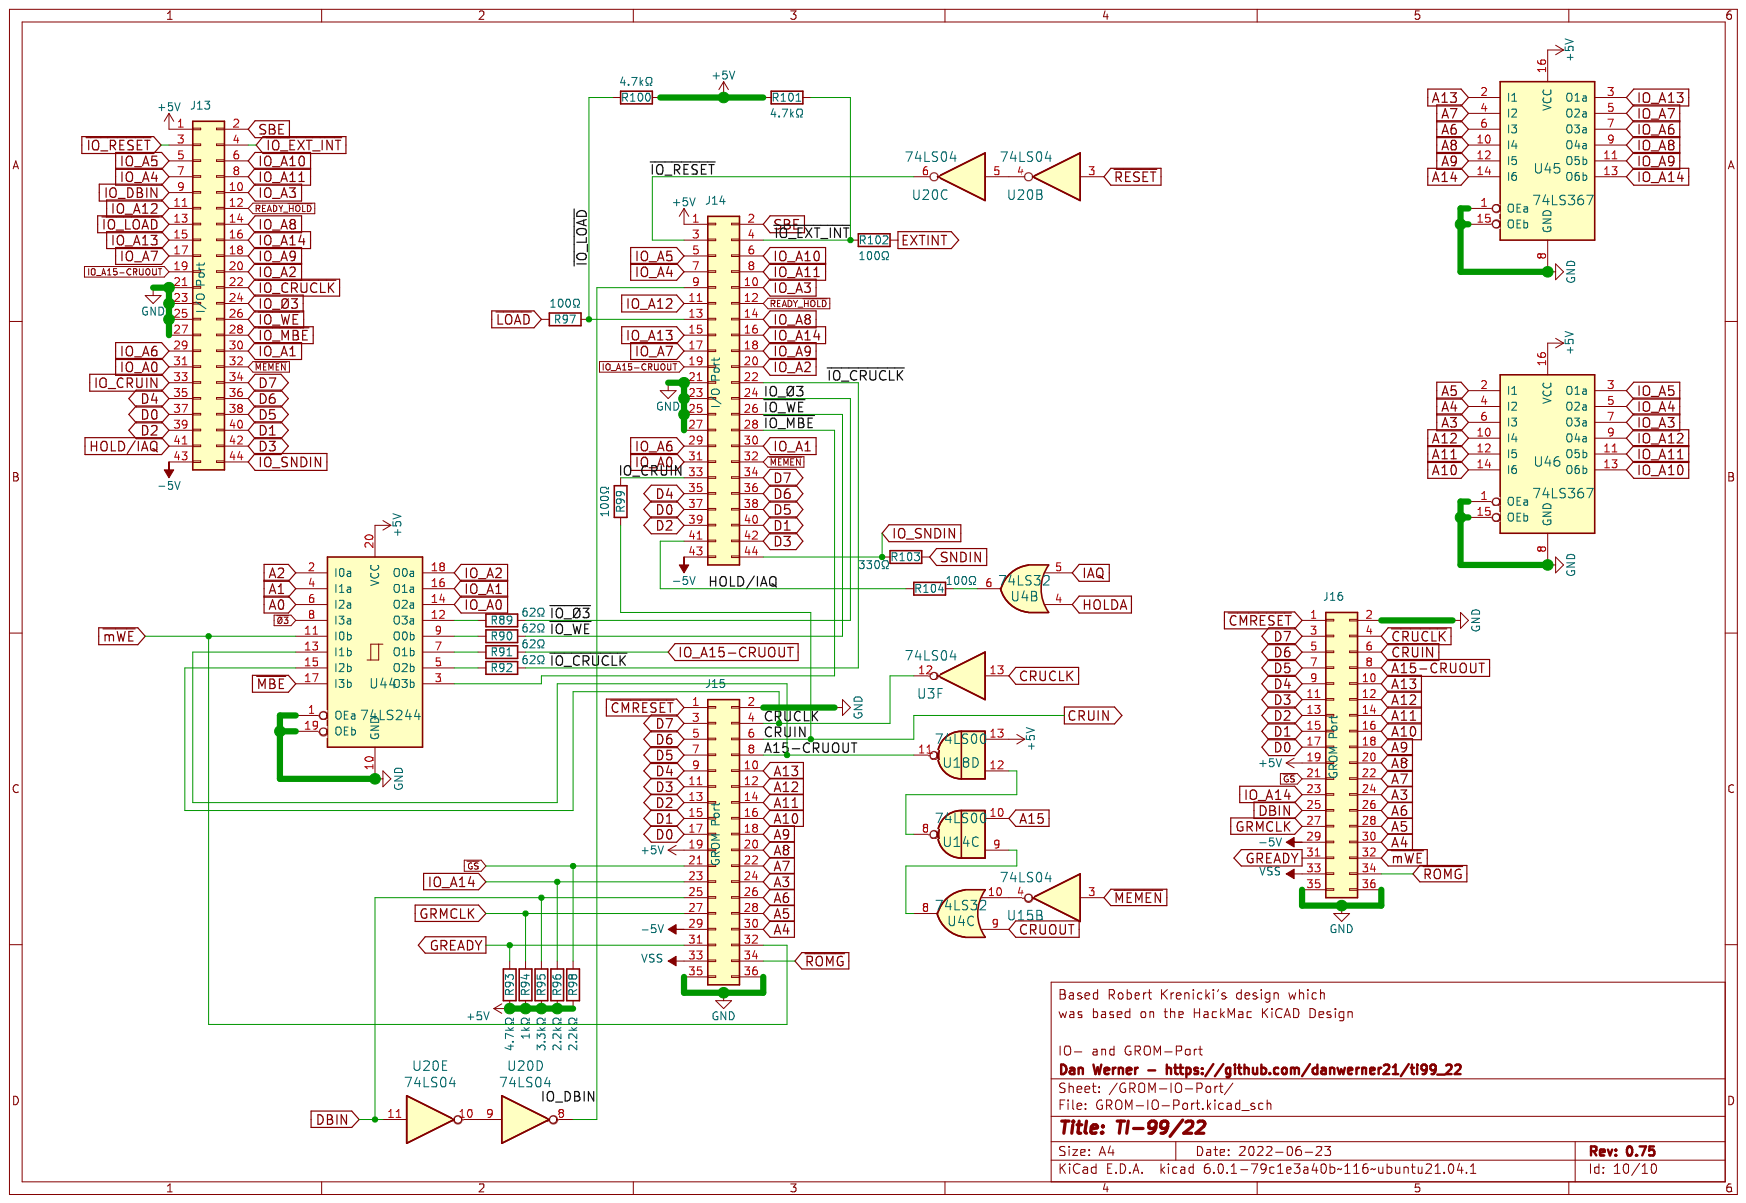
[picture p146: page 10]
