danwerner21/TI99_22/Keyboard/Keyboard_pcbV0.5.pdf

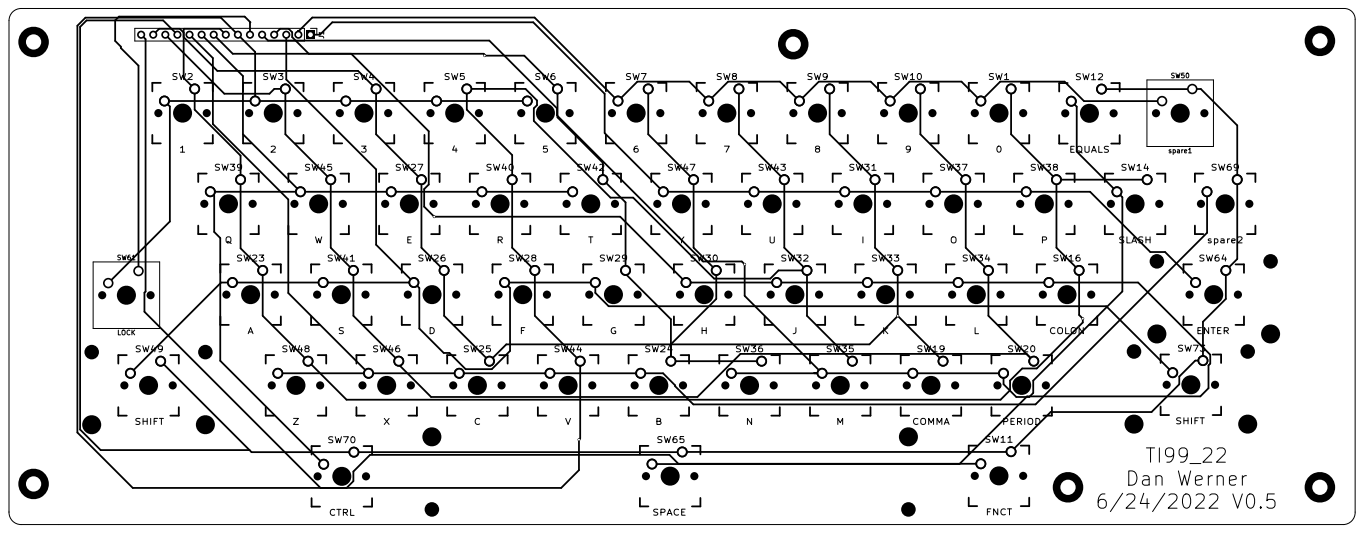
[picture p147: page 1]
