danwerner21/TI99_22/CartRiser/CartRiser/CART_RISER_V0.5.pdf

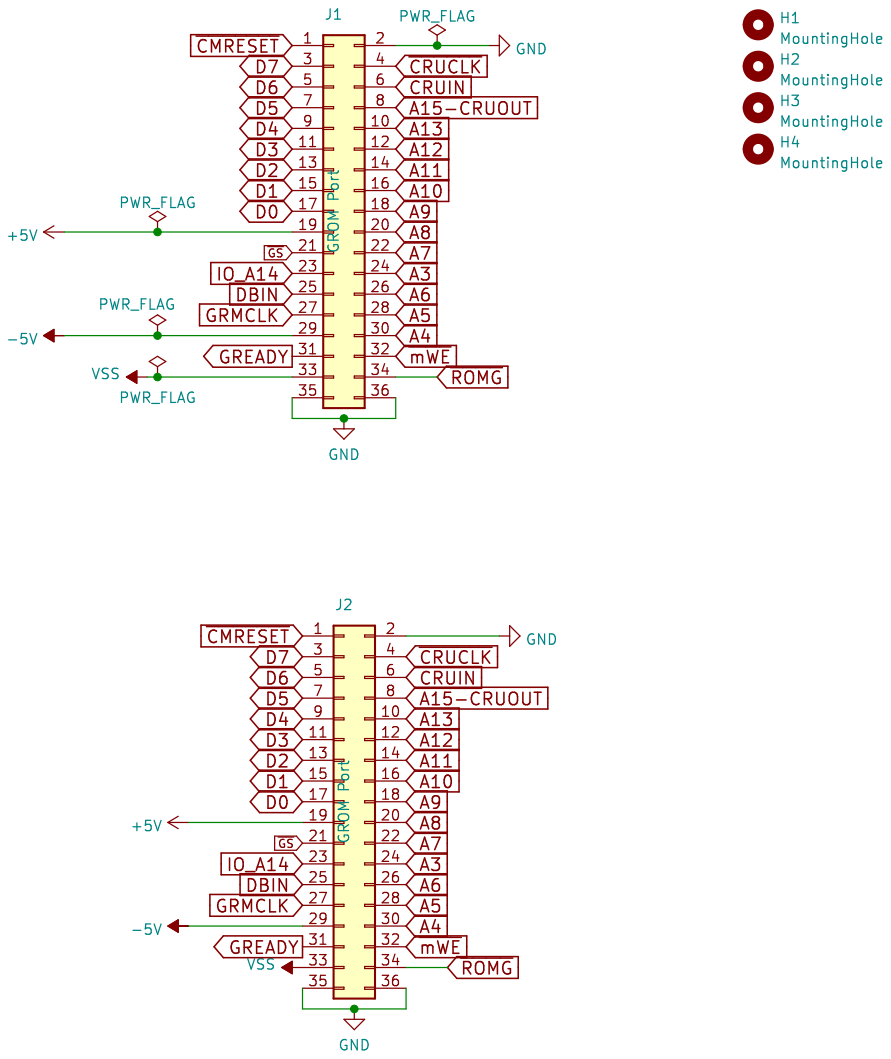
[picture p148: page 1]
