danwerner21/TI99_22/CartRiser/CartRiser/CART_RISERPCB_V0.5.pdf

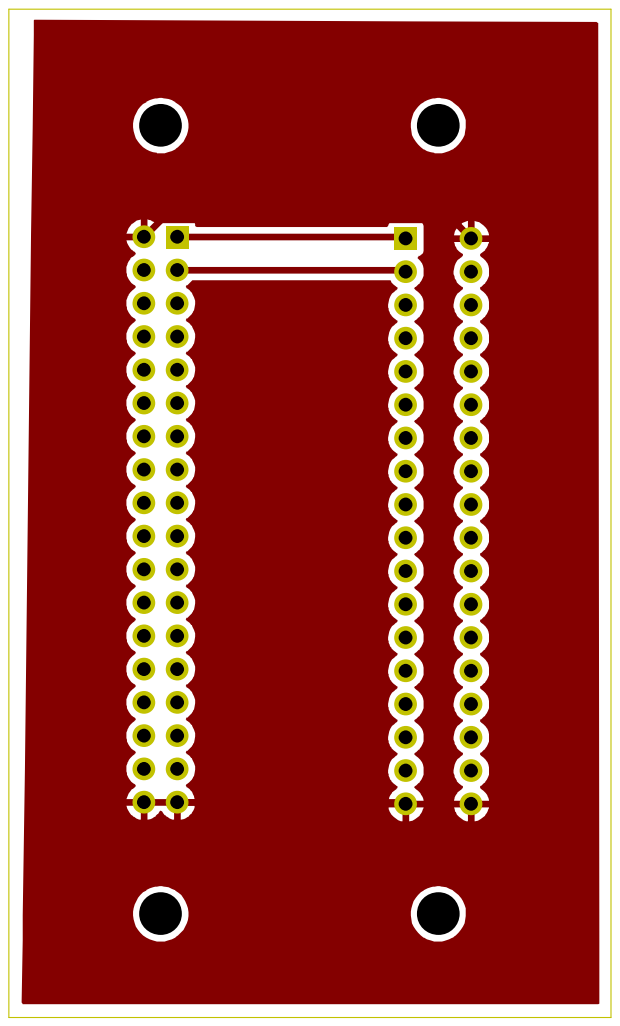
[picture p149: page 1]

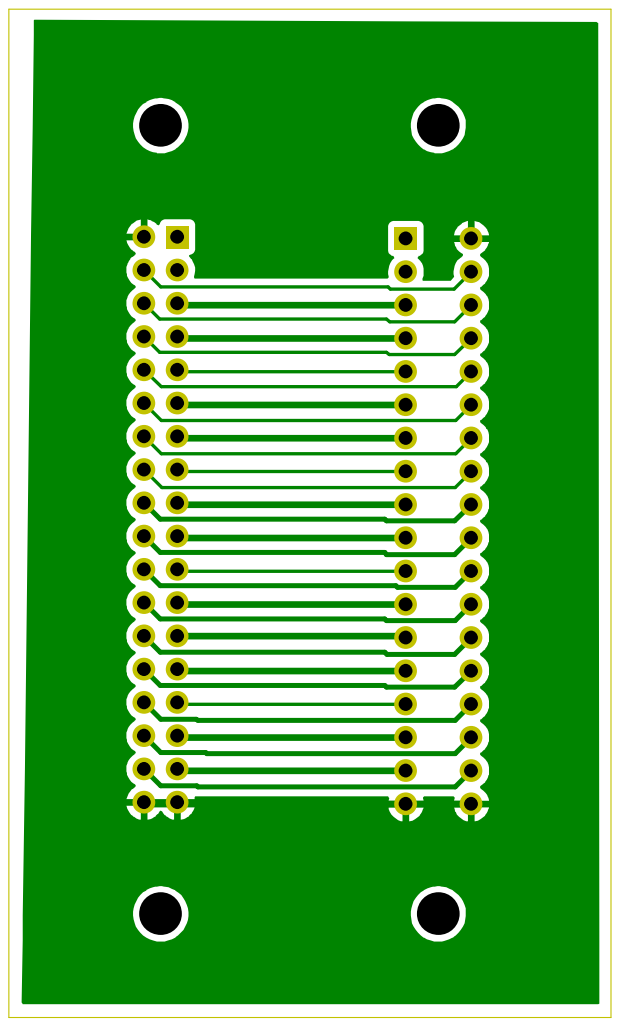
[picture p150: page 2]

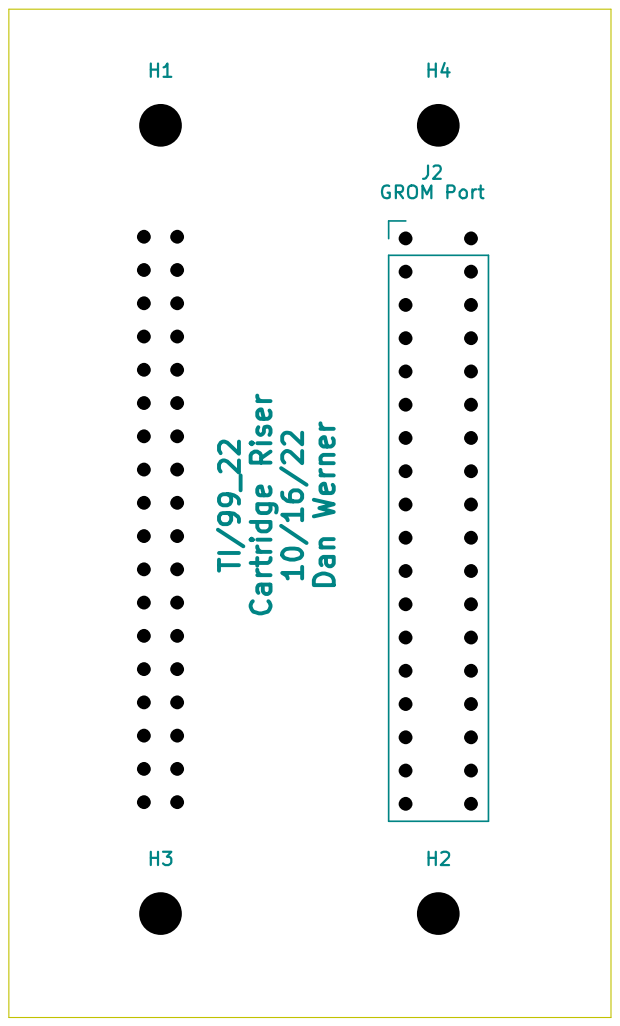
[picture p151: page 3]

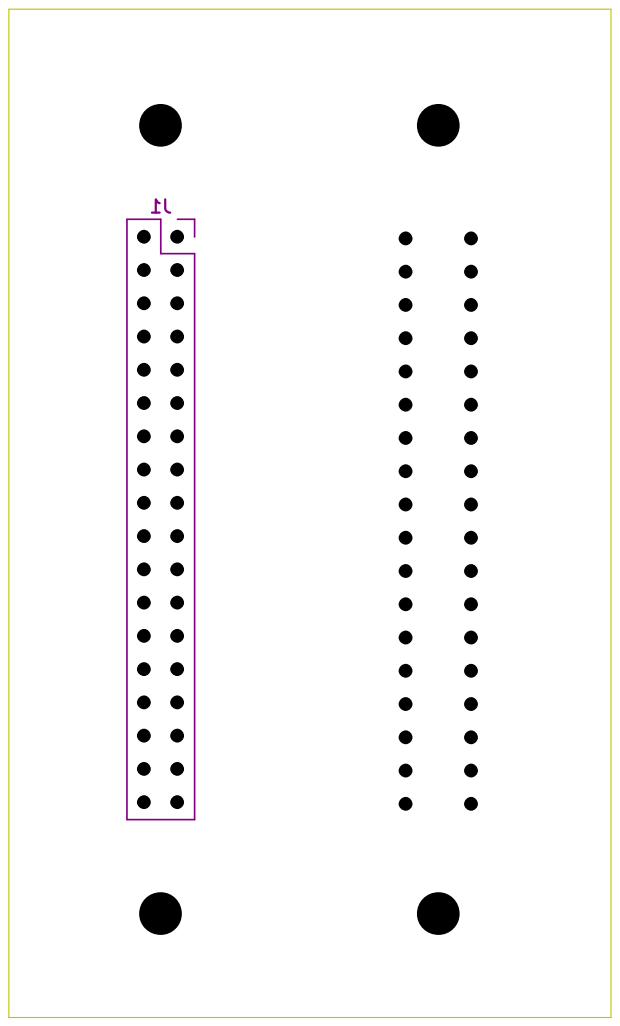
[picture p152: page 4]

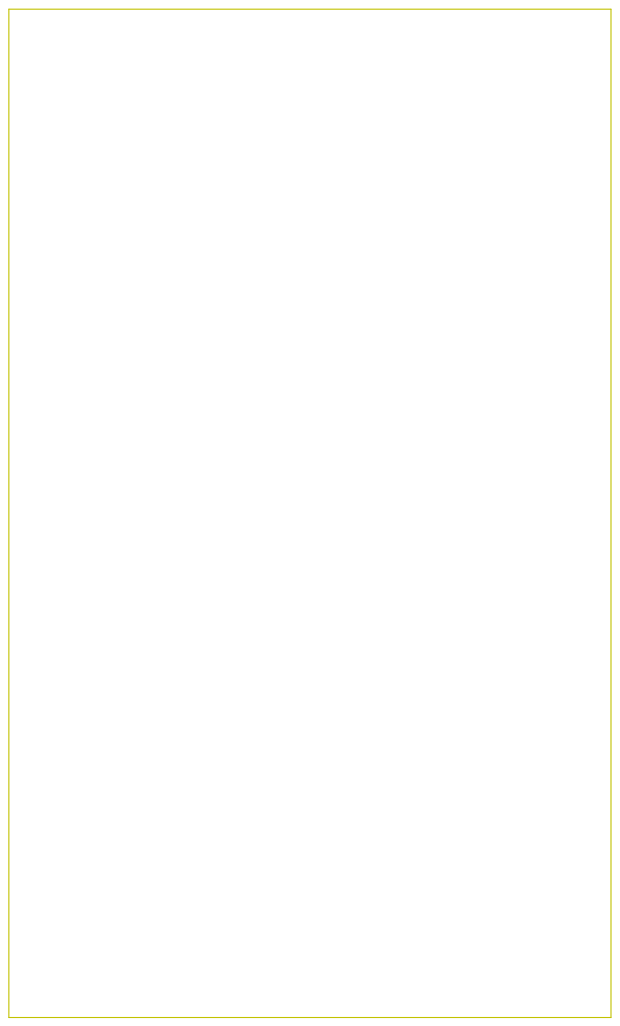
[picture p153: page 5]
