danwerner21/TI99_22/unicornboard/unicorn/UNICORN_PCB_V0.5.pdf

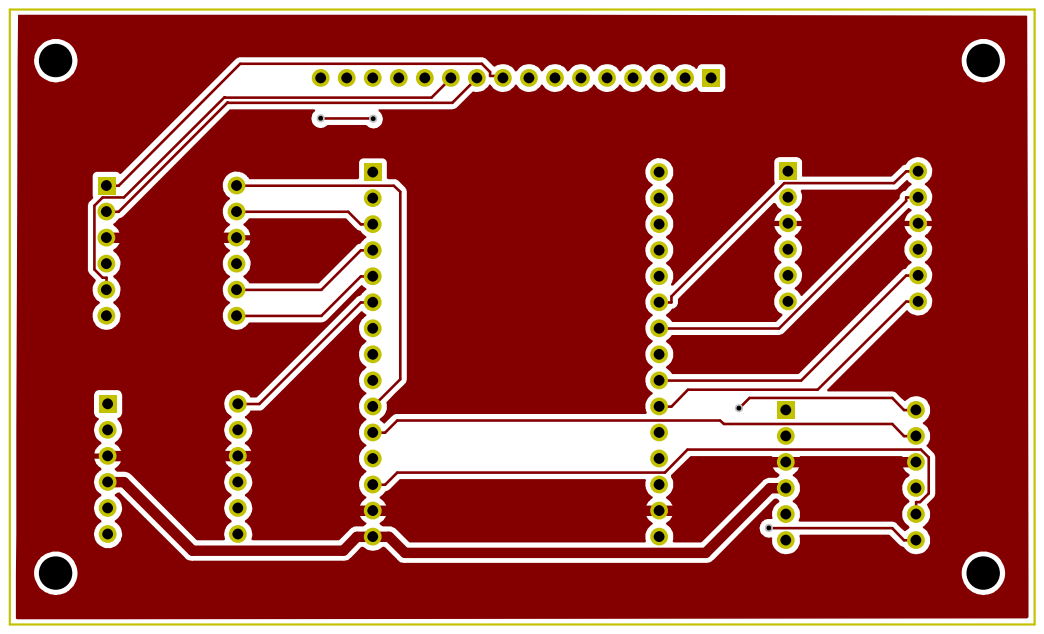
[picture p154: page 1]

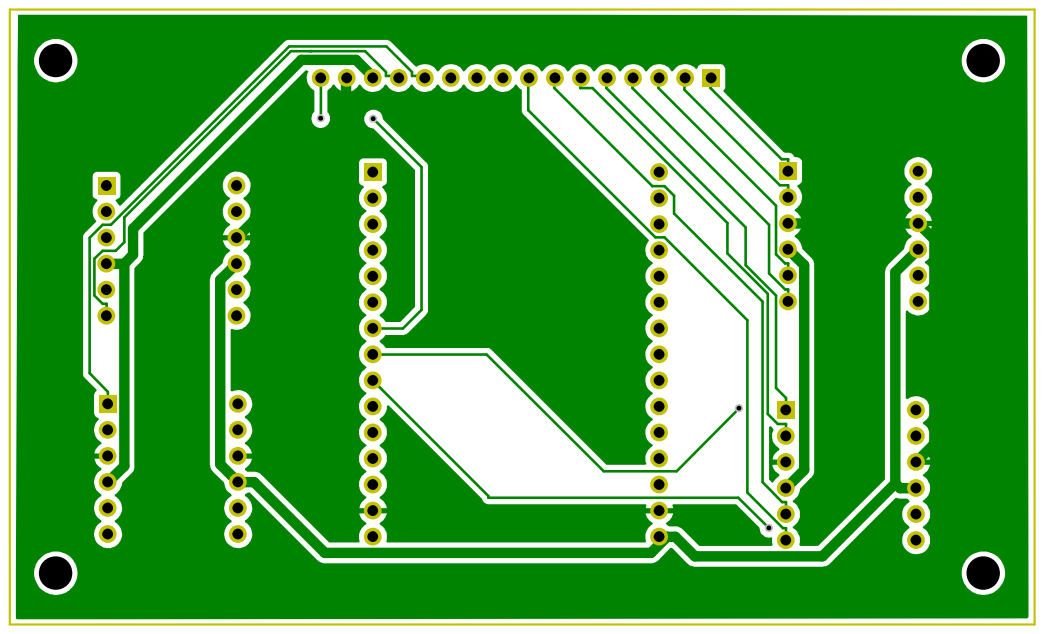
[picture p155: page 2]

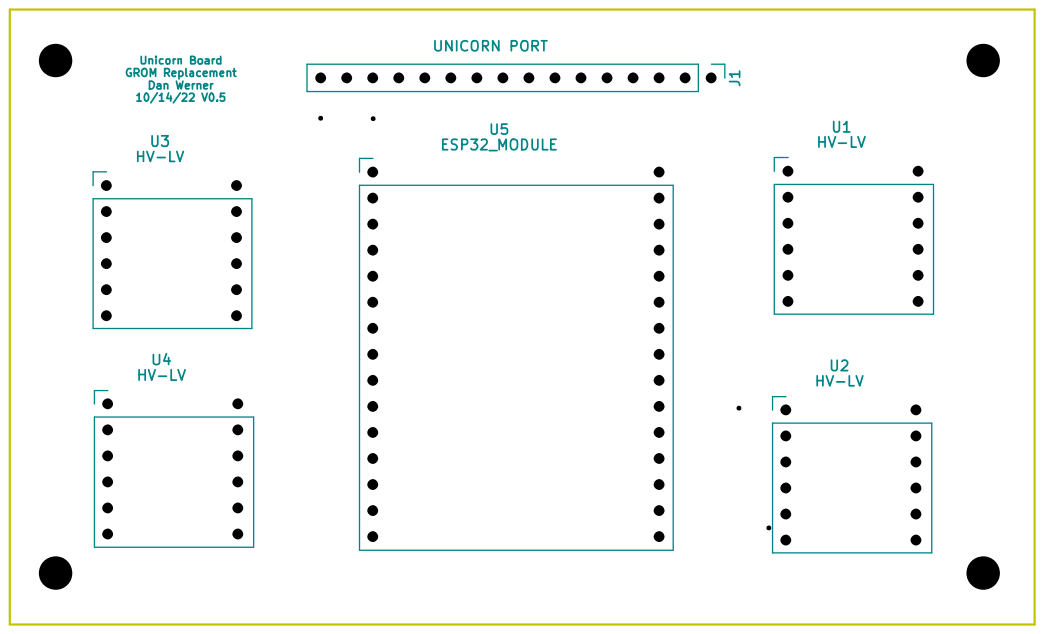
[picture p156: page 3]

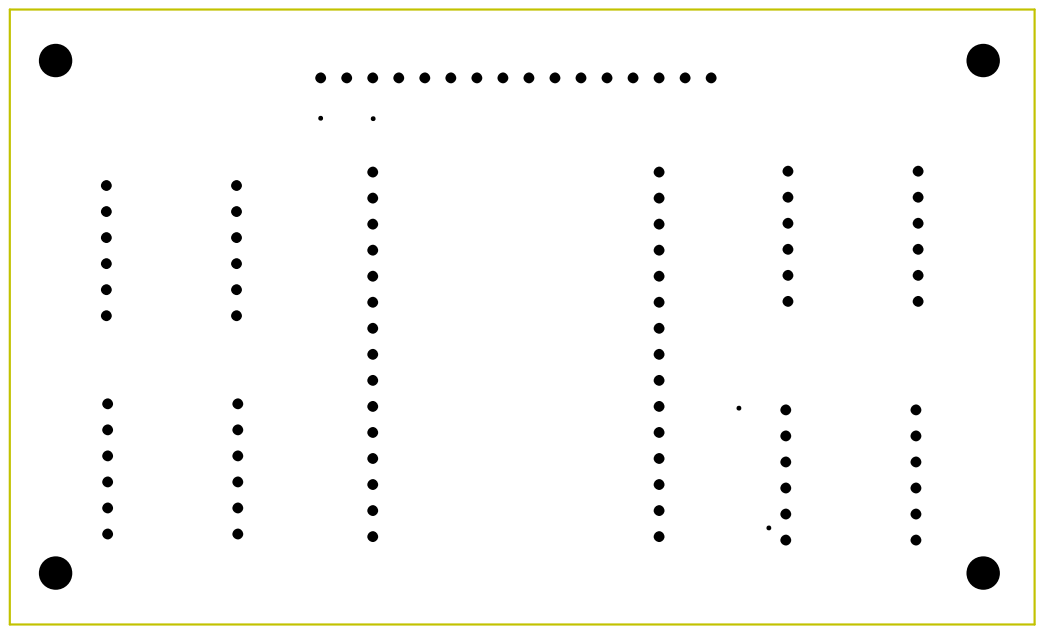
[picture p157: page 4]

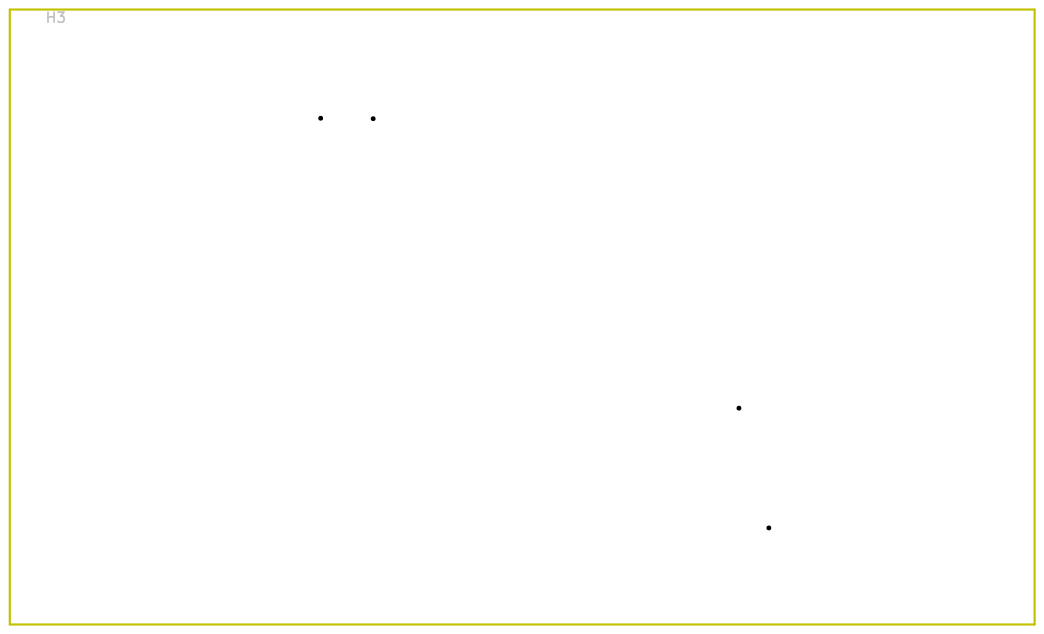
[picture p158: page 5]

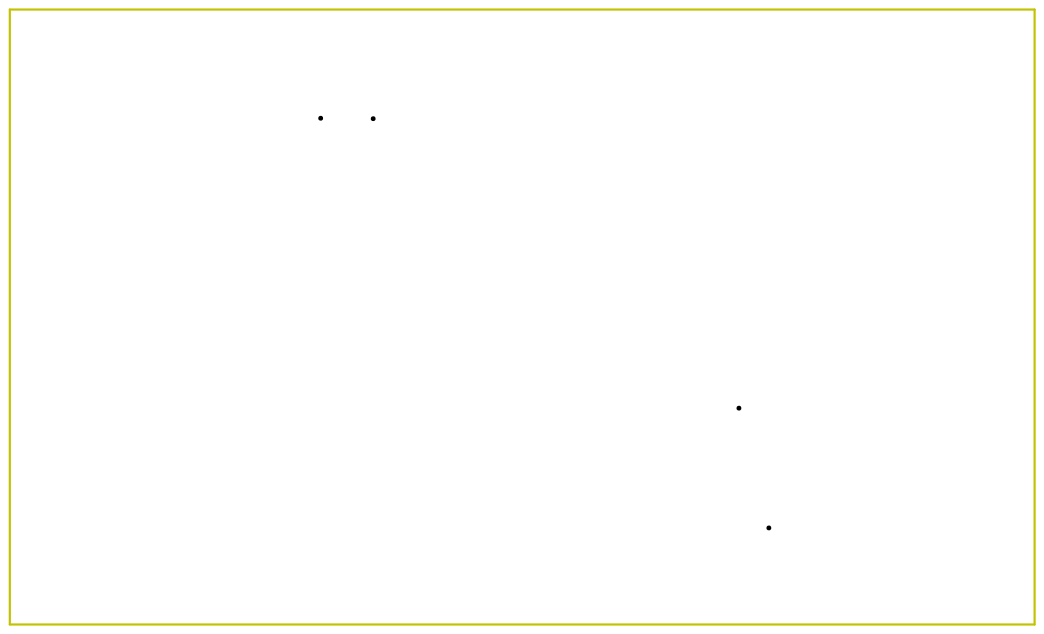
[picture p159: page 6]
