danwerner21/TI99_22/unicornboard/unicorn/UNICORN_V0.5.pdf

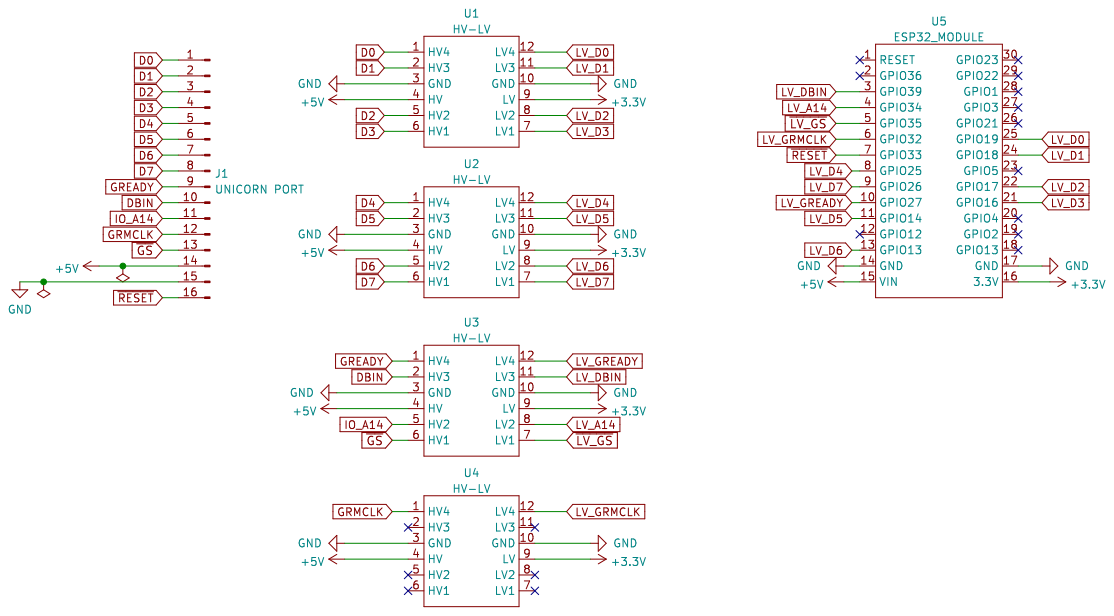
[picture p160: page 1]
